BrownDogGadgets/CrazyCircuits/Projects/LEGO Avoidance Tank/README.md

# LEGO Avoidance Tank

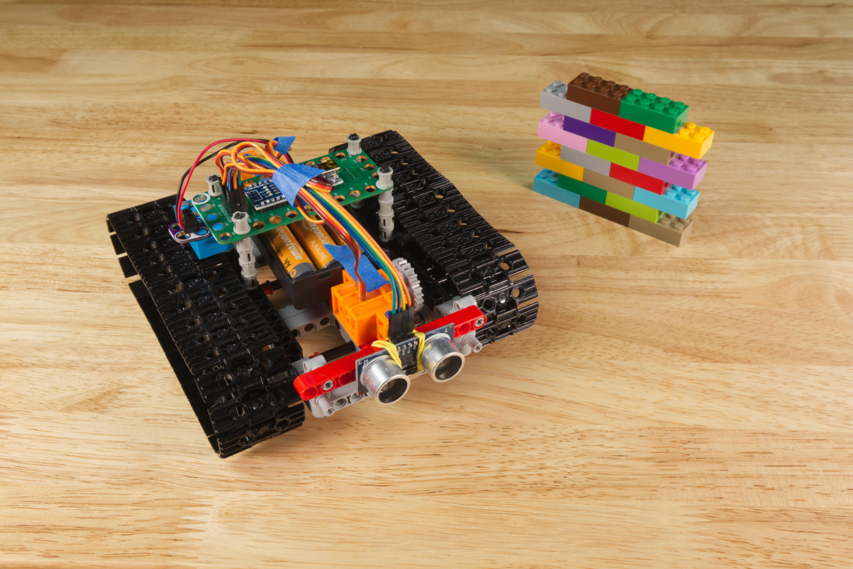
[picture p115: Projects/LEGO Avoidance Tank/Images/LEGO-Avoidance-Tank-2607.jpg]
LEGO Avoidance Tank


A LEGO Tank that uses an Ultrasonic Distance Sensor to prevent crashing into things.

Built with Crazy Circuits components and LEGO parts.

We have a full build guide listing all of the components and every LEGO part needed: https://browndoggadgets.dozuki.com/Guide/LEGO+Avoidance+Tank/383

The Arduino sketch `LEGO-Avoidance-Tank` is included.

You will also need the NewPing library, which can be found here: https://bitbucket.org/teckel12/arduino-new-ping/wiki/Home

---

Brown Dog Gadgets

https://www.browndoggadgets.com/
