BrownDogGadgets/CrazyCircuits/Projects/LEGO Hole Punch/README.md

# LEGO Hole Punch Stencils

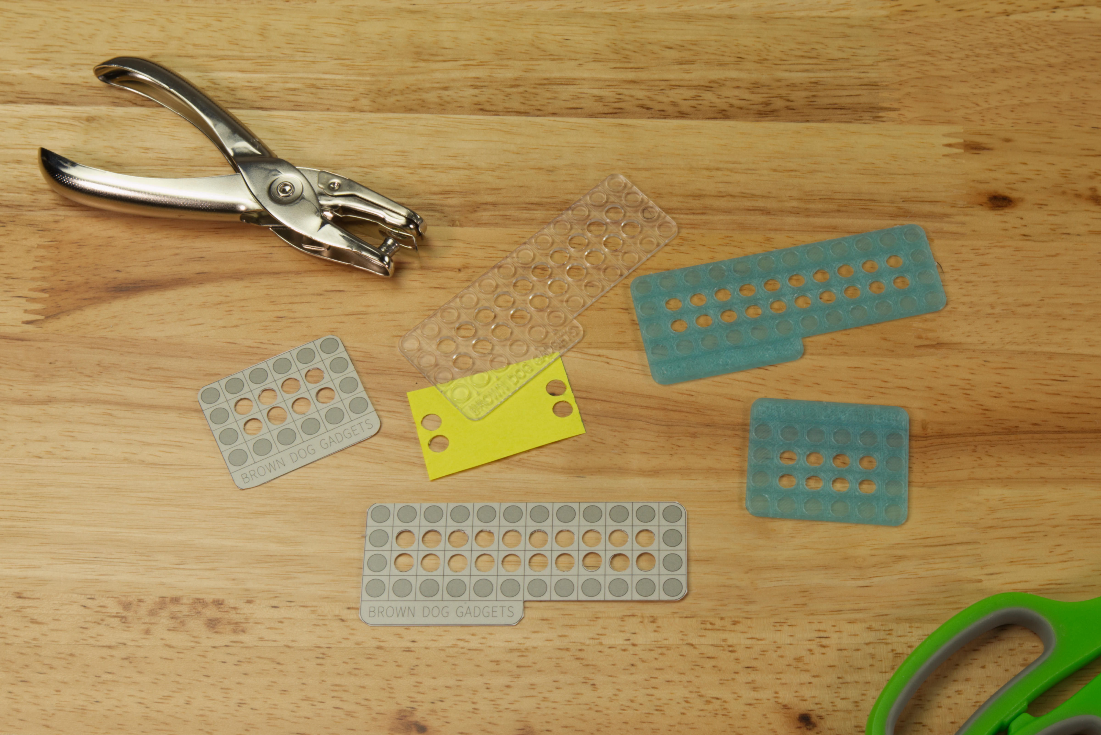
[picture p116: Projects/LEGO Hole Punch/Images/LEGO-Hole-Punch-Stencils.jpg]


A variety of LEGO Hole Punch Stencils suitable for laser cutting, 3D printing, or just printing on paper and cutting out.

Full Guide: https://browndoggadgets.dozuki.com/Guide/LEGO+Hole+Punch+Stencils/380

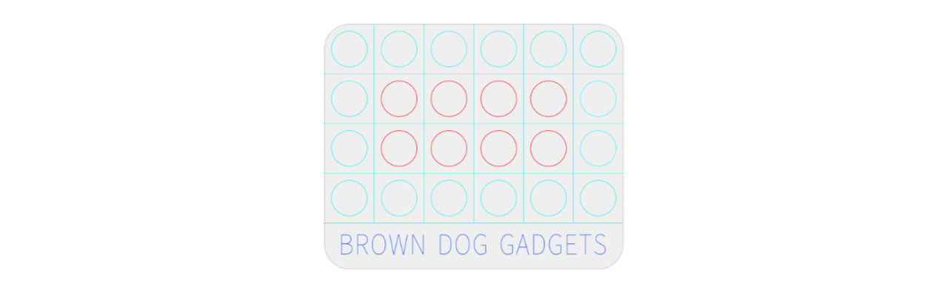
[picture p117: Projects/LEGO Hole Punch/Images/Laser.png]
Laser


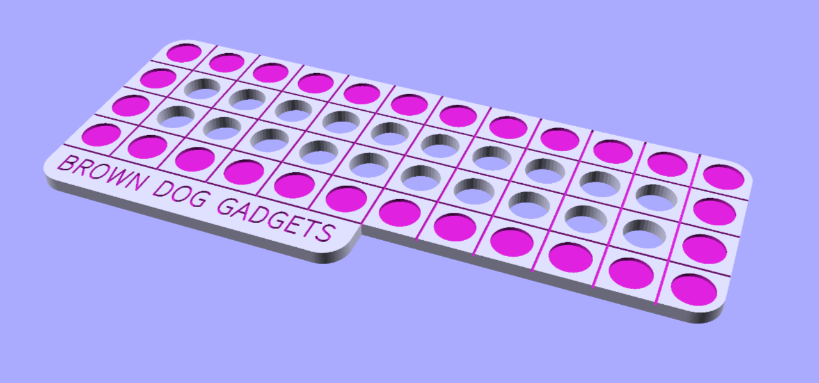
[picture p118: Projects/LEGO Hole Punch/Images/STL.png]
STL


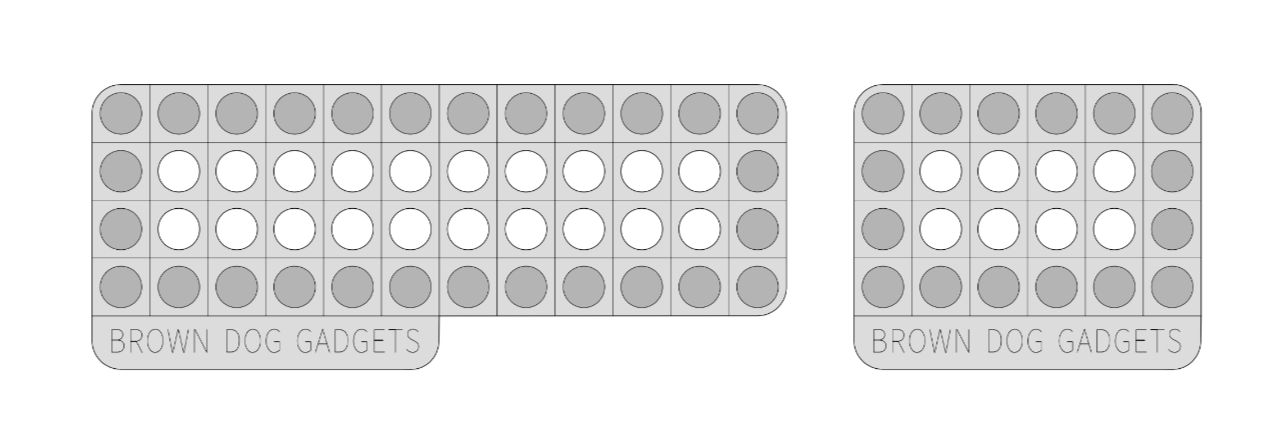
[picture p119: Projects/LEGO Hole Punch/Images/Paper.png]
Paper


---

Brown Dog Gadgets

https://www.browndoggadgets.com/
