BrownDogGadgets/CrazyCircuits/Projects/Arduino Maze/Readme.md

# Arduino LEGO Maze

This project uses the Crazy Circuits Robotics Board to activate a servo in a LEGO maze.

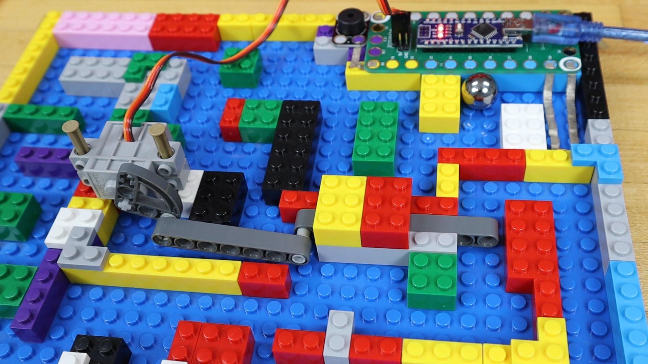
[picture p120: Projects/Arduino Maze/legomaze.jpg]
LEGO Maze


Overall this is a very simple project. We're using two pieces of Maker Tape conductive tape to act as our switch and then using a metal ball bearing to activitive the switch, which in turn activates the servo.

To add some extra fun to the activity we also added in a Piezo Speaker as a countdown timer.

In the example picture we're using a LEGO friendly Geek Servo, through there are many different DIY LEGO Adaptors that can be laser cut and 3D printed for a standard 9G servo.

See the full build guide: https://browndoggadgets.dozuki.com/Guide/LEGO+Maze/68

---

Brown Dog Gadgets

https://www.browndoggadgets.com/
