BrownDogGadgets/CrazyCircuits/Projects/CLUEbell/README.md

# CLUEbell

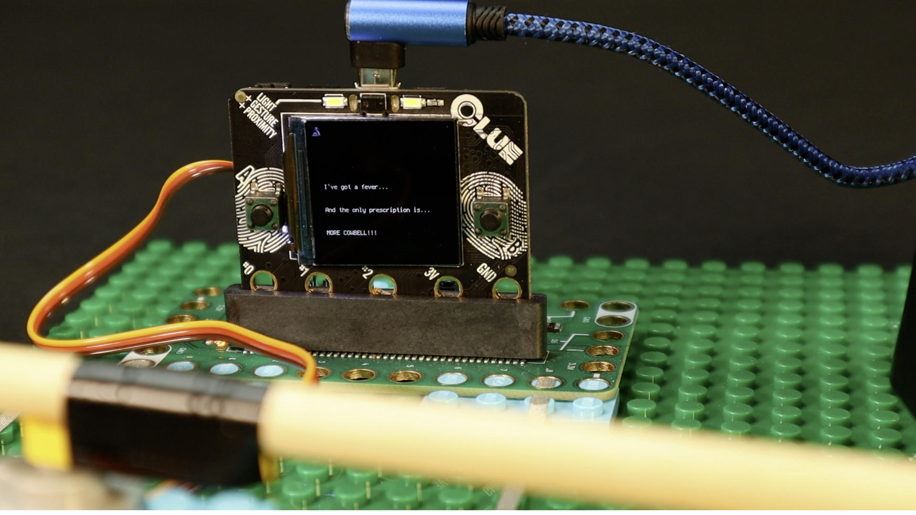
[picture p121: Projects/CLUEbell/Images/cluebell-01.jpg]


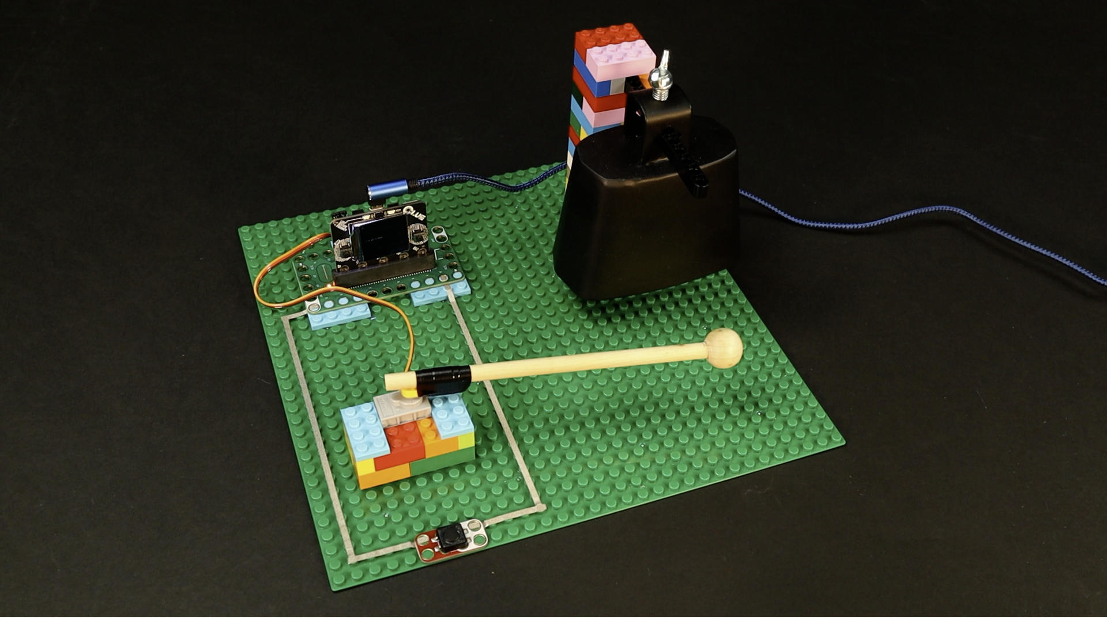
[picture p122: Projects/CLUEbell/Images/cluebell-02.jpg]


The **CLUEbell** is a Crazy Circuits LEGO-based project using a Bit Board and an Adafruit Clue.

## Adafruit Clue

The code is written in CircuitPython and to use it as-is just copy it to the Clue after you connect it to your computer with a USB cable.

This is based on our "Automatic Cowbell" project: https://browndoggadgets.dozuki.com/Guide/Automatic+Cowbell/361

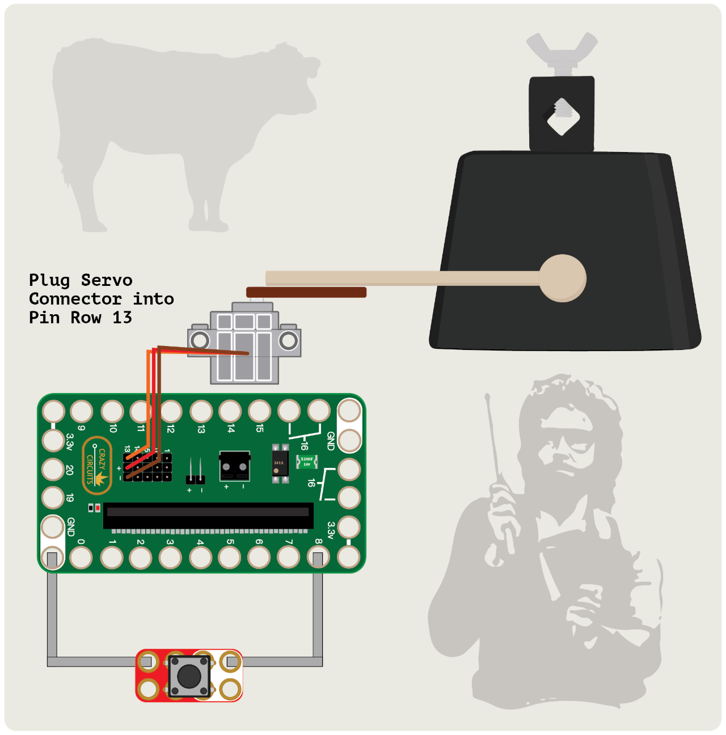
[picture p123: Projects/CLUEbell/Diagrams/cluebell-circuit.png]


---

Brown Dog Gadgets

https://www.browndoggadgets.com/
