BrownDogGadgets/CrazyCircuits/Projects/L-egg-o Egg Decorating Robot/README.md

# L-egg-o Egg Decorating Robot

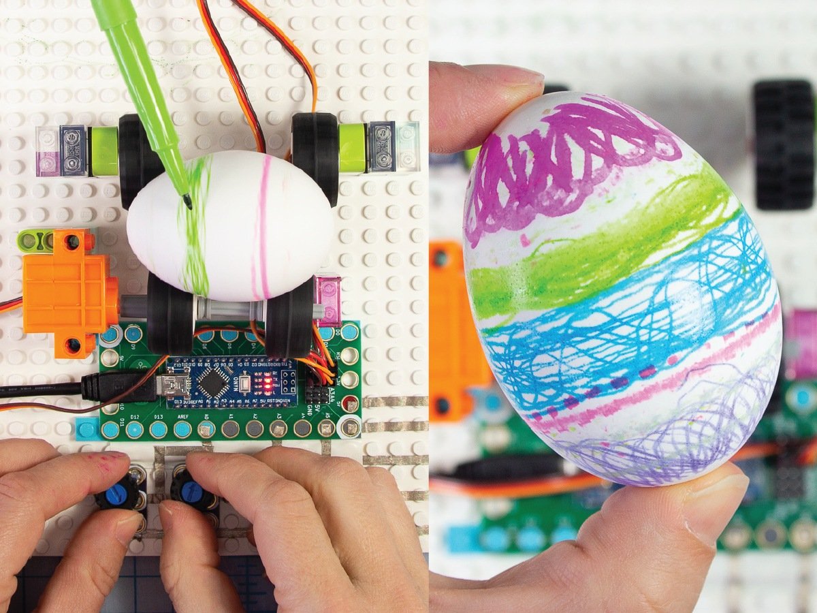
[picture p130: Projects/L-egg-o Egg Decorating Robot/Images/l-egg-o-decobot.jpg]


Full instructions here: https://browndoggadgets.dozuki.com/Guide/"L-egg-o"+Egg+Decorating+Robot/175

You'll need to use the Arduino sketch `Leggo_Mazing_Smooth.ino`

(https://www.youtube.com/watch?v=7hJQVjtKovQ)

---

Brown Dog Gadgets

https://www.browndoggadgets.com/
