BrownDogGadgets/CrazyCircuits/Projects/SquishySound/readme.md

Two sets of noise making code for a simple Squishy Circuits sound project.

Use a Touch or Robotics Board, a Piezo Speaker, and a Screw Terminal with a 460 ohm resistor. (Or a resistor close to it.)

Attach alligator clips and use dough to change the sounds.
