BrownDogGadgets/CrazyCircuits/Projects/Touch LED/readme.md

# Crazy Touch LED

This is a simple sketch that uses four Touch Points and 4 LED outputs.

Touch a Touch Point and one of the LEDs turns on.

We designed this to be used with conductive dough as a demo project, though any conductive material would work.  You could easily modify this code to do various effects.

The code run an auto calibration sequence when turned on.  This means you should wait three seconds after powering up before touching any of the touch points.

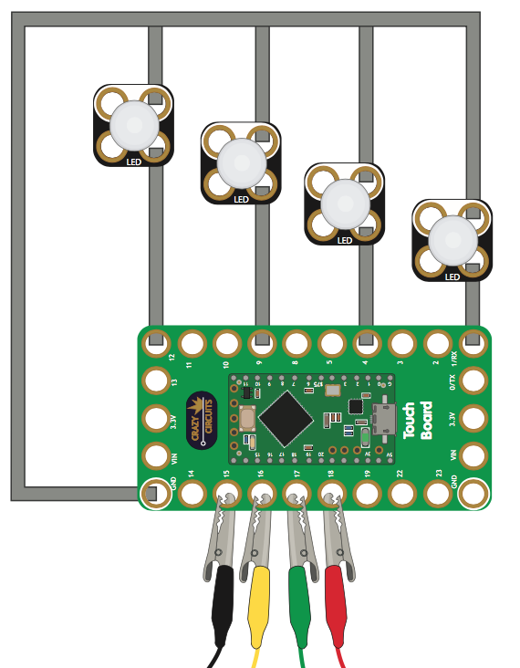
[picture p134: Projects/Touch LED/diagrampreview.png]
diagram preview
