BrownDogGadgets/CrazyCircuits/Projects/LEGO Fidget/readme.md

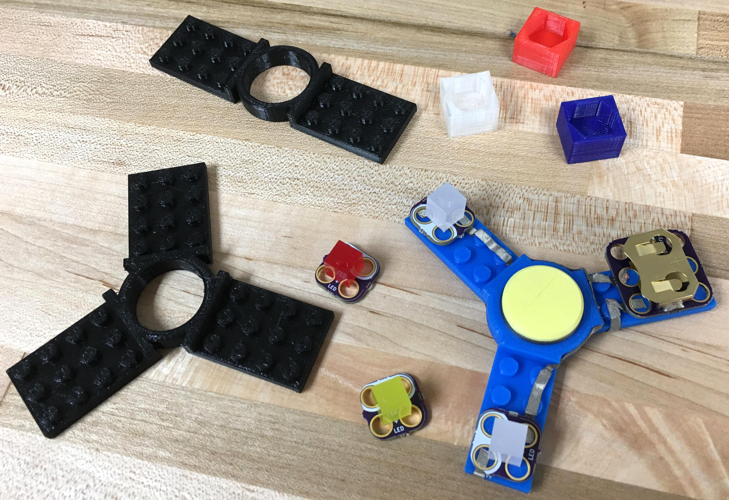
[picture p140: Projects/LEGO Fidget/spinners.jpg]


# 3D Printed LEGO Fidget Spinner

In this project we're going to use a 3D Printer to create our own custom fidget spinner, then attach Crazy Circuits parts to make it light up. We've provided several different variations to print with, changing the number of arms and the number of LEGO studs on them. There are also some additional files for adding in M8 sized Nuts as weights.

Obviously you're going to need access to a 3D printer, but if you don't one readily available you can always use online services such as Shapeways to make one for you. We used our office Makerbot Replicator 2 for printing, with a print time of around 45 minutes for a three armed spinner. If the studs are too big or too small you'll have to change the size and try again, same goes for the bearing.

We used two Cazy Circuits LEDs, a CR2032 Battery Holder, and some tape. Be sure to use two of the same color LED otherwise power will only flow through one color. (Voltage differences in different colors of LEDs can cause issues with CR2032 batteries.)

It IS possible to use a Blink/ Fade board with some of the larger 3D files, but would require some tricky tape work.

You will need to "patch" some of the tape lines in order to connect them.  This means folding over the end of a piece of tape to electricly connect everything, and then putting another piece of tape on top to hold it down. For more information on the basic of Crazy Circuits please visit

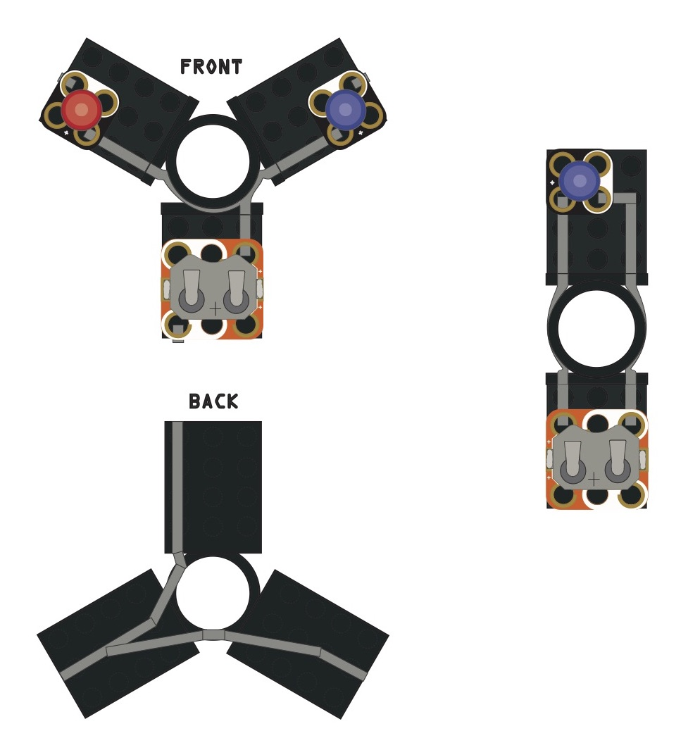
[picture p141: Projects/LEGO Fidget/WiringDiagram.jpg]


Like all good fidget spinners ours requires a 608 bearing, also known as a Skate Bearing. There are many varieties available on Amazon. For a bearing cover you can choose from a wide variety of available 3D models on Thingiverse. We used files from [this spinner](https://www.thingiverse.com/thing:1802260), but had to reduce the size a couple percentage points.
