BrownDogGadgets/CrazyCircuits/Laser Cut Files/NES Controller/readme.md

These are the laser cut files for the DIY NES Controller.

The code and building tips can be found in the Projects area of this repository.
