BrownDogGadgets/CrazyCircuits/Circuit-Kits/Modules/6x11-Raspi-Pico-Robot-Version/README.md

<!--- start title --->
# 5x11 Raspberry Pi Pico Robot Breakout v1.6
A Lego-compatible Crazy Circuits module

- Updated: 24 Sep 2018
- Website: http://browndoggadgets.com/
- Company: Brown Dog Gadgets
- License: CERN Open Hardware License v1.2.
<!--- end title --->

This robot controller module comes with an Arduino Nano, four servo headers, and two analog headers. 

We recommend buying two 20-pin Harwin connectors (P/N [M20-9992046](https://www.digikey.com/products/en?keywords=M20-9992046)) and breaking it into pieces to place the six male headers.

<!--- bom start --->
## Bill of Materials

|Ref|Qty|Description|Digikey PN|
|---|---|---|---|
|J1-6|6|HEADER MALE 3POS TH 1x03 0.1IN|952-2264-ND|
|U1|1|Raspberry Pi PICO Board|2648-SC0915CT-ND|

<!--- bom end --->

### Manufacturing Notes

This board must be v-scored. Do not panelize with support tabs or mousebites.

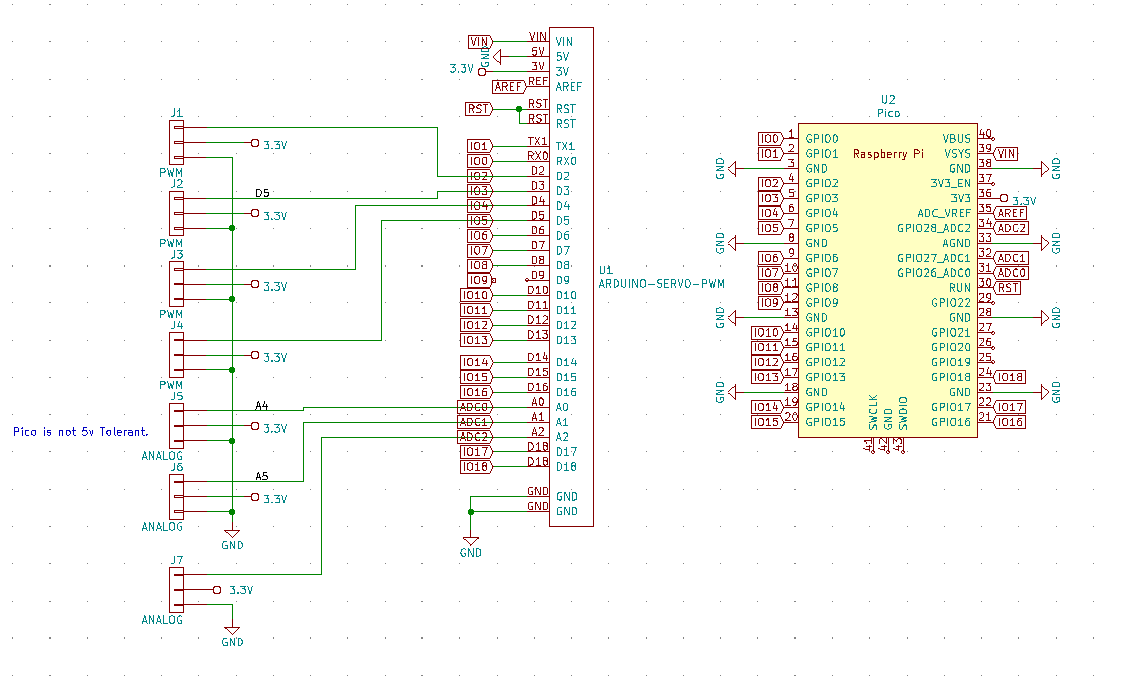
[picture p145: Circuit-Kits/Modules/6x11-Raspi-Pico-Robot-Version/schematic.png]
Assembly and Schematic


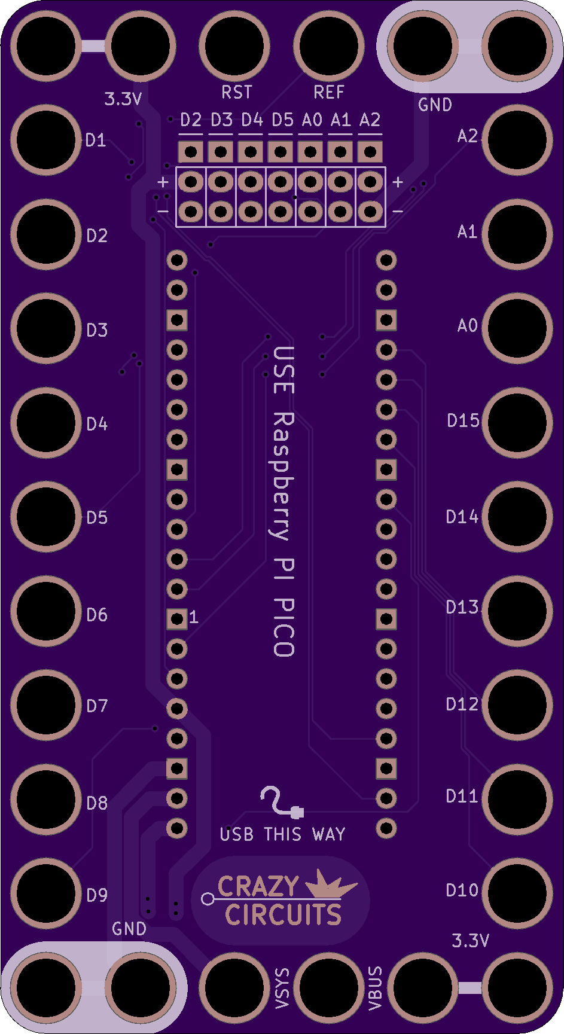
[picture p146: Circuit-Kits/Modules/6x11-Raspi-Pico-Robot-Version/top.png]
 
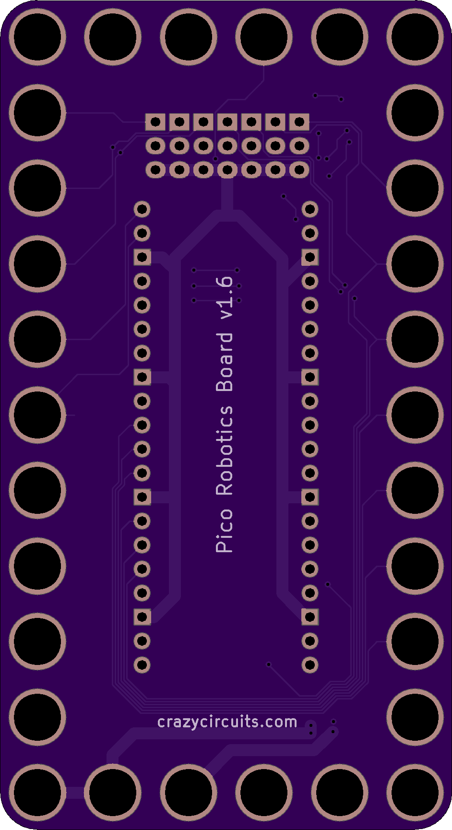
[picture p147: Circuit-Kits/Modules/6x11-Raspi-Pico-Robot-Version/bot.png]
