BrownDogGadgets/CrazyCircuits/Circuit-Kits/Modules/3x4-ATtiny85-8SOIC-Breakout/README.md

<!--- start title --->
# 3x4 ATtiny85 8SOIC Breakout Module v1.3
A Lego-compatible Crazy Circuits module

- Updated: 25 Sep 2018
- Website: http://browndoggadgets.com/
- Company: Brown Dog Gadgets
- License: CERN Open Hardware License v1.2.
<!--- end title --->

This is a breakout board for an ATiny85, a tiny microcontroller. 

<!--- bom start --->
## Bill of Materials

|Ref|Qty|Description|Digikey PN|
|---|---|---|---|
|U1|1|IC MCU 8BIT ATTINY85 8SOIC|ATTINY85-20SU-ND|

<!--- bom end --->

### Manufacturing Notes

This board must be v-scored. Do not panelize with support tabs or mousebites.

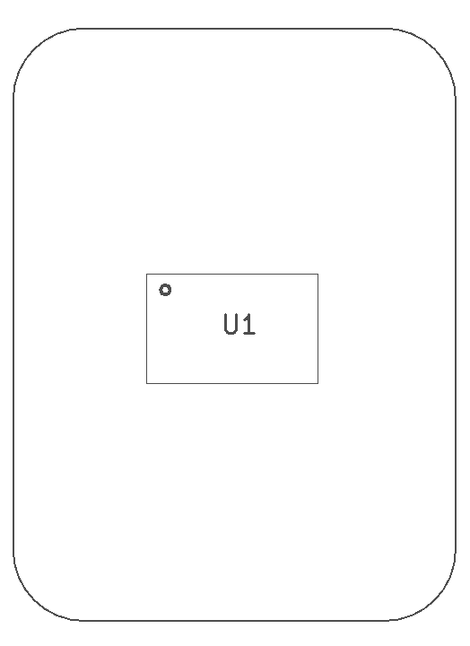
[picture p163: Circuit-Kits/Modules/3x4-ATtiny85-8SOIC-Breakout/assembly.png]
Assembly Diagram


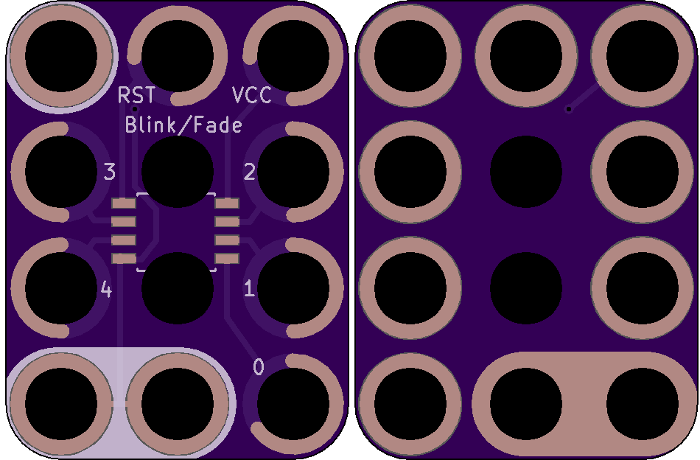
[picture p164: Circuit-Kits/Modules/3x4-ATtiny85-8SOIC-Breakout/preview.png]
Gerber Preview
