BrownDogGadgets/CrazyCircuits/Circuit-Kits/Modules/2x3-Dark-Detector/README.md

<!--- start title --->
# 2x3 Dark Detector Module v1.0
A Lego-compatible Crazy Circuits module

- Updated: 24 Sep 2018

- Website: http://browndoggadgets.com/
- Company: Brown Dog Gadgets
- License: CERN Open Hardware License v1.2
<!--- end title --->

This circuit applies 3V to turn a transistor on and off, based on whether the on-board photocell detects light. The output will go high if there is no light.

<!--- bom start --->
## Bill of Materials

|Ref|Qty|Description|Digikey PN|
|---|---|---|---|
|LDR1|1|PHOTOTRANSISTOR FLAT BK MINI SMD|1080-1383-1-ND|
|Q1|1|TRANS NPN 40V 0.2A SOT-23|MMBT3904TPMSCT-ND|
|R1|1|RES SMD 100K OHM 5% 1/10W 0603|311-100KGRCT-ND|

<!--- bom end --->

### Manufacturing Notes

This board must be v-scored. Do not panelize with support tabs or mousebites.

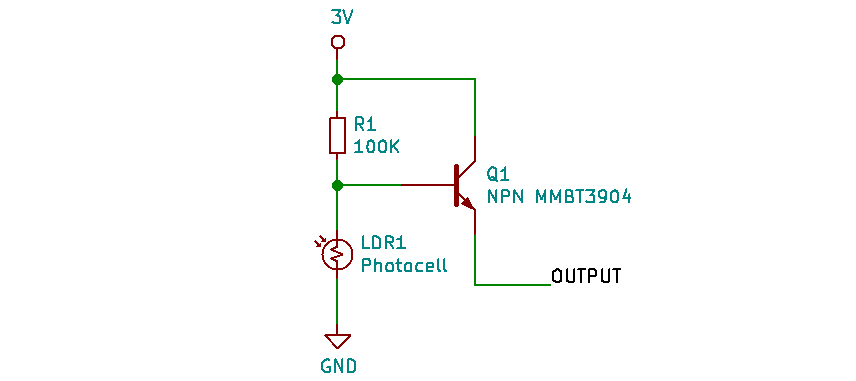
[picture p165: Circuit-Kits/Modules/2x3-Dark-Detector/schematic.png]
Schematic


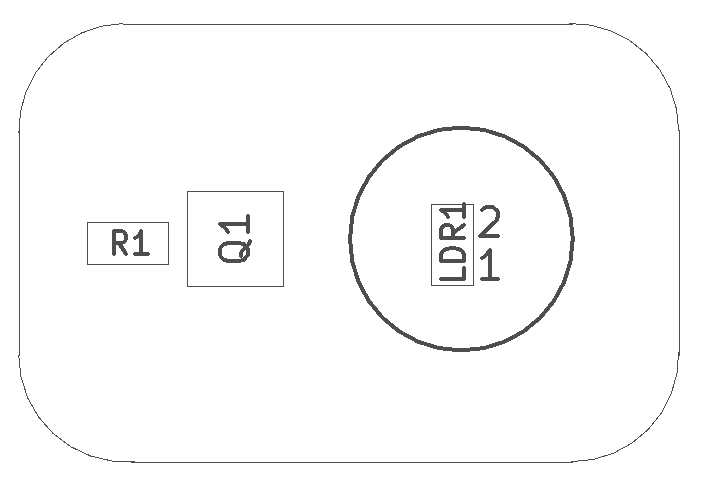
[picture p166: Circuit-Kits/Modules/2x3-Dark-Detector/assembly.png]
Assembly Diagram


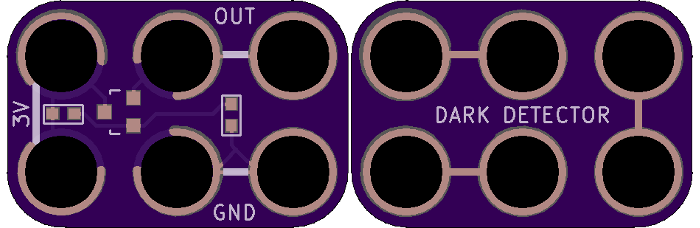
[picture p167: Circuit-Kits/Modules/2x3-Dark-Detector/preview.png]
Gerber Preview
