BrownDogGadgets/CrazyCircuits/Circuit-Kits/Modules/2x2-LED-RGB-NeoPixel-SMT/README.md

<!--- start title --->
# 2x2 LED RGB Neopixel (WS2812B) Module v1.1
A Lego-compatible Crazy Circuits module

- Updated: 24 Sep 2018

- Website: http://browndoggadgets.com/
- Company: Brown Dog Gadgets
- License: All rights reserved.
<!--- end title --->

The WS2812B is an RGB LED that's addressable using the Adafruit Neopixel library for Arduino. Neopixels can be chained together by connecting the DOUT pin of one Neopixel to the DIN pin of the next Neopixel.

An onboard 0.1uF capacitor protects the Neopixel from the controller and the 470-ohm resistor on DIN helps the microcontroller talk reliably to the Neopixel.

Find strings, strands, and rings of Neopixels at [Adafruit](http://adafruit.com).

<!--- bom start --->
## Bill of Materials

|Ref|Qty|Description|Digikey PN|
|---|---|---|---|
|C1|1|CAP CER 0.1UF 16V X7R 0603|490-4774-1-ND|
|LED1|1|LED RGB WS2812B W/DVR 4SMD|1528-1104-ND|
|R1|1|RES SMD 470 OHM 5% 1/4W 0603|RHM470DCT-ND|

<!--- bom end --->

### Manufacturing Notes

This board must be v-scored. Do not panelize with support tabs or mousebites.

Schematic

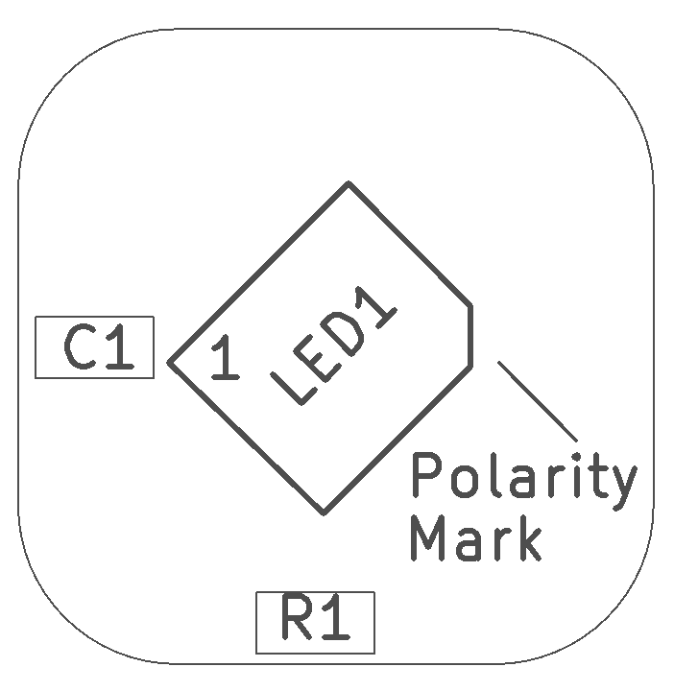
[picture p168: Circuit-Kits/Modules/2x2-LED-RGB-NeoPixel-SMT/assembly.png]
Assembly Diagram


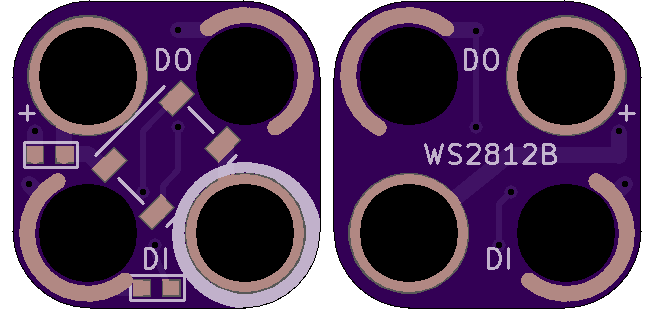
[picture p169: Circuit-Kits/Modules/2x2-LED-RGB-NeoPixel-SMT/preview.png]
Gerber Preview
