BrownDogGadgets/CrazyCircuits/Circuit-Kits/Modules/2x4-12mm-Square-SMT-Pushbutton/README.md

<!--- start title --->
# 2x4 12mm Square SMT Pushbutton Module v1.4
A Lego-compatible Crazy Circuits module

- Updated: 24 Sep 2018
- Website: http://browndoggadgets.com/
- Company: Brown Dog Gadgets
- License: CERN Open Hardware License v1.2.

<!--- end title --->

This is a large surface mount pushbutton that makes a very satisfying click.

<!--- bom start --->
## Bill of Materials

|Ref|Qty|Description|Digikey PN|
|---|---|---|---|
|SW1|1|SWITCH MOMENT SPST-NO 0.05A 24V SMT B3FS-4002P|SW1278CT-ND|

<!--- bom end --->

### Manufacturing Notes

This board must be v-scored. Do not panelize with support tabs or mousebites.

Gerber Preview
