BrownDogGadgets/CrazyCircuits/Circuit-Kits/Modules/1x3-Button-Momentary-SMT/README.md

<!--- start title --->
# 1x3 Momentary Pushbutton SMT Module v1.2
A Lego-compatible Crazy Circuits module

- Updated: 24 Sep 2018
- Website: http://browndoggadgets.com/
- Company: Brown Dog Gadgets
- License: CERN Open Hardware License v1.2.
<!--- end title --->

This is a small surface mount pushbutton.

<!--- bom start --->
## Bill of Materials

|Ref|Qty|Description|Digikey PN|
|---|---|---|---|
|SW1|1|SWITCH MOMENT SPST-NO 0.05A 12V SMT PTS645|CKN9112CT-ND|

<!--- bom end --->

### Manufacturing Notes

This board must be v-scored. Do not panelize with support tabs or mousebites.
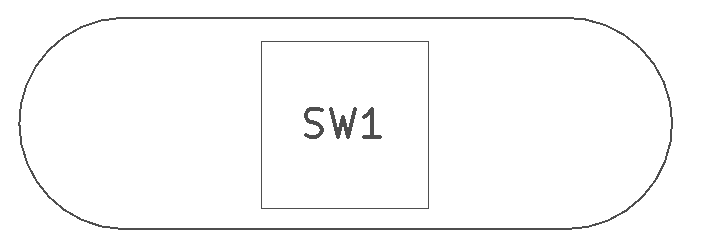
[picture p172: Circuit-Kits/Modules/1x3-Button-Momentary-SMT/assembly.png]
Assembly Diagram


Gerber Preview
