BrownDogGadgets/CrazyCircuits/Circuit-Kits/Modules/1x3-Button-Momentary/README.md

<!--- start title --->
# 1x3 Momentary Pushbutton Module v1.3
A Lego-compatible Crazy Circuits module.

- Updated: 24 Sep 2018
- Website: http://browndoggadgets.com/
- Company: Brown Dog Gadgets
- License: CERN Open Hardware License v1.2.

<!--- end title --->
This is a single momentary pushbutton module. It is normally open, so it only conducts between the two end pads when the button is pressed. 

<!--- bom start --->
## Bill of Materials

|Ref|Qty|Description|Digikey PN|
|---|---|---|---|
|SW1|1|SWITCH MOMENT SPST-NO 0.05A 24V SMT B3F-1000|SW400-ND|

<!--- bom end --->

## Manufacturing Notes

This board must be v-scored. Do not panelize with support tabs or mousebites.

Gerber Preview

Schematic
