BrownDogGadgets/CrazyCircuits/Circuit-Kits/Modules/2x3-Servo-Header/README.md

<!--- start title --->
# 2x3 Servo Header v1.4
A Lego-compatible Crazy Circuits

- Updated: 24 Sep 2018
- Website: http://browndoggadgets.com/
- Company: Brown Dog Gadgets
- License: CERN Open Hardware License v1.2.

<!--- end title --->
A simple three-pin male header breaks out a female servo connector. The servo wires are Black (GND), Red (VCC), and Orange (SIGNAL).

<!--- bom start --->
## Bill of Materials

|Ref|Qty|Description|Digikey PN|
|---|---|---|---|
|J1|1|MALE PIN HEADER 1x3 2.54MM PITCH|732-5316-ND|

<!--- bom end --->

### Manufacturing Notes

This board must be v-scored. Do not panelize with support tabs or mousebites.
Assembly Diagram

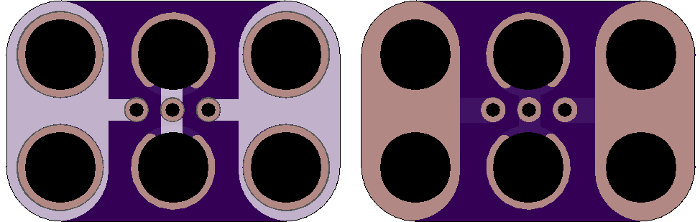
[picture p173: Circuit-Kits/Modules/2x3-Servo-Header/preview.png]
Gerber Preview
