BrownDogGadgets/CrazyCircuits/Circuit-Kits/Modules/2x3-Slide-Switch-EG1218-TH/README.md

<!--- start title --->
# 2x3 Slide Switch TH (EG1218) v1.4
A Lego-compatible Crazy Circuits module

- Updated: 24 Sep 2018
- Website: http://browndoggadgets.com/
- Company: Brown Dog Gadgets
- License: CERN Open Hardware License v1.2.
<!--- end title --->

This is a slide switch module with three positions. 

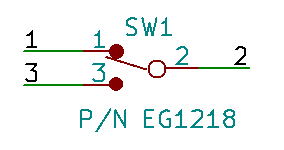
[picture p174: Circuit-Kits/Modules/2x3-Slide-Switch-EG1218-TH/schematic.png]
Schematic


<!--- bom start --->
## Bill of Materials

|Ref|Qty|Description|Digikey PN|
|---|---|---|---|
|SW1|1|SWITCH SLIDE SPDT 200MA 30V|EG1903-ND|

<!--- bom end --->

### Manufacturing Notes

This board must be v-scored. Do not panelize with support tabs or mousebites.
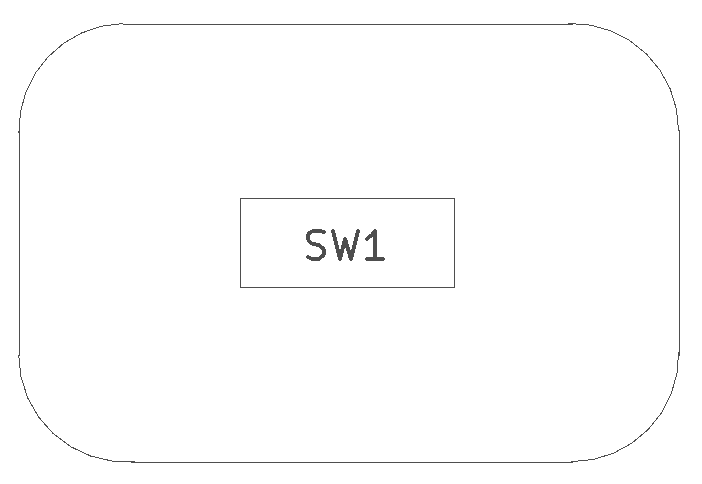
[picture p175: Circuit-Kits/Modules/2x3-Slide-Switch-EG1218-TH/assembly.png]
Assembly Diagram


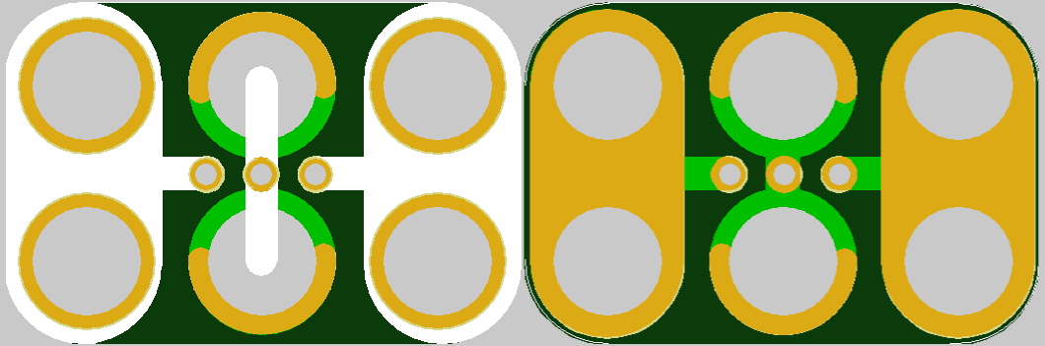
[picture p176: Circuit-Kits/Modules/2x3-Slide-Switch-EG1218-TH/preview.png]
Gerber Preview
