BrownDogGadgets/CrazyCircuits/Circuit-Kits/Modules/2x3-Slide-Switch-CL-SB-SMT/README.md

<!--- start title --->
# 2x3 Slide Switch (CL-SB) SMT v1.2
A Lego-compatible Crazy Circuits module

- Updated: 24 Sep 2018
- Website: http://browndoggadgets.com/
- Company: Brown Dog Gadgets
- License: CERN Open Hardware License v1.2.
<!--- end title --->

This is a slide switch module with three positions. 

Schematic

<!--- bom start --->
## Bill of Materials

|Ref|Qty|Description|Digikey PN|
|---|---|---|---|
|SW1|1|SWITCH SLIDE SPDT 200MA 12V CL-SB|563-1314-1-ND|

<!--- bom end --->

### Manufacturing Notes

This board must be v-scored. Do not panelize with support tabs or mousebites.
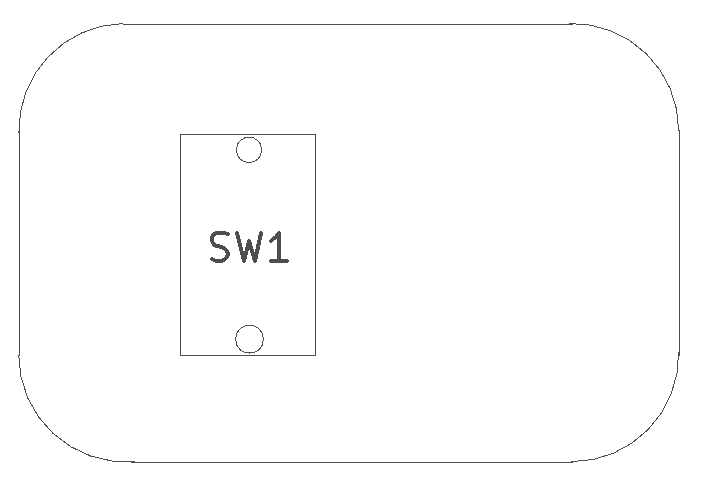
[picture p177: Circuit-Kits/Modules/2x3-Slide-Switch-CL-SB-SMT/assembly.png]
Assembly Diagram


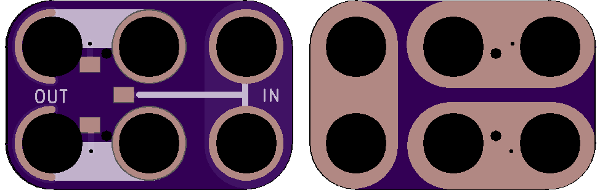
[picture p178: Circuit-Kits/Modules/2x3-Slide-Switch-CL-SB-SMT/preview.png]
Gerber Preview
