BrownDogGadgets/CrazyCircuits/Circuit-Kits/Modules/1x2-Logo-Crazy-Circuits/README.md

<!--- start title --->
# Crazy Circuits Logo Blank v1.0
Crazy Circuits logo

- Updated: 13 Feb 2017
- Website: http://browndoggadgets.com/
- Company: Brown Dog Gadgets
- License: CERN Open Hardware License v1.2.

<!--- end title --->
Just a plain logo.

### Manufacturing Notes

This board must be v-scored. Do not panelize with support tabs or mousebites.  

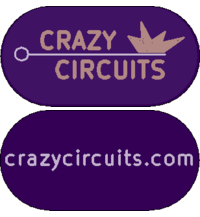
[picture p188: Circuit-Kits/Modules/1x2-Logo-Crazy-Circuits/preview.png]
Gerber Preview
