BrownDogGadgets/CrazyCircuits/Circuit-Kits/Modules/2x2-Generic-1206-SMT/README.md

<!--- start title --->
# 2x2 Generic 1206 SMT Module v1.1
A Lego-compatible Crazy Circuits module

- Updated: 27 May 2017
- Website: http://browndoggadgets.com/
- Company: Brown Dog Gadgets
- License: CERN Open Hardware License v1.2.

<!--- end title --->
This module is for any surface mount component in the 1206 package. 

### Manufacturing Notes

This board must be v-scored. Do not panelize with support tabs or mousebites.  

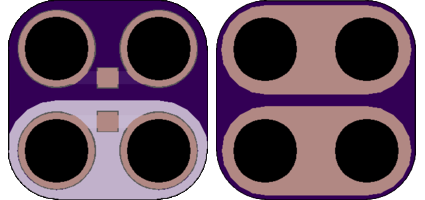
[picture p190: Circuit-Kits/Modules/2x2-Generic-1206-SMT/preview.png]
Gerber Preview
