BrownDogGadgets/CrazyCircuits/Circuit-Kits/Modules/2x2-Generic-5mm-Pitch/README.md

<!--- start title --->
# 2x2 All Purpose 5mm Pitch Module v1.1
A Lego-compatible Crazy Circuits module

- Updated: 18 Jan 2017
- Website: http://browndoggadgets.com/
- Company: Brown Dog Gadgets
- License: CERN Open Hardware License v1.2.

<!--- end title --->
This is a generic module with no markings that can be used for any two-pin, 5mm-pitch part.

### Manufacturing Notes

This board must be v-scored. Do not panelize with support tabs or mousebites.  

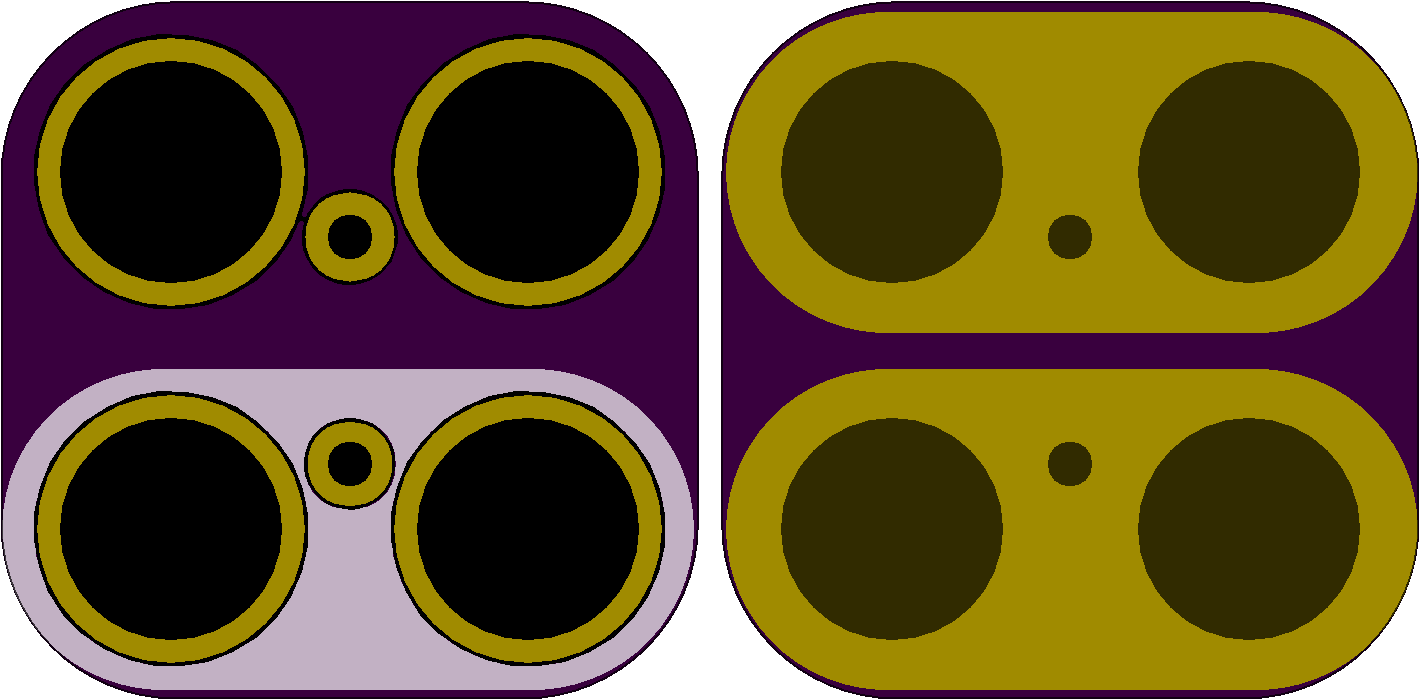
[picture p193: Circuit-Kits/Modules/2x2-Generic-5mm-Pitch/preview.png]
Gerber Preview
