BrownDogGadgets/CrazyCircuits/Circuit-Kits/Modules/2x2-LED-TH-5mm-Pitch/README.md

<!--- start title --->
# 2x2 Through-hole LED (5mm Pitch) Module v1.1
A Lego-compatible Crazy Circuits module.

- Updated: 19 Dec 2016
- Website: http://browndoggadgets.com/
- Company: Brown Dog Gadgets
- License: CERN Open Hardware License v1.2.

<!--- end title --->

There is no part currently specified for this module. Any LED with a 5mm pitch will do.

### Manufacturing Notes

This board must be v-scored. Do not panelize with support tabs or mousebites.  

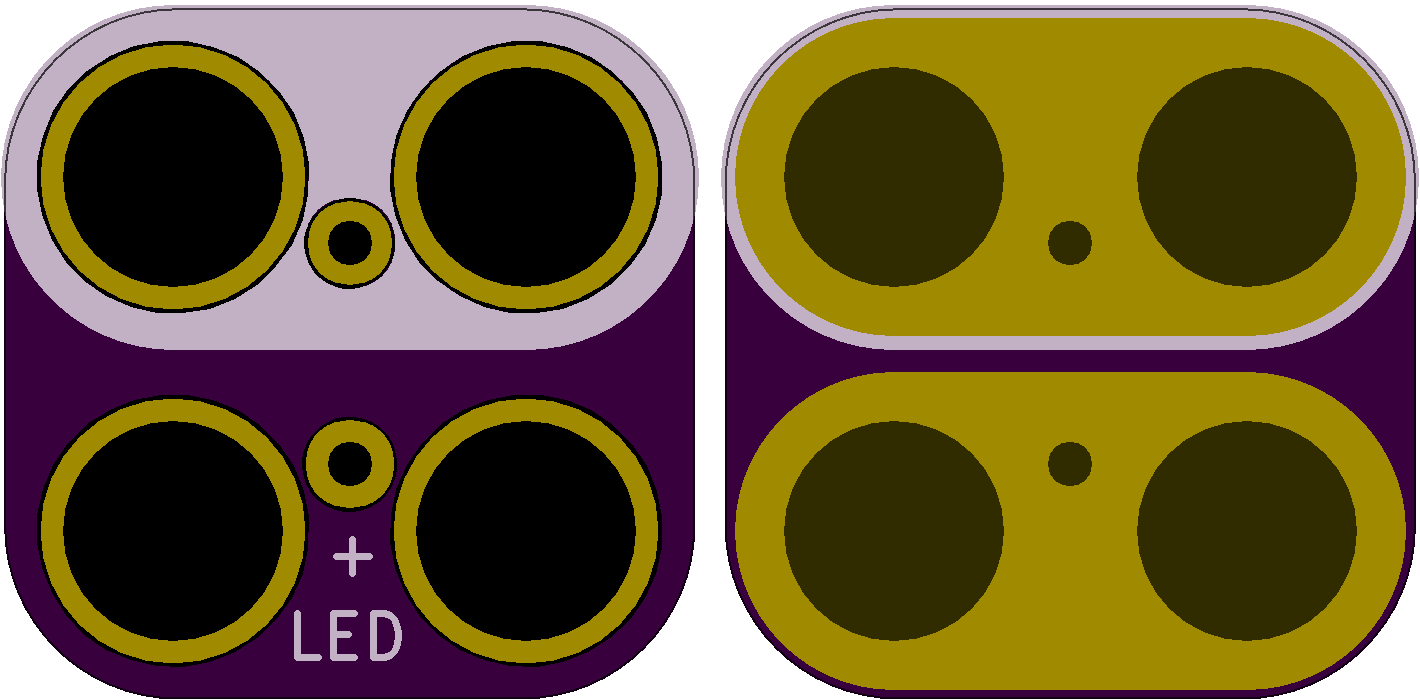
[picture p194: Circuit-Kits/Modules/2x2-LED-TH-5mm-Pitch/preview.png]
Gerber Preview
