BrownDogGadgets/CrazyCircuits/Circuit-Kits/Modules/2x3-Generic-2.54mm-Pitch-Magnet/README.md

<!--- start title --->
# 2x3 Magnet-compatible 2.54mm-pitch Module v1.1
A Lego-compatible Crazy Circuits module

- Updated: 17 Jan 2017
- Website: http://browndoggadgets.com/
- Company: Brown Dog Gadgets
- License: CERN Open Hardware License v1.2.

<!--- end title --->
This is a generic module with no markings that can be used for any two-pin, 2.54mm-pitch part. It is a 2x3 for easier connections to Crazy Circuit-compatible magnets.

### Manufacturing Notes

This board must be v-scored. Do not panelize with support tabs or mousebites.  

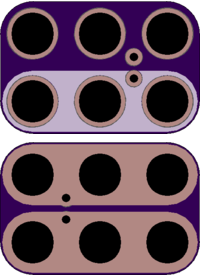
[picture p195: Circuit-Kits/Modules/2x3-Generic-2.54mm-Pitch-Magnet/preview.png]
Gerber Preview
