BrownDogGadgets/CrazyCircuits/Circuit-Kits/Modules/2x3-LED-TH-5mm-Pitch-Magnet/README.md

<!--- start title --->
# 2x3 Magnet-compatible LED (5mm Pitch) Module v1.1
A Lego-compatible Crazy Circuits module.

- Updated: 19 Dec 2016
- Website: http://browndoggadgets.com/
- Company: Brown Dog Gadgets
- License: CERN Open Hardware License v1.2.

<!--- end title --->

There is no part currently specified for this module. Any LED with 5mm pin pitch will work.

### Manufacturing Notes

This board must be v-scored. Do not panelize with support tabs or mousebites.  

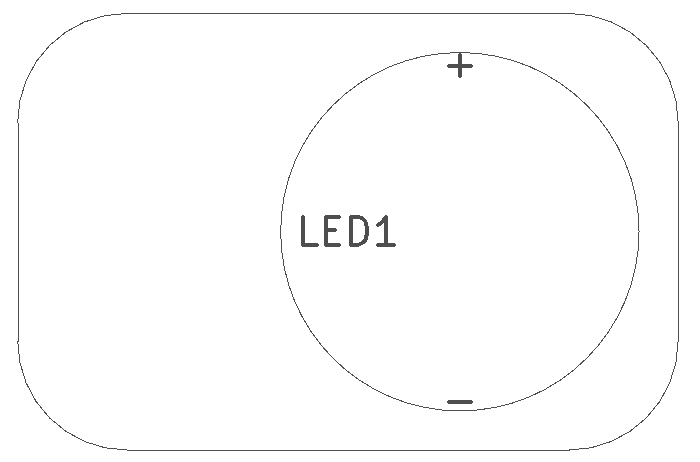
[picture p198: Circuit-Kits/Modules/2x3-LED-TH-5mm-Pitch-Magnet/assembly.png]
Assembly Diagram


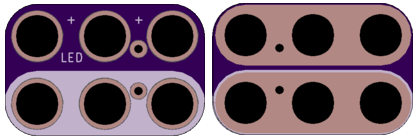
[picture p199: Circuit-Kits/Modules/2x3-LED-TH-5mm-Pitch-Magnet/preview.png]
Gerber Preview
