BrownDogGadgets/CrazyCircuits/Circuit-Kits/Modules/2x2-LED-RGB-TH-4PIN/README.md

<!--- start title --->
# 2x2 RGB LED TH Module v1.1
A Lego-compatible Crazy Circuits module

- Updated: 29 May 2017
- Website: http://browndoggadgets.com/
- Company: Brown Dog Gadgets
- License: CERN Open Hardware License v1.2.

<!--- end title --->
10mm Red-Green-Blue 4-pin LED. Align the straight edge of the LED with the Red pin. 

<!--- bom start --->
### Bill of Materials

|Ref|Qty|Description|Digikey PN|
|---|---|---|---|
|LED1|1|DIFFUSED LED - RGB 10MM|1568-1215-ND|

<!--- bom end --->

### Manufacturing Notes

This board must be v-scored. Do not panelize with support tabs or mousebites.
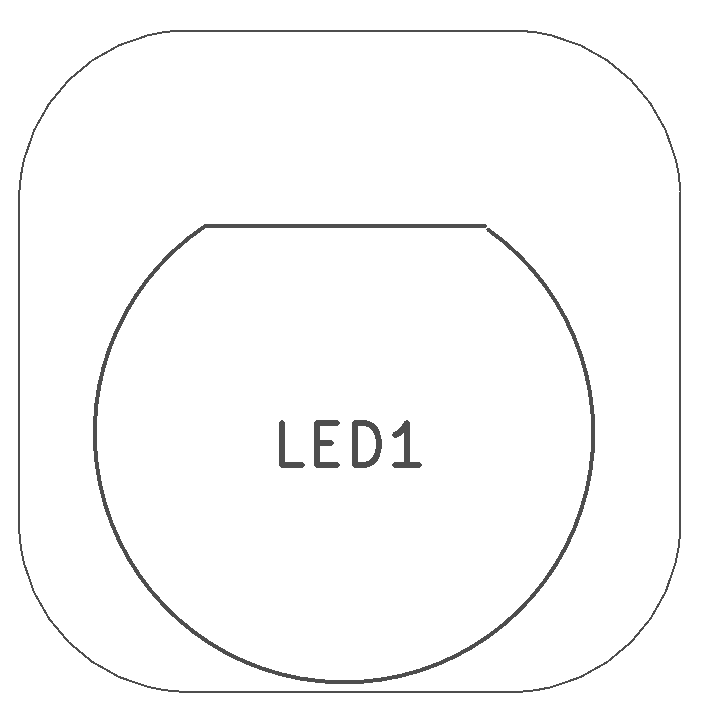
[picture p213: Circuit-Kits/Modules/2x2-LED-RGB-TH-4PIN/assembly.png]
Assembly Diagram


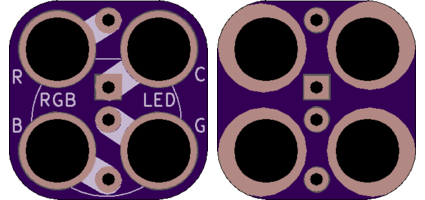
[picture p214: Circuit-Kits/Modules/2x2-LED-RGB-TH-4PIN/preview.png]
Gerber Preview
