BrownDogGadgets/CrazyCircuits/Circuit-Kits/Modules/2x2-LED-SMT/README.md

<!--- start title --->
# 2x2 SMT LED v1.2
A Lego-compatible Crazy Circuits module.

- Updated: 27 May 2017
- Website: http://browndoggadgets.com/
- Company: Brown Dog Gadgets
- License: CERN Open Hardware License v1.2.

<!--- end title --->
This is a red LED that can be wired in series with a coin cell battery.

<!--- bom start --->
### Bill of Materials

|Ref|Qty|Description|Digikey PN|
|---|---|---|---|
|LED1|1|LED RED 2V 625NM 1206 SMT|732-4991-1-ND|

<!--- bom end --->

### Manufacturing Notes

This board must be v-scored. Do not panelize with support tabs or mousebites.
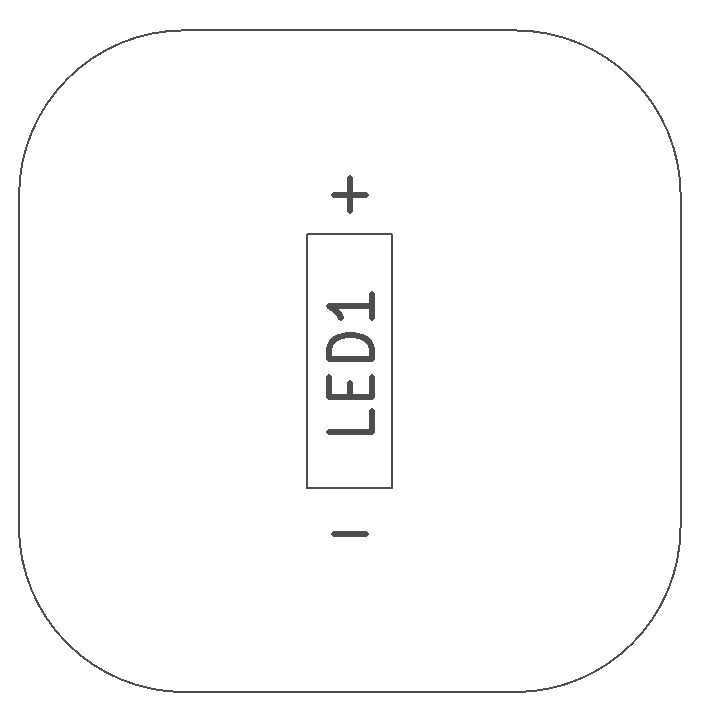
[picture p216: Circuit-Kits/Modules/2x2-LED-SMT/assembly.png]
Assembly Diagram


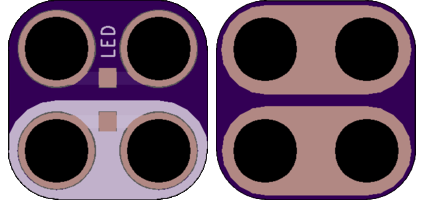
[picture p217: Circuit-Kits/Modules/2x2-LED-SMT/preview.png]
Gerber Preview
