BrownDogGadgets/CrazyCircuits/Circuit-Kits/Modules/2x2-Power-Connector-2.54mm-Pitch/README.md

<!--- start title --->
# 2x2 Through-hole LED (2.54mm Pitch) Module v1.3
A Lego-compatible Crazy Circuits module

- Updated: 27 May 2017
- Website: http://browndoggadgets.com/
- Company: Brown Dog Gadgets
- License: CERN Open Hardware License v1.2.

<!--- end title --->
This part fits any LED with 2.54mm-pitch pins. The LED can be wired in series with a coin cell battery without any other parts.

<!--- bom start --->
### Bill of Materials

|Ref|Qty|Description|Digikey PN|
|---|---|---|---|
|LED1|1|LED GREEN 10MM DIA 2.54MM PITCH|754-1898-ND|

<!--- bom end --->

### Manufacturing Notes

This board must be v-scored. Do not panelize with support tabs or mousebites.

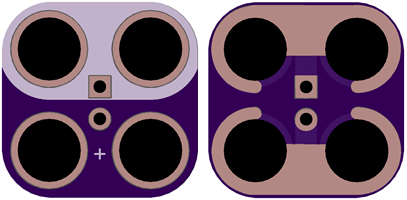
[picture p222: Circuit-Kits/Modules/2x2-Power-Connector-2.54mm-Pitch/preview.png]
Gerber Preview


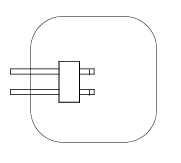
[picture p223: Circuit-Kits/Modules/2x2-Power-Connector-2.54mm-Pitch/assembly.png]
Assembly
