BrownDogGadgets/CrazyCircuits/Circuit-Kits/Modules/2x2-Servo-Header/README.md

<!--- start title --->
# 2x2 Servo Header Module v1.1
A Lego-compatible Crazy Circuits module

- Updated: 7 Oct 2017
- Website: http://browndoggadgets.com/
- Company: Brown Dog Gadgets
- License: CERN Open Hardware License v1.2.

<!--- end title --->
A simple three-pin male header breaks out a female servo connector. The servo wires are Black (GND), Red (VCC), and Orange (SIGNAL). 

<!--- bom start --->
### Bill of Materials

|Ref|Qty|Description|Digikey PN|
|---|---|---|---|
|J1|1|MALE PIN HEADER 1x3 2.54MM PITCH|732-5316-ND|

<!--- bom end --->

### Manufacturing Notes

This board must be v-scored. Do not panelize with support tabs or mousebites.

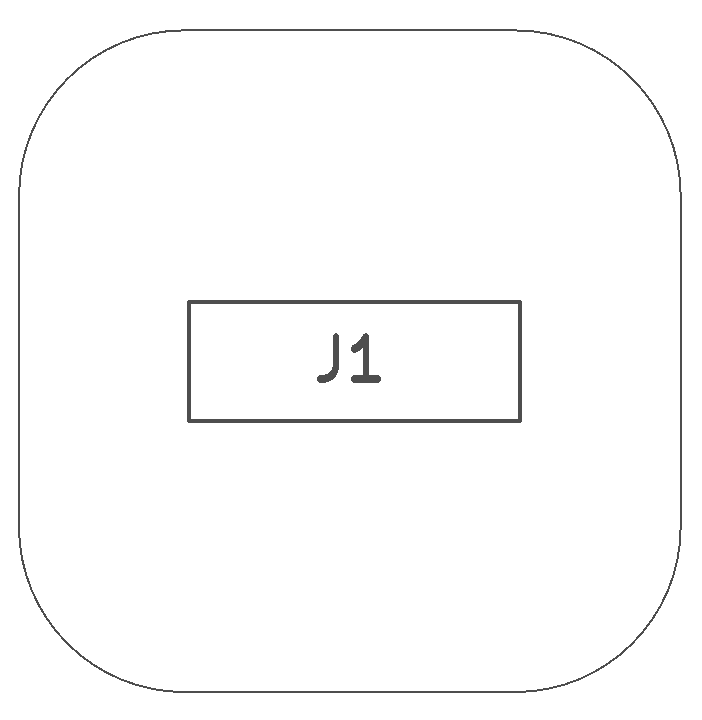
[picture p228: Circuit-Kits/Modules/2x2-Servo-Header/assembly.png]
Assembly Diagram


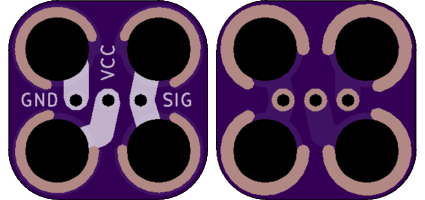
[picture p229: Circuit-Kits/Modules/2x2-Servo-Header/preview.png]
Gerber Preview
