BrownDogGadgets/CrazyCircuits/Circuit-Kits/Modules/2x2-Slide-Switch-EG1218-TH/README.md

<!--- start title --->
# 2x2 Slide Switch (EG1218) v1.2
A Lego-compatible Crazy Circuits module

- Updated: 7 Oct 2017
- Website: http://browndoggadgets.com/
- Company: Brown Dog Gadgets
- License: CERN Open Hardware License v1.2.

<!--- end title --->
This is a slide switch module with three positions. 

Schematic

<!--- bom start --->
### Bill of Materials

|Ref|Qty|Description|Digikey PN|
|---|---|---|---|
|SW1|1|SWITCH SLIDE SPDT 200MA 30V EG1218|EG1903-ND|

<!--- bom end --->

### Manufacturing Notes

This board must be v-scored. Do not panelize with support tabs or mousebites.
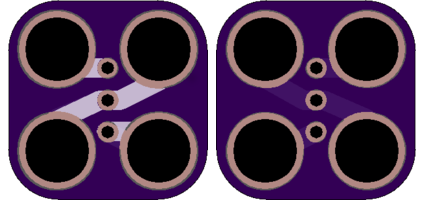
[picture p232: Circuit-Kits/Modules/2x2-Slide-Switch-EG1218-TH/preview.png]
Gerber Preview


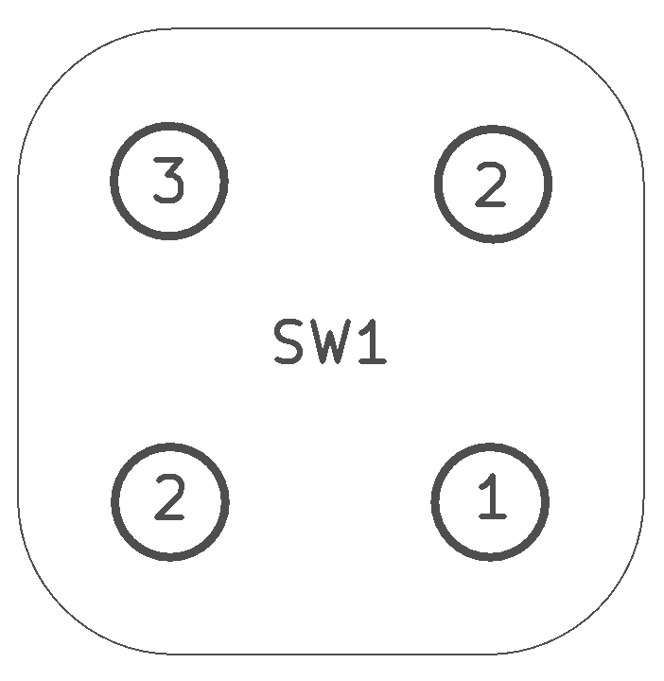
[picture p233: Circuit-Kits/Modules/2x2-Slide-Switch-EG1218-TH/assembly.png]
Assembly
