BrownDogGadgets/CrazyCircuits/Circuit-Kits/Modules/2x2-Tilt-Switch-1208-SMT/README.md

<!--- start title --->
# 2x2 Tilt Switch 1208 SMT Module v1.1
A Lego-compatible Crazy Circuits module

- Updated: 26 May 2017
- Website: http://browndoggadgets.com/
- Company: Brown Dog Gadgets
- License: CERN Open Hardware License v1.2.
<!--- end title --->

This simple tilt switch is either closed, where the two sections of copper are connected through the tilt sensor, or open, when the tilt sensor is not conducting.

<!--- bom start --->
### Bill of Materials

|Ref|Qty|Description|Digikey PN|
|---|---|---|---|
|SW1|1|TILT SENSOR 2 PIN PKGS-25SXAP1-R|490-12110-1-ND|

<!--- bom end --->

### Manufacturing Notes

This board must be v-scored. Do not panelize with support tabs or mousebites.
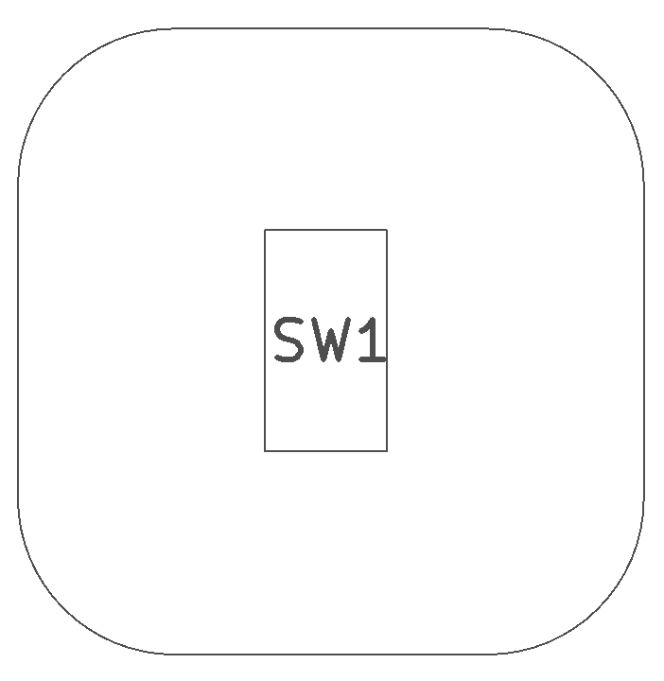
[picture p234: Circuit-Kits/Modules/2x2-Tilt-Switch-1208-SMT/assembly.png]
Assembly Diagram


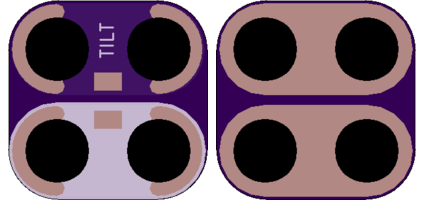
[picture p235: Circuit-Kits/Modules/2x2-Tilt-Switch-1208-SMT/preview.png]
Gerber Preview
