BrownDogGadgets/CrazyCircuits/Circuit-Kits/Modules/2x2-Tilt-Switch-TH/README.md

<!--- start title --->
# 2x2 Tilt Switch TH v1.2
A Lego-compatible Crazy Circuits module

- Updated: 7 Oct 2017
- Website: http://browndoggadgets.com/
- Company: Brown Dog Gadgets
- License: CERN Open Hardware License v1.2.
<!--- end title --->

This simple tilt switch is either closed or open, depending on which end of the tube the ball has rolled down.

<!--- bom start --->
### Bill of Materials

|Ref|Qty|Description|Mouser PN|
|---|---|---|---|
|SW1|1|TILT SENSOR ROLLING BALL 107-2006-EV|107-2006-EV|

<!--- bom end --->

### Manufacturing Notes

This board must be v-scored. Do not panelize with support tabs or mousebites.
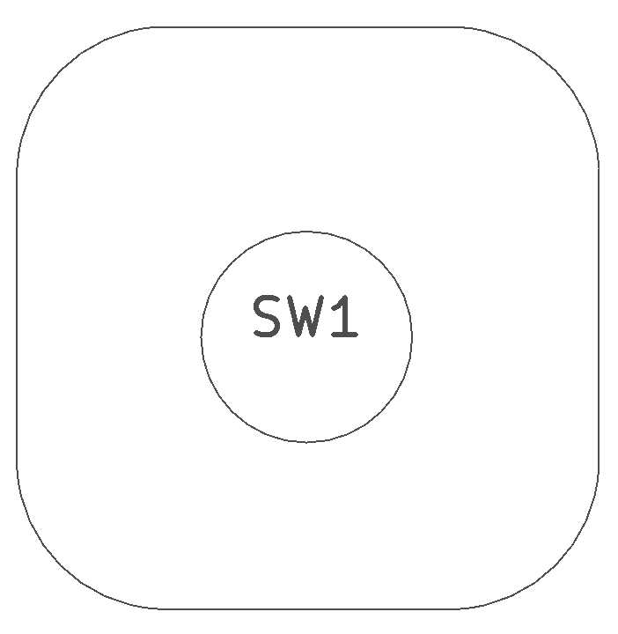
[picture p238: Circuit-Kits/Modules/2x2-Tilt-Switch-TH/assembly.png]
Assembly Diagram


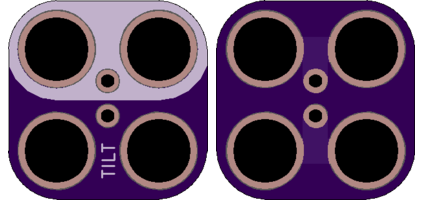
[picture p239: Circuit-Kits/Modules/2x2-Tilt-Switch-TH/preview.png]
Gerber Preview
