BrownDogGadgets/CrazyCircuits/Circuit-Kits/Modules/2x3-LED-RGB-A-SMT/README.md

<!--- start title --->
# 2x3 LED RGB (A) SMT v1.1
A Lego-compatible Crazy Circuits module

- Updated: 31 May 2018

- Website: http://browndoggadgets.com/
- Company: Brown Dog Gadgets
- License: CERN Open Hardware License v1.2.
<!--- end title --->

Surface mount RGB LED with a common anode. Connect the Common (C) to 3.3V.

<!--- bom start --->
### Bill of Materials

|Ref|Qty|Description|Digikey PN|
|---|---|---|---|
|LED1|1|LED CHIP RGB 19-237 A01/2T SMD |19-237/R6GHBHC-A01/2T-ND|
|R1 R2|2|RES SMD 100 OHM 1% 1/10W 0603|A106047CT-ND|
|R3|1|RES 47 OHM 5% 1/10W 0603|311-47GRCT-ND|

<!--- bom end --->

### Manufacturing Notes

This board must be v-scored. Do not panelize with support tabs or mousebites.
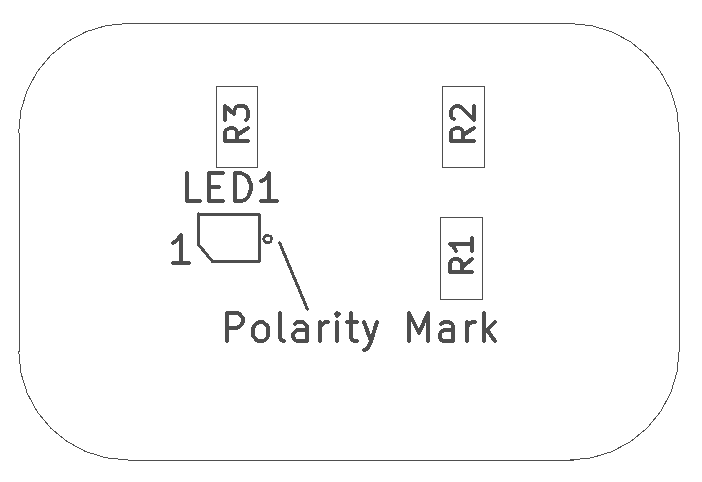
[picture p244: Circuit-Kits/Modules/2x3-LED-RGB-A-SMT/assembly.png]
Assembly Diagram


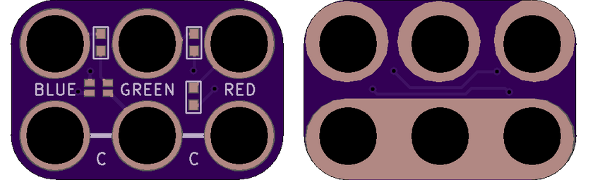
[picture p245: Circuit-Kits/Modules/2x3-LED-RGB-A-SMT/preview.png]
Gerber Preview
