BrownDogGadgets/CrazyCircuits/Circuit-Kits/Modules/2x3-LED-RGB-SMT/README.md

<!--- start title --->
# 2x3 LED RGB SMT v1.1
A Lego-compatible Crazy Circuits module

- Updated: 29 May 2017
- Website: http://browndoggadgets.com/
- Company: Brown Dog Gadgets
- License: CERN Open Hardware License v1.2.

<!--- end title --->
Surface mount RGB LED with a common anode. Connect the Common (C) to 3.3V.

<!--- bom start --->
### Bill of Materials

|Ref|Qty|Description|Digikey PN|
|---|---|---|---|
|LED1|1|LED CHIP RGB WTR CLR 0606 SMD|1516-1184-1-ND|

<!--- bom end --->

### Manufacturing Notes

This board must be v-scored. Do not panelize with support tabs or mousebites.
Schematic

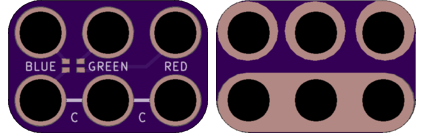
[picture p249: Circuit-Kits/Modules/2x3-LED-RGB-SMT/preview.png]
Gerber Preview


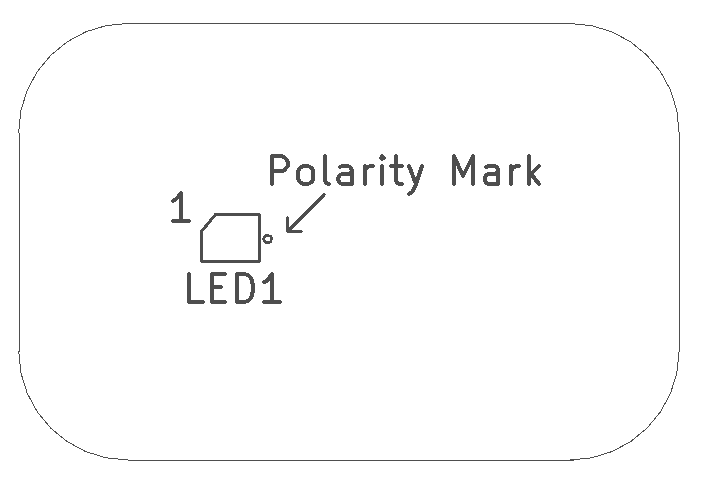
[picture p250: Circuit-Kits/Modules/2x3-LED-RGB-SMT/assembly.png]
Assembly
