BrownDogGadgets/CrazyCircuits/Circuit-Kits/Modules/2x3-LED-TH-2.54mm-Pitch-Magnet/README.md

<!--- start title --->
# 2x3 Magnet-compatible LED (2.54mm Pitch) v1.3
A Lego-compatible Crazy Circuits module

- Updated: 7 Oct 2017
- Website: http://browndoggadgets.com/
- Company: Brown Dog Gadgets
- License: CERN Open Hardware License v1.2.

<!--- end title --->

This part fits any LED with 2.54mm-pitch pins. The LED can be wired in series with a coin cell battery without any other parts.

<!--- bom start --->
### Bill of Materials

|Ref|Qty|Description|Digikey PN|
|---|---|---|---|
|LED1|1|LED GREEN 10MM DIA 2.54MM PITCH TH|754-1898-ND|

<!--- bom end --->

### Manufacturing Notes

This board must be v-scored. Do not panelize with support tabs or mousebites.
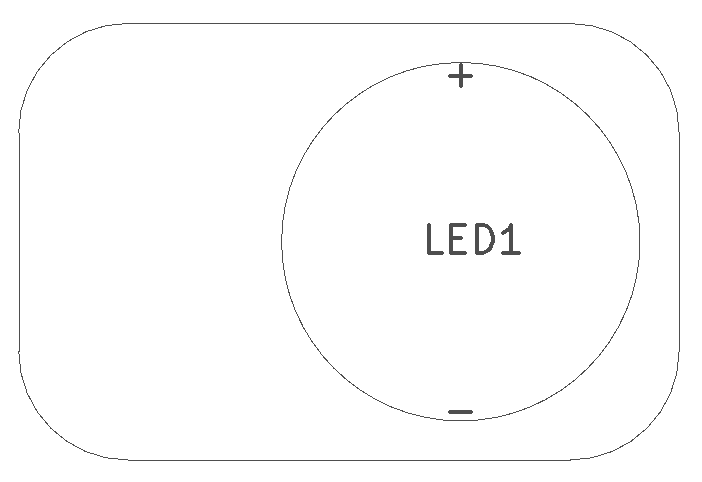
[picture p251: Circuit-Kits/Modules/2x3-LED-TH-2.54mm-Pitch-Magnet/assembly.png]
Assembly Diagram


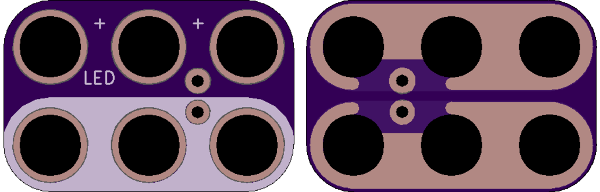
[picture p252: Circuit-Kits/Modules/2x3-LED-TH-2.54mm-Pitch-Magnet/preview.png]
Gerber Preview
