BrownDogGadgets/CrazyCircuits/Circuit-Kits/Modules/2x3-Mini-Potentiometer-3361P-SMT/README.md

<!--- start title --->
# 2x3 Mini Potentiometer 3361P SMT Module v1.1
A Lego-compatible Crazy Circuits module

- Updated: 28 May 2017
- Website: http://browndoggadgets.com/
- Company: Brown Dog Gadgets
- License: CERN Open Hardware License v1.2.
<!--- end title --->

This is a small 10K trim potentiometer that requires a little screwdriver to increase or decrease the resistance. 

<!--- bom start --->
### Bill of Materials

|Ref|Qty|Description|Digikey PN|
|---|---|---|---|
|R1|1|TRIMMER 10K OHM 0.5W SMD|3361P-103GLFCT-ND|

<!--- bom end --->

### Manufacturing Notes

This board must be v-scored. Do not panelize with support tabs or mousebites.
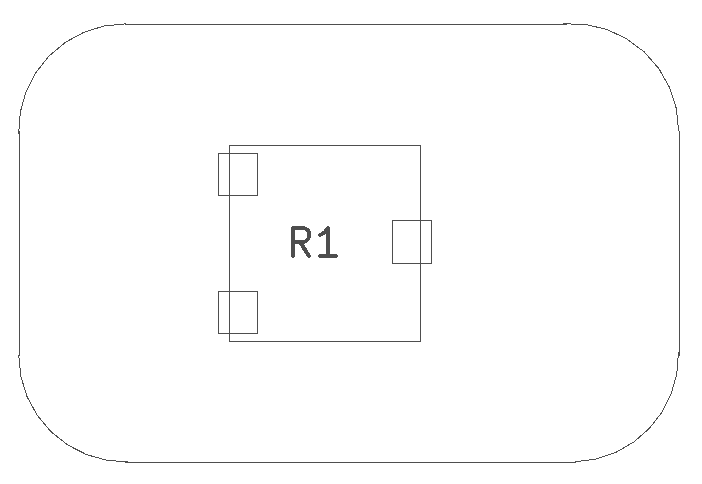
[picture p253: Circuit-Kits/Modules/2x3-Mini-Potentiometer-3361P-SMT/assembly.png]
Assembly Diagram


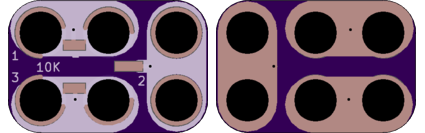
[picture p254: Circuit-Kits/Modules/2x3-Mini-Potentiometer-3361P-SMT/preview.png]
Gerber Preview
