BrownDogGadgets/CrazyCircuits/Circuit-Kits/Modules/2x3-Speaker-SMT-11mm-Pitch/README.md

<!--- start title --->
# 2x3 Speaker 11mm Pitch Module v1.1
A Lego-compatible Crazy Circuits module

- Updated: 27 May 2017
- Website: http://browndoggadgets.com/
- Company: Brown Dog Gadgets
- License: CERN Open Hardware License v1.2.
<!--- end title --->

This module is a simple bidirectional Piezo speaker that makes sound when voltage is applied. You can connect it in either direction.

<!--- bom start --->
### Bill of Materials

|Ref|Qty|Description|Digikey PN|
|---|---|---|---|
|SPK1|1|SPEAKER PIEZO 25V SMD PKLCS1212E4001-R1|490-4683-1-ND|

<!--- bom end --->

### Manufacturing Notes

This board must be v-scored. Do not panelize with support tabs or mousebites.
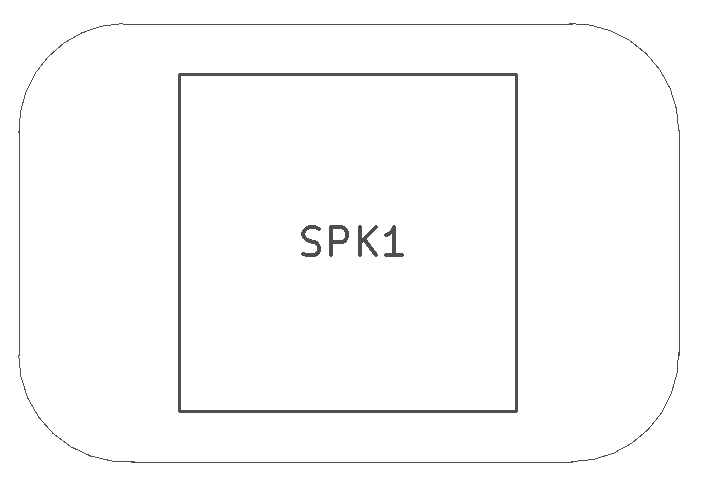
[picture p264: Circuit-Kits/Modules/2x3-Speaker-SMT-11mm-Pitch/assembly.png]
Assembly Diagram


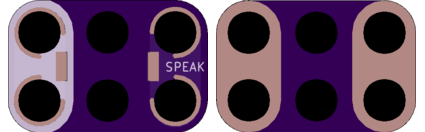
[picture p265: Circuit-Kits/Modules/2x3-Speaker-SMT-11mm-Pitch/preview.png]
Gerber Preview
