BrownDogGadgets/CrazyCircuits/Circuit-Kits/Modules/2x3-Speaker-TH-5mm-Pitch/README.md

<!--- start title --->
# 2x3 Piezo Speaker (5mm Pitch) Module v1.1
A Lego-compatible Crazy Circuits module

- Updated: 27 May 2017
- Website: http://browndoggadgets.com/
- Company: Brown Dog Gadgets
- License: CERN Open Hardware License v1.2.

<!--- end title --->
This module is a simple bidirectional Piezo speaker that makes sound when voltage is applied. You can hook it up in either direction.

<!--- bom start --->
### Bill of Materials

|Ref|Qty|Description|Digikey PN|
|---|---|---|---|
|SPK1|1|AUDIO SPEAKER PIEZO TH PS1240|445-2525-1-ND|

<!--- bom end --->

### Manufacturing Notes

This board must be v-scored. Do not panelize with support tabs or mousebites.

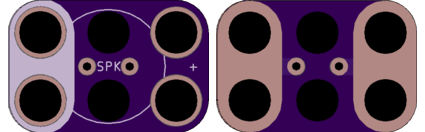
[picture p266: Circuit-Kits/Modules/2x3-Speaker-TH-5mm-Pitch/preview.png]
Gerber Preview
