BrownDogGadgets/CrazyCircuits/Circuit-Kits/Modules/2x3-Vibe-Motor-TH/README.md

<!--- start title --->
# 2x3 Vibe Motor Module v1.1
A Lego-compatible Crazy Circuits module

- Updated: 7 Oct 2017
- Website: http://browndoggadgets.com/
- Company: Brown Dog Gadgets
- License: CERN Open Hardware License v1.2.

<!--- end title --->
Small motor that vibrates. Bidirectional.

<!--- bom start --->
### Bill of Materials

|Ref|Qty|Description|Precision Microdrives PN|
|---|---|---|---|
|M1|1|MOTOR VIBE PCB 6MM - 10MM TYPE|306-114|

<!--- bom end --->

### Manufacturing Notes

This board must be v-scored. Do not panelize with support tabs or mousebites.
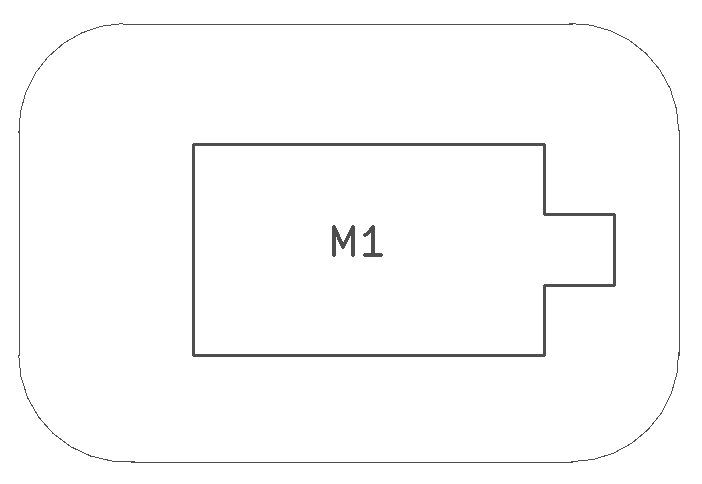
[picture p269: Circuit-Kits/Modules/2x3-Vibe-Motor-TH/assembly.png]
Assembly Diagram


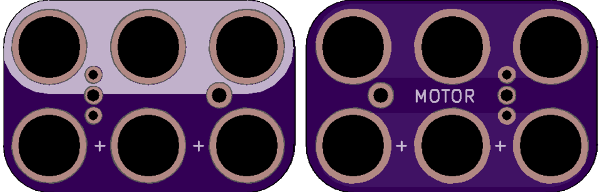
[picture p270: Circuit-Kits/Modules/2x3-Vibe-Motor-TH/preview.png]
Gerber Preview
