BrownDogGadgets/CrazyCircuits/Circuit-Kits/Modules/2x4-Grove-Sensor-Inline/README.md

<!--- start title --->
# 2x4 Grove Sensor (Inline) v1.0
A Lego-compatible Crazy Circuits module

- Updated: 9 Feb 2018

- Website: http://browndoggadgets.com/
- Company: Brown Dog Gadgets
- License: CERN Open Hardware License v1.2.
<!--- end title --->

Breaks out the Seeed Grove sensor connector so you can add Seeed Grove sensors to your project. This is a slightly different pinout than our [regular version](../2x4-Grove-Sensor/).

<!--- bom start --->
### Bill of Materials

|Ref|Qty|Description|Digikey PN|
|---|---|---|---|
|J1|1|HEADER MALE 4POS TH 1x04 SEEED GROVE|1597-1082-ND|

<!--- bom end --->

### Manufacturing Notes

This board must be v-scored. Do not panelize with support tabs or mousebites.
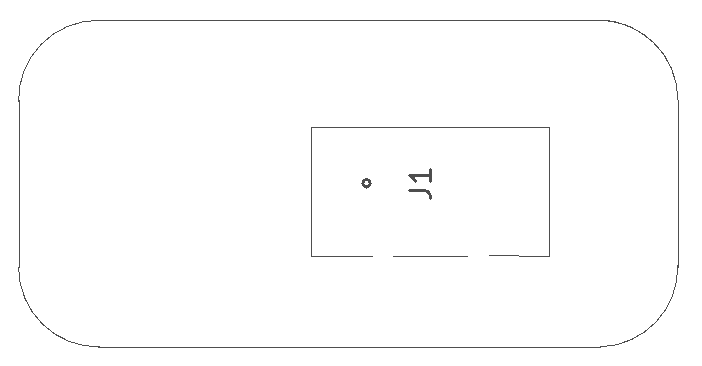
[picture p271: Circuit-Kits/Modules/2x4-Grove-Sensor-Inline/assembly.png]
Assembly Diagram


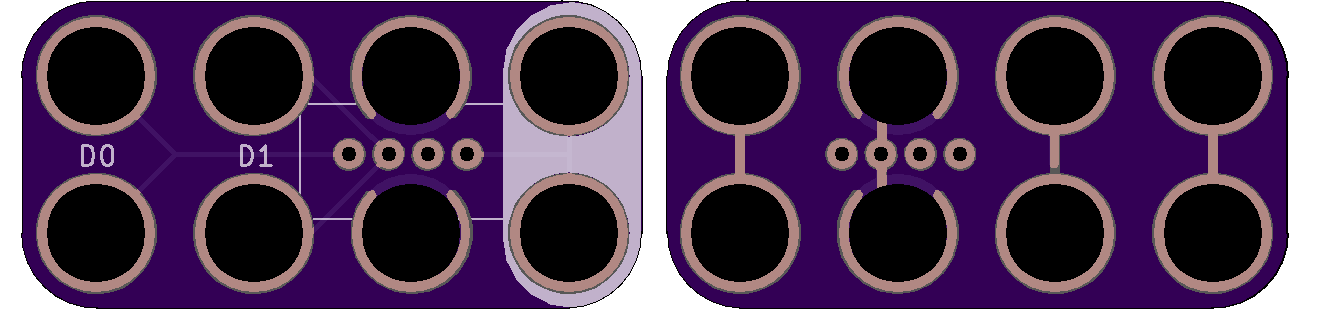
[picture p272: Circuit-Kits/Modules/2x4-Grove-Sensor-Inline/preview.png]
Gerber Preview
