BrownDogGadgets/CrazyCircuits/Circuit-Kits/Modules/3x4-555-Timer-8DIP-Breakout/README.md

<!--- start title --->
# 3x4 555 Timer 8DIP Breakout Module v1.1
A Lego-compatible Crazy Circuits module

- Updated: 7 Oct 2017
- Website: http://browndoggadgets.com/
- Company: Brown Dog Gadgets
- License: CERN Open Hardware License v1.2.

<!--- end title --->
The 555 Timer is an oscillator that's good for all kinds of timer circuits.

<!--- bom start --->
### Bill of Materials

|Ref|Qty|Description|Digikey PN|
|---|---|---|---|
|U1|1|IC OSC 555 TIMER 8-DIP|LM555CNFS-ND|

<!--- bom end --->

### Manufacturing Notes

This board must be v-scored. Do not panelize with support tabs or mousebites.
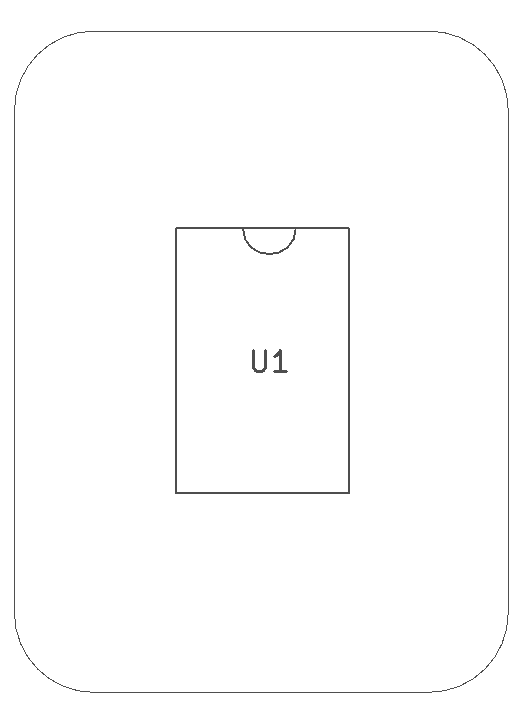
[picture p276: Circuit-Kits/Modules/3x4-555-Timer-8DIP-Breakout/assembly.png]
Assembly Diagram


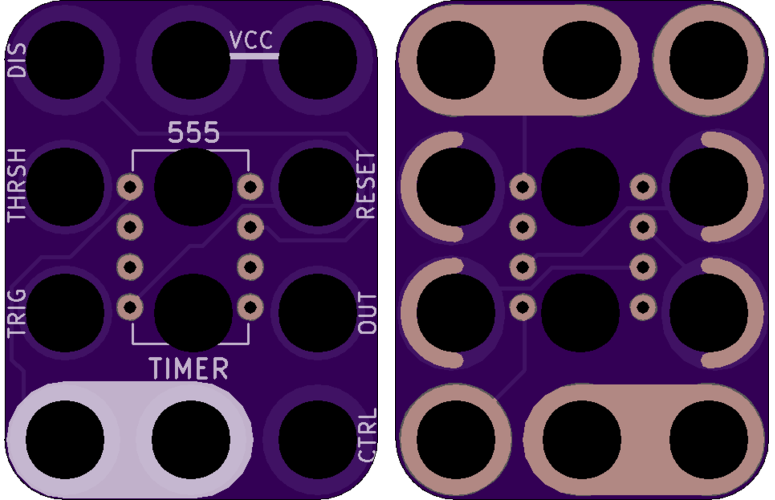
[picture p277: Circuit-Kits/Modules/3x4-555-Timer-8DIP-Breakout/preview.png]
Gerber Preview
