BrownDogGadgets/CrazyCircuits/Circuit-Kits/Modules/3x4-555-Timer-8SOIC-Breakout/README.md

<!--- start title --->
# 3x4 555 Timer 8SOIC Breakout Module v1.1
A Lego-compatible Crazy Circuits module

- Updated: 28 May 2017
- Website: http://browndoggadgets.com/
- Company: Brown Dog Gadgets
- License: CERN Open Hardware License v1.2.
<!--- end title --->

The 555 Timer is an oscillator that's good for all kinds of timer circuits.

<!--- bom start --->
### Bill of Materials

|Ref|Qty|Description|Digikey PN|
|---|---|---|---|
|U1|1|IC OSC 555 TIMER 8-SOIC|LM555CMXFSCT-ND|

<!--- bom end --->

### Manufacturing Notes

This board must be v-scored. Do not panelize with support tabs or mousebites.
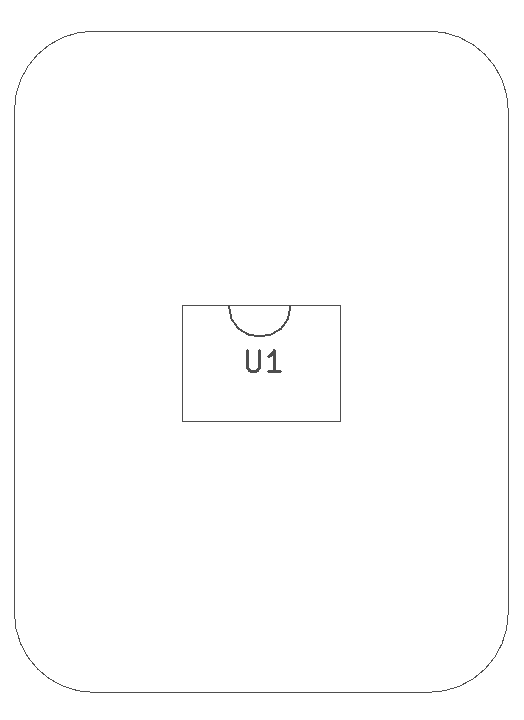
[picture p278: Circuit-Kits/Modules/3x4-555-Timer-8SOIC-Breakout/assembly.png]
Assembly Diagram


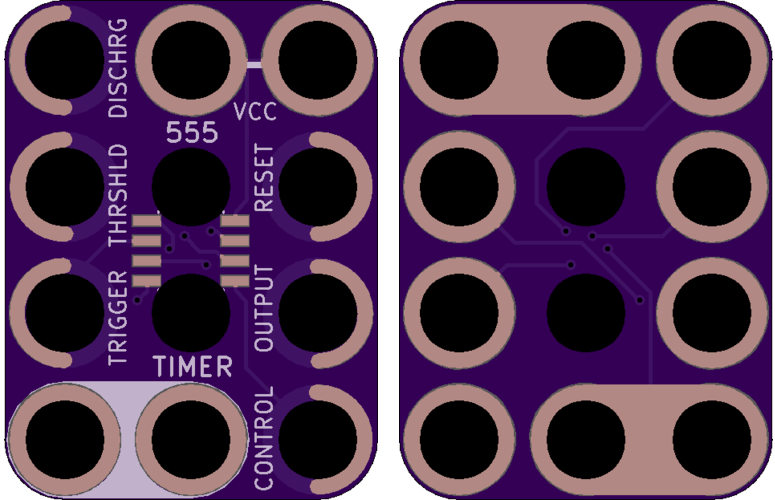
[picture p279: Circuit-Kits/Modules/3x4-555-Timer-8SOIC-Breakout/preview.png]
Gerber Preview
