BrownDogGadgets/CrazyCircuits/Circuit-Kits/Modules/3x4-ATtiny85-8DIP-Breakout/README.md

<!--- start title --->
# 3x4 ATtiny85 8DIP Breakout Module v1.3
A Lego-compatible Crazy Circuits module

- Updated: 7 Oct 2017
- Website: http://browndoggadgets.com/
- Company: Brown Dog Gadgets
- License: CERN Open Hardware License v1.2.

<!--- end title --->

This is a breakout board for an ATiny85. 

<!--- bom start --->
### Bill of Materials

|Ref|Qty|Description|Digikey PN|
|---|---|---|---|
|U1|1|IC MCU 8BIT ATTINY85 8DIP|ATTINY85-20PU-ND|

<!--- bom end --->

### Manufacturing Notes

This board must be v-scored. Do not panelize with support tabs or mousebites.

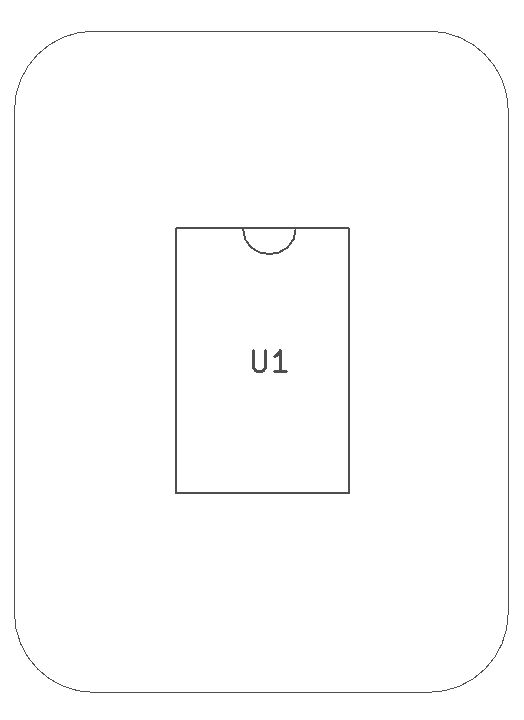
[picture p280: Circuit-Kits/Modules/3x4-ATtiny85-8DIP-Breakout/assembly.png]
Assembly Diagram


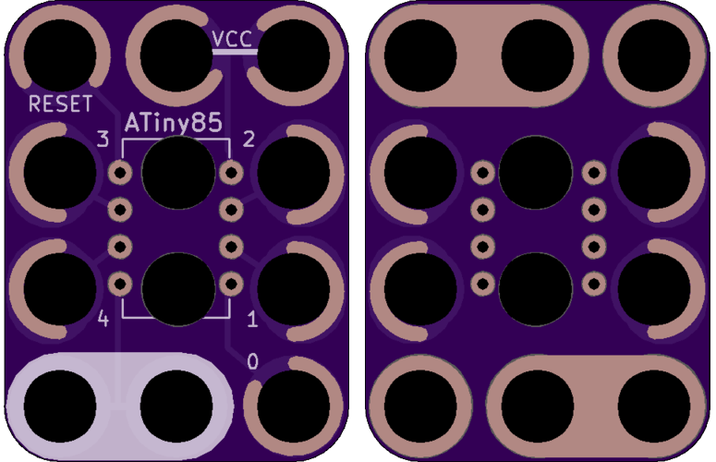
[picture p281: Circuit-Kits/Modules/3x4-ATtiny85-8DIP-Breakout/preview.png]
Gerber Preview
