BrownDogGadgets/CrazyCircuits/Circuit-Kits/Modules/4x7-Teensy-Breakout/README.md

<!--- start title --->
# 4x7 Teensy LC Breakout v1.1
A Lego-compatible Crazy Cicuits module

- Updated: 13 Feb 2017
- Website: http://browndoggadgets.com/
- Company: Brown Dog Gadgets
- License: CERN Open Hardware License v1.2.

<!--- end title --->

This is a breakout board for the Teensy LC development board. 

<!--- bom start --->
### Bill of Materials

|Ref|Qty|Description|Pjrc PN|
|---|---|---|---|
|U11|1|TEENSY LC DEVELOPMENT BOARD|TEENSY LC|

<!--- bom end --->

### Manufacturing Notes

This board must be v-scored. Do not panelize with support tabs or mousebites.
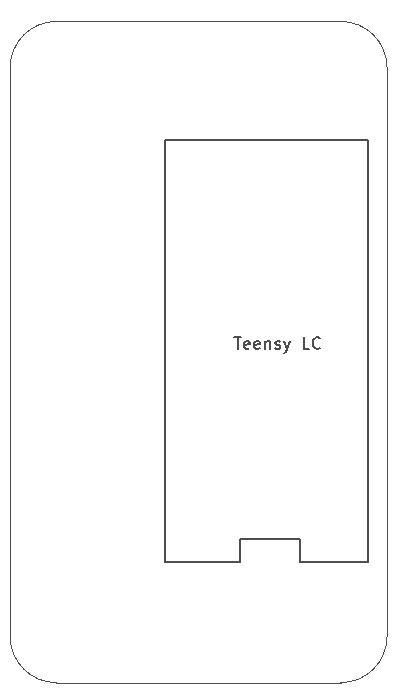
[picture p283: Circuit-Kits/Modules/4x7-Teensy-Breakout/assembly.png]
Assembly Diagram


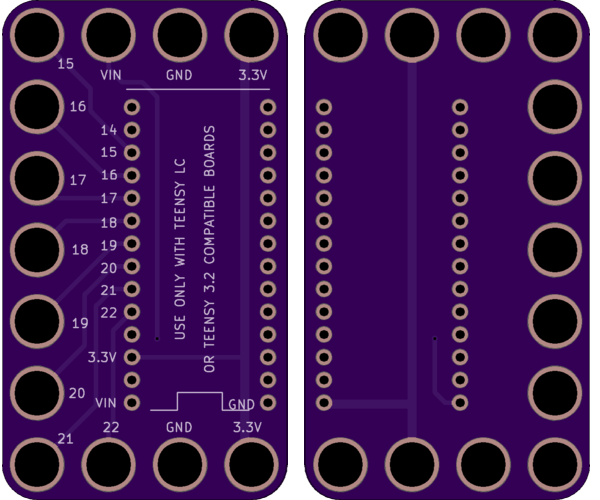
[picture p284: Circuit-Kits/Modules/4x7-Teensy-Breakout/preview.png]
Gerber Preview
