BrownDogGadgets/CrazyCircuits/Circuit-Kits/Modules/5x10-Teensy-LC-Breakout/README.md

<!--- start title --->
# 5x10 Teensy LC Breakout Module v1.4
A Lego-compatible Crazy Circuits module

- Updated: 11 May 2018
- Website: http://browndoggadgets.com/
- Company: Brown Dog Gadgets
- License: CERN Open Hardware License v1.2.

<!--- end title --->
Breakout board for the Teensy LC.

<!--- bom start --->
### Bill of Materials

|Ref|Qty|Description|PJRC PN|
|---|---|---|---|
|U1|1|TEENSY LC DEVELOPMENT BOARD|TEENSY LC|

<!--- bom end --->

### Manufacturing Notes

This board must be v-scored. Do not panelize with support tabs or mousebites.

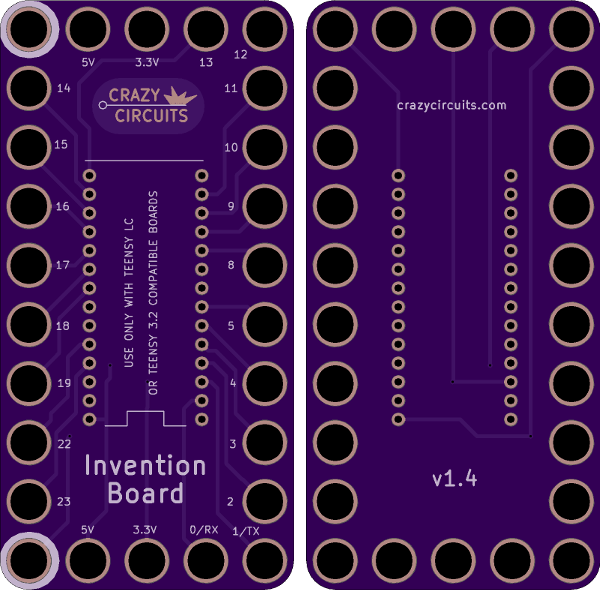
[picture p286: Circuit-Kits/Modules/5x10-Teensy-LC-Breakout/preview.png]
Gerber Preview
