BrownDogGadgets/CrazyCircuits/Circuit-Kits/Modules/6x10-Feather-Bluefruit-LE/README.md

<!--- start title --->
# 6x10 Feather Huzzah ESP8266 Module v1.0
A Lego-compatible Crazy Circuits module

- Updated: 8 Feb 2018

- Website: http://browndoggadgets.com/
- Company: Brown Dog Gadgets
- License: CERN Open Hardware License v1.2.
<!--- end title --->

Breakout board for the Adafruit Feather Bluefruit Low Energy (LE) module so you can add Bluetooth to your projects.

<!--- bom start --->
### Bill of Materials

|Ref|Qty|Description|Digikey PN|
|---|---|---|---|
|U1|1|ADAFRUIT FEATHER BLUEFRUIT LE|1528-2095-ND|

<!--- bom end --->

### Manufacturing Notes

This board must be v-scored. Do not panelize with support tabs or mousebites.

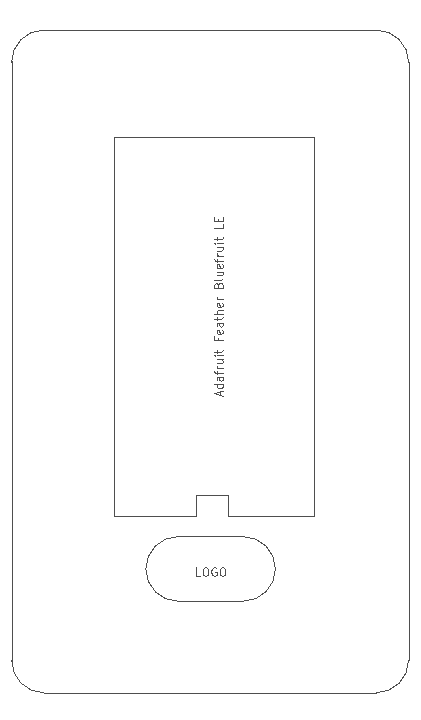
[picture p287: Circuit-Kits/Modules/6x10-Feather-Bluefruit-LE/assembly.png]
Assembly Diagram


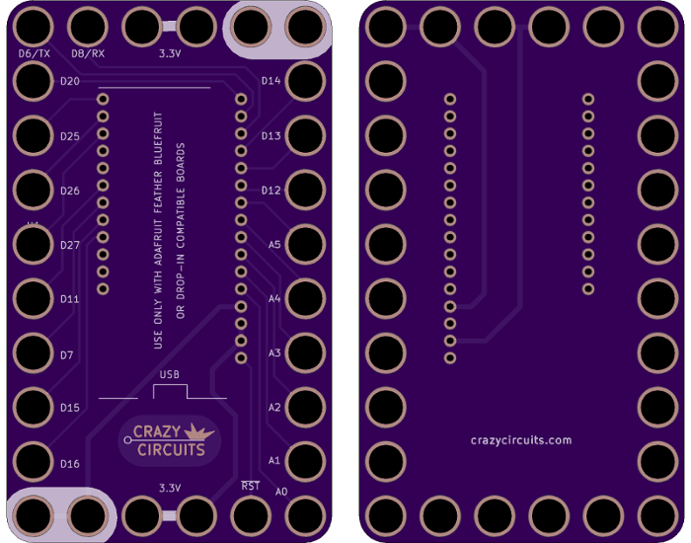
[picture p288: Circuit-Kits/Modules/6x10-Feather-Bluefruit-LE/preview.png]
Gerber Preview


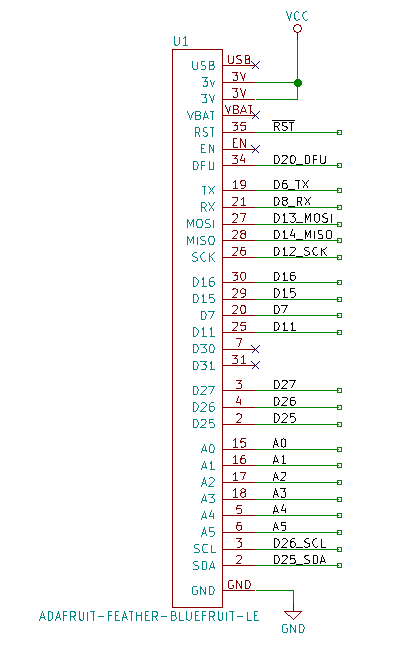
[picture p289: Circuit-Kits/Modules/6x10-Feather-Bluefruit-LE/schematic.png]
Schematic
