BrownDogGadgets/CrazyCircuits/Circuit-Kits/Modules/6x10-Feather-Huzzah-ESP8266/README.md

<!--- start title --->
# 6x10 Feather Huzzah ESP8266 Module v1.0
A Lego-compatible Crazy Circuits module

- Updated: 8 Feb 2018

- Website: http://browndoggadgets.com/
- Company: Brown Dog Gadgets
- License: CERN Open Hardware License v1.2.
<!--- end title --->

Breakout board for the Adafruit Feather Huzzah ESP8266 board, which lets you add Wifi your project.

<!--- bom start --->
### Bill of Materials

|Ref|Qty|Description|Digikey PN|
|---|---|---|---|
|U1|1|ADAFRUIT FEATHER ESP8266 HUZZAH|1528-1530-ND|

<!--- bom end --->

### Manufacturing Notes

This board must be v-scored. Do not panelize with support tabs or mousebites.

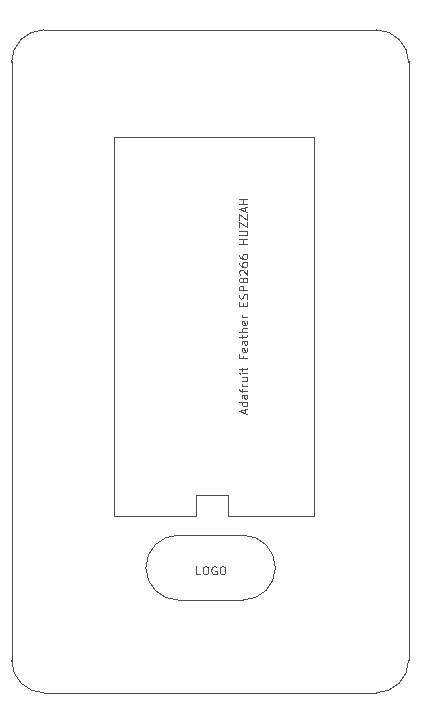
[picture p290: Circuit-Kits/Modules/6x10-Feather-Huzzah-ESP8266/assembly.png]
Assembly Diagram


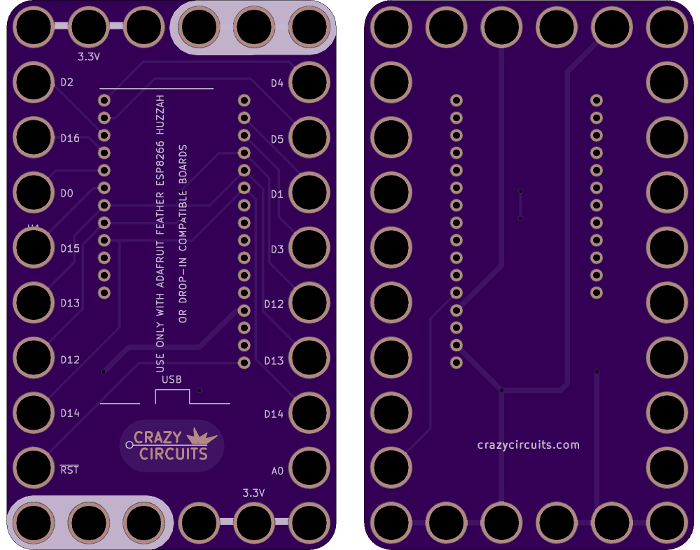
[picture p291: Circuit-Kits/Modules/6x10-Feather-Huzzah-ESP8266/preview.png]
Gerber Preview


Schematic
