BrownDogGadgets/CrazyCircuits/Circuit-Kits/Circuit-Kits/10mmLED-Button-Battery/README.md

<!--- start title --->
# 10mmLED-Button-Battery Circuit Kit v1.3

- Updated: 7 Oct 2017

- Website: http://browndoggadgets.com/
- Company: Brown Dog Gadgets
- License: All rights reserved.

<!--- end title --->

Circuit kit that can be snapped apart into three Lego-compatible modules. Just add a coin cell battery and light the LED by pressing the pushbutton.

<!--- start bom --->

|Ref|Qty|Description|Digikey PN|
|---|---|---|---|
|BT1|1|HOLDER BATT COIN CR2032/20MM|952-1735-1-ND|
|LED1|1|LED GREEN 10MM DIA 2.54MM PITCH TH|754-1898-ND|
|SW1|1|SWITCH TACTILE SPST-NO 0.05A 24V|SW400-ND|

<!--- end bom --->

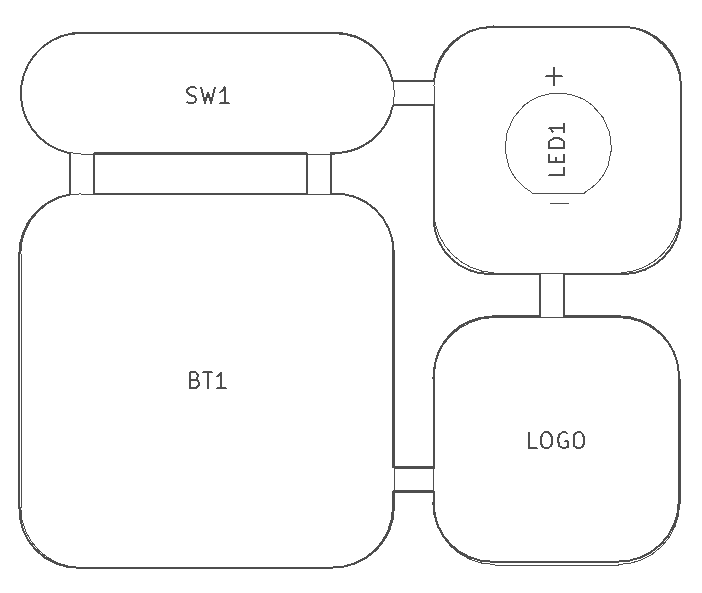
[picture p297: Circuit-Kits/Circuit-Kits/10mmLED-Button-Battery/assembly.png]
Assembly Diagram

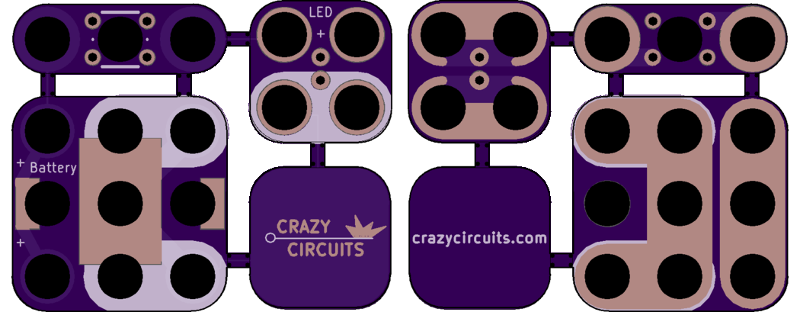
[picture p298: Circuit-Kits/Circuit-Kits/10mmLED-Button-Battery/preview.png]
Gerber Preview
