BrownDogGadgets/CrazyCircuits/Circuit-Kits/Circuit-Kits/LegoLED-Button-Battery/README.md

<!--- start title --->
# LegoLED-Button-Battery Circuit Kit v1.5

- Updated: 7 Oct 2017
- Website: http://browndoggadgets.com/
- Company: Brown Dog Gadgets
- License: All rights reserved.

<!--- end title --->

Circuit kit that can be snapped apart into three Lego-compatible modules. Just add a coin cell battery and light the LED by pressing the pushbutton.

<!--- start bom --->

|Ref|Qty|Description|Digikey PN|
|---|---|---|---|
|BT1|1|HOLDER BATT COIN CR2032/20MM|952-1735-1-ND|
|SW1|1|SWITCH TACTILE SPST-NO 0.05A 24V|SW400-ND|

|Ref|Qty|Description|Lunchbox Electronics PN|
|---|---|---|---|
|LED1|1|LED LEGO NOVELTY COLOR 5MM PITCH|COM-005|

<!--- end bom --->

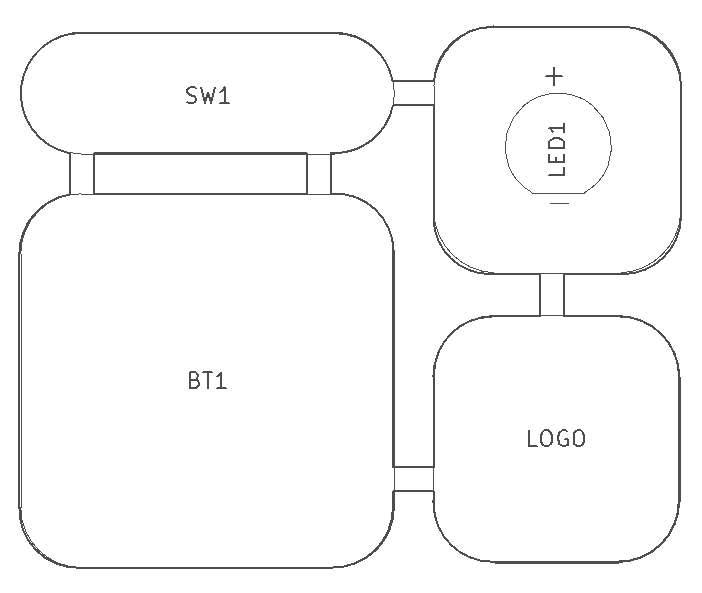
[picture p299: Circuit-Kits/Circuit-Kits/LegoLED-Button-Battery/assembly.png]
Assembly Diagram

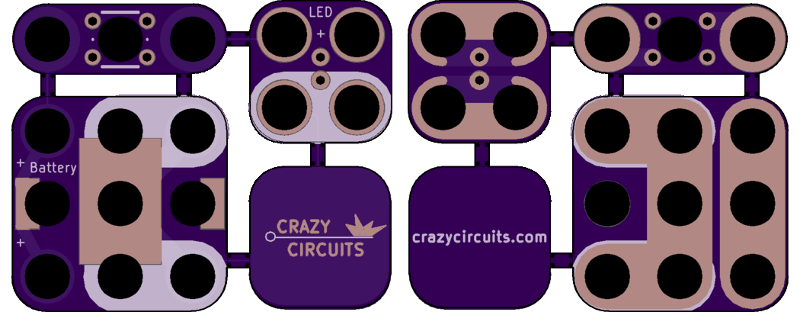
[picture p300: Circuit-Kits/Circuit-Kits/LegoLED-Button-Battery/preview.png]
Gerber Preview
