BrownDogGadgets/CrazyCircuits/Circuit-Kits/Modules/2x2-Power-Connector-2.54mm-Pitch/2x2-Power-Connector-2.54mm-Pitch-v1.0.pdf

Crazy Circuits | Brown Dog Gadgets

# 2x2-Power-Connector-2.54mm-Pitch

This part fits a RED right angle connector. This part is intended to be used with a battery pack and should supply power to other modules.

Bill of Materials

Ref | Qty | Description | MPN
J1 | 1 | Red right angle header 2.54mm pitch | M20-9960245

Manufacturing Notes
This board must be v-scored. Do not panelize with support tabs or mousebites.The PCB Soldermask should be blue and the Silkscreen white. Ensure the back is flat when soldered.
