BrownDogGadgets/CrazyCircuits/Projects/Bobby the Bass/README.md

# Bobby the Bass



The file `001xxx.mp3` can be loaded onto the MP3 Player for our "Bobby the Bass" project. 

Full Guide: https://browndoggadgets.dozuki.com/Guide/DIY+Singing+Fish+-+Bobby+the+Bass/372

---

Brown Dog Gadgets

https://www.browndoggadgets.com/
