BrownDogGadgets/CrazyCircuits/Circuit-Kits/Modules/1x3-Button-Momentary-SMT/schematic.png

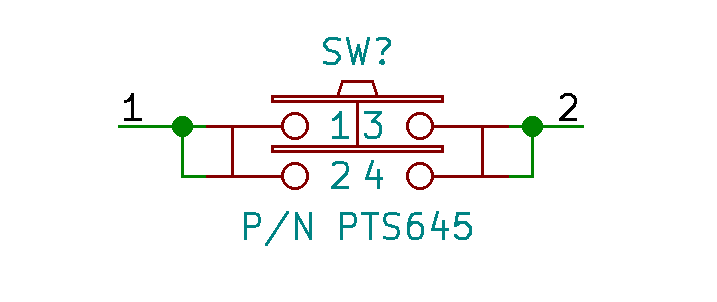
Circuit-Kits/Modules/1x3-Button-Momentary-SMT/schematic.png
