BrownDogGadgets/CrazyCircuits/Circuit-Kits/Modules/2x2-Power-Connector-2.54mm-Pitch/thumb.png

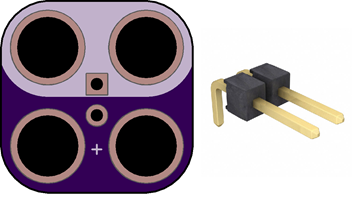
Circuit-Kits/Modules/2x2-Power-Connector-2.54mm-Pitch/thumb.png
