BrownDogGadgets/CrazyCircuits/Circuit-Kits/Modules/2x3-Power-Connector-2.54mm-Pitch/preview.png

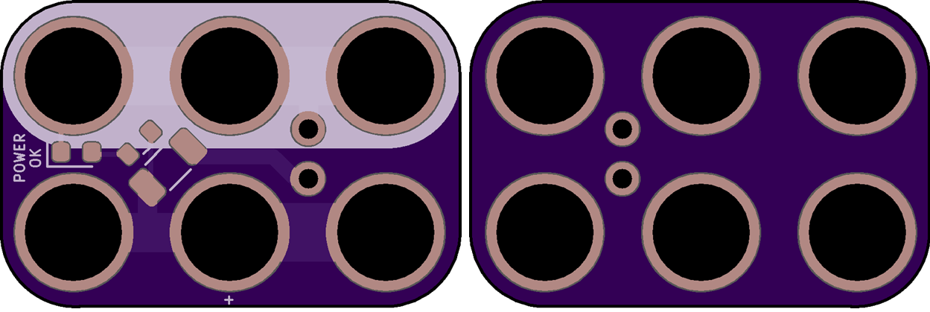
Circuit-Kits/Modules/2x3-Power-Connector-2.54mm-Pitch/preview.png
