BrownDogGadgets/CrazyCircuits/Circuit-Kits/Modules/6x11-Raspi-Pico-Robot-Version/preview.png

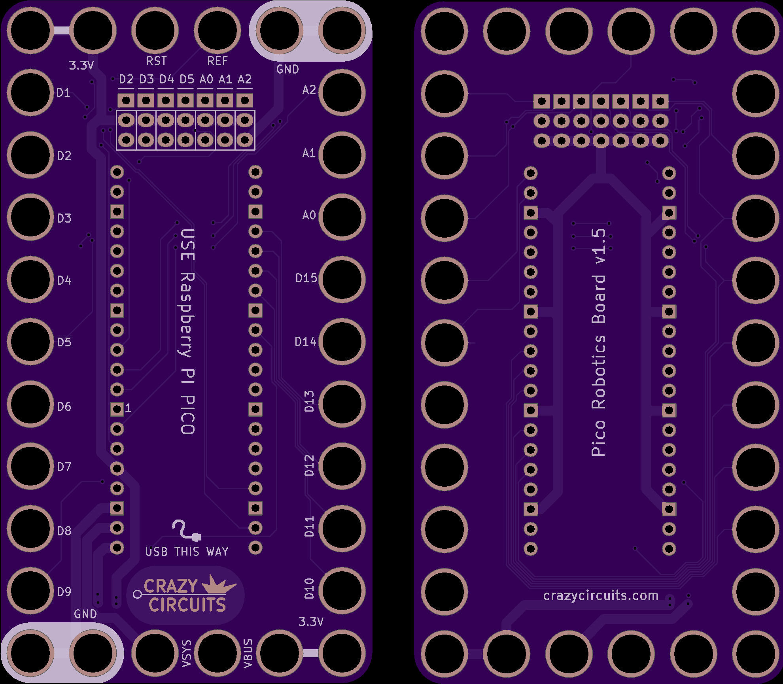
Circuit-Kits/Modules/6x11-Raspi-Pico-Robot-Version/preview.png
