BrownDogGadgets/CrazyCircuits/Development/images/8-blank-template.png

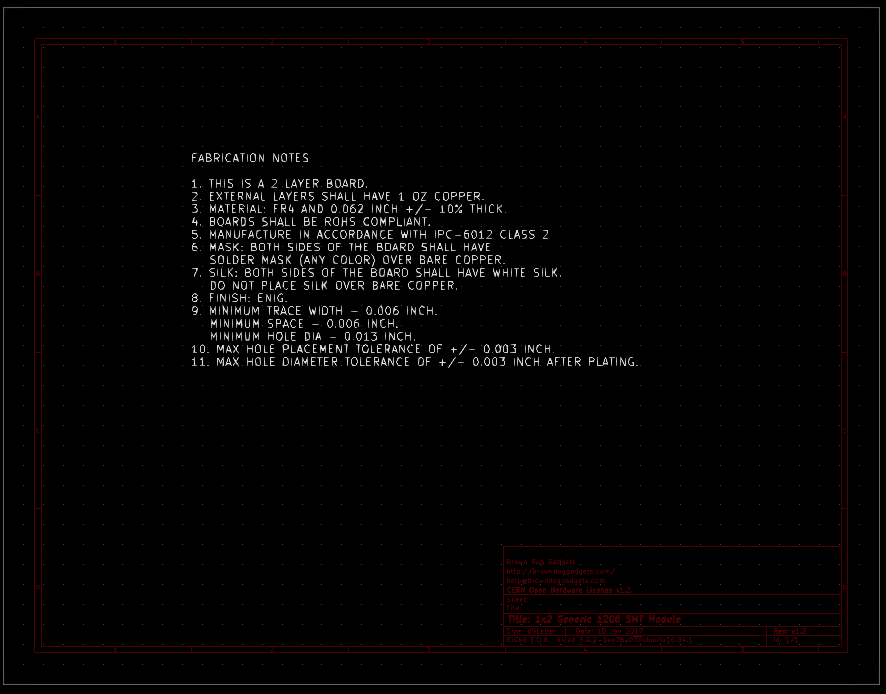
Development/images/8-blank-template.png
