BrownDogGadgets/CrazyCircuits/Projects/Bubble Machine/Images/Bubble-Machine-9378.jpg

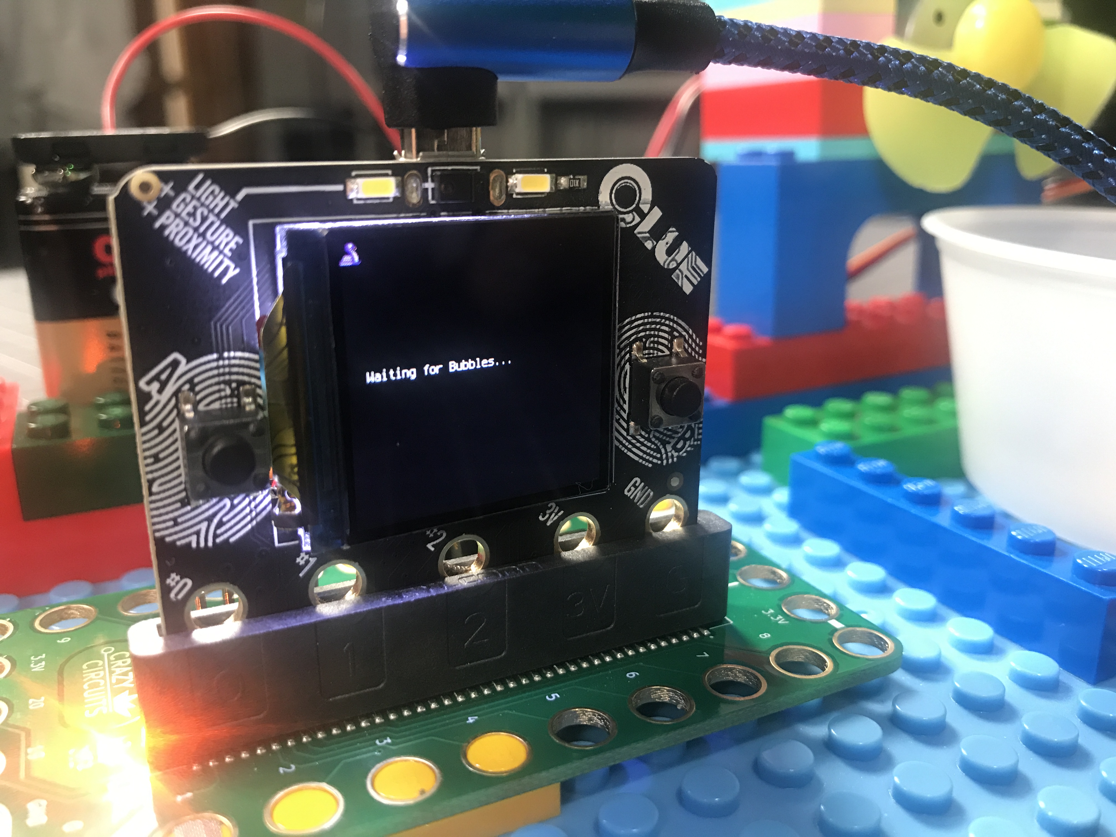
Projects/Bubble Machine/Images/Bubble-Machine-9378.jpg
