BrownDogGadgets/CrazyCircuits/Projects/Bubble Machine/Images/Bubble-Machine-9381.jpg

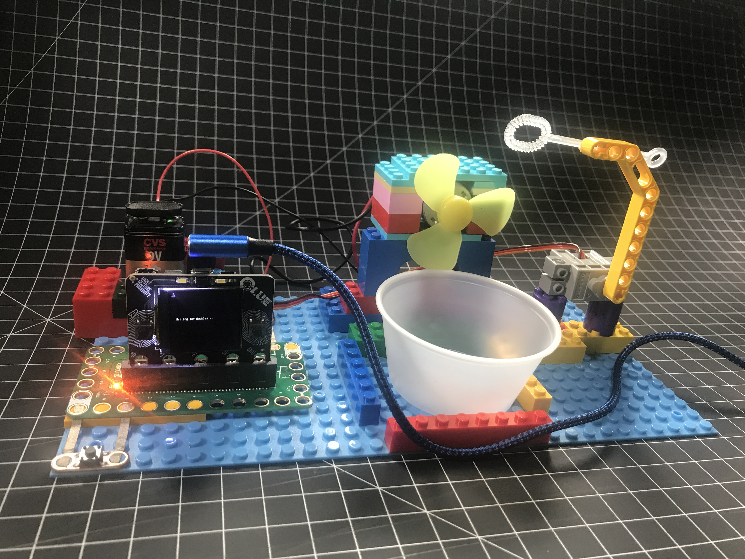
Projects/Bubble Machine/Images/Bubble-Machine-9381.jpg
