BrownDogGadgets/CrazyCircuits/Projects/Bubble Machine/Images/clue-circuitpython.png

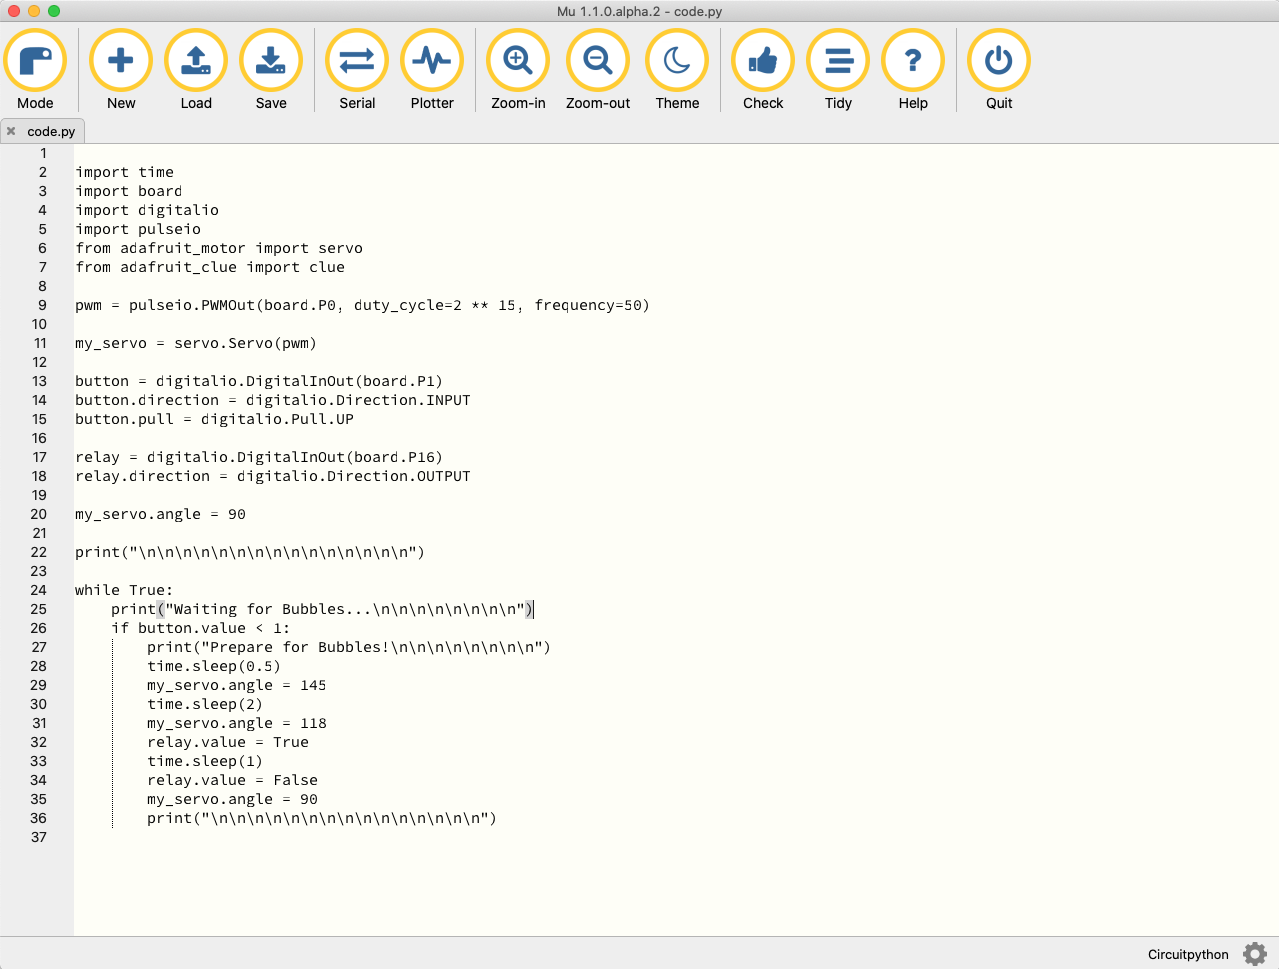
Projects/Bubble Machine/Images/clue-circuitpython.png
