BrownDogGadgets/CrazyCircuits/Projects/NES Controller/LEGO Controller Wood v13 RENDER.png

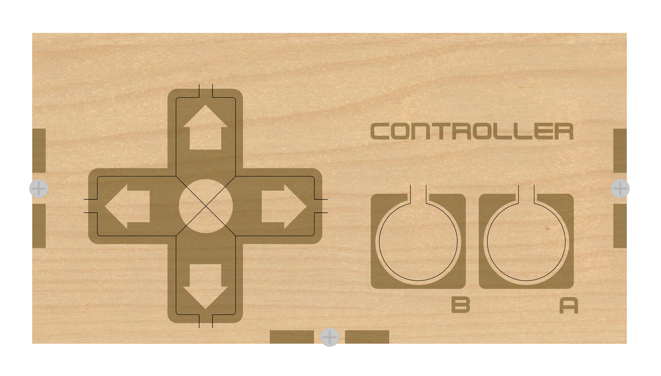
Projects/NES Controller/LEGO Controller Wood v13 RENDER.png
