BrownDogGadgets/CrazyCircuits/Circuit-Kits/Modules/5x10-Teensy-LC-Breakout/bom/5x10-Teensy-LC-Breakout-v1.4-assy-readme.md

Individual Placements per board: 1

Number of Parts: 1

Board size is 1.57 x 3.14 inches (39.80 x 79.80 mm)
