BrownDogGadgets/CrazyCircuits/Circuit-Kits/Modules/5x10-Teensy-LC-Breakout/bom/5x10-Teensy-LC-Breakout-v1.4-bom-readme.md

|Ref|Qty|Description|PJRC PN|
|---|---|---|---|
|U1|1|TEENSY LC DEVELOPMENT BOARD|TEENSY LC|
