BrownDogGadgets/CrazyCircuits/Circuit-Kits/Modules/2x2-Tilt-Switch-SW-520D-TH/bom/2x2-Tilt-Switch-SW-520D-TH-v1.1-bom-readme.md

|Ref|Qty|Description|Alibaba PN|
|---|---|---|---|
|SW1|1|TILT SENSOR ROLLING BALL SW-520D|SW-520D|
