BrownDogGadgets/CrazyCircuits/Circuit-Kits/Modules/2x2-LED-WHITE-SMT-LIMITED/bom/2x2-LED-WHITE-SMT-LIMITED-v1.0-assy-readme.md

Individual Placements per board: 2

Number of Parts: 2

Board size is 0.61 x 0.61 inches (15.60 x 15.60 mm)
