BrownDogGadgets/CrazyCircuits/Circuit-Kits/Circuit-Kits/SMTLimitLED-SMTButton-Battery/bom/SMTLimitLED-SMTButton-Battery-v1.0-assy-readme.md

Individual Placements per board: 4

Number of Parts: 4

Board size is 1.65 x 1.64 inches (41.79 x 41.70 mm)
