BrownDogGadgets/CrazyCircuits/Circuit-Kits/Modules/2x3-LED-RGB-SMT-Round-Flat-Top/bom/2x3-LED-RGB-SMT-Round-Flat-Top-v1.0-bom-readme.md

|Ref|Qty|Description|Digikey PN|
|---|---|---|---|
|LED1|1|LED RGB CLEAR 1411 SMD|732-4998-2-ND|
