BrownDogGadgets/CrazyCircuits/Circuit-Kits/Modules/2x3-LED-RGB-A-SMT/bom/2x3-LED-RGB-A-SMT-v1.1-assy-readme.md

Individual Placements per board: 3

Number of Parts: 4

Board size is 0.93 x 0.61 inches (23.60 x 15.60 mm)
