BrownDogGadgets/CrazyCircuits/Circuit-Kits/Modules/3x3-CR2032-Coin-Cell/bom/3x3-CR2032-Coin-Cell-v1.2-assy-readme.md

Individual Placements per board: 1

Number of Parts: 1

Board size is 0.93 x 0.93 inches (23.60 x 23.60 mm)
