BrownDogGadgets/CrazyCircuits/Circuit-Kits/Modules/1x2-LED-1206-SMT/bom/1x2-LED-1206-SMT-v1.2-assy-readme.md

Individual Placements per board: 1

Number of Parts: 1

Board size is 0.32 x 0.31 inches (8.20 x 7.80 mm)
