BrownDogGadgets/CrazyCircuits/Circuit-Kits/Modules/2x4-Grove-Sensor-Inline/bom/2x4-Grove-Sensor-Inline-v1.0-assy-readme.md

Individual Placements per board: 1

Number of Parts: 1

Board size is 1.24 x 0.61 inches (31.50 x 15.60 mm)
