BrownDogGadgets/CrazyCircuits/Circuit-Kits/Modules/2x2-12mm-Square-SMT-Pushbutton/bom/2x2-12mm-Square-SMT-Pushbutton-v1.1-assy-readme.md

Individual Placements per board: 1

Number of Parts: 1

Board size is 0.61 x 0.61 inches (15.50 x 15.60 mm)
