BrownDogGadgets/CrazyCircuits/Circuit-Kits/Modules/1x3-Button-Momentary-SMT/bom/1x3-Button-Momentary-SMT-v1.1-assy-readme.md

Individual Placements per board: 1

Number of Parts: 1

Board size is 0.92 x 0.30 inches (23.49 x 7.60 mm)
