BrownDogGadgets/CrazyCircuits/Circuit-Kits/Modules/1x3-Button-Momentary/bom/1x3-Button-Momentary-v1.2-assy-readme.md

Individual Placements per board: 1

Number of Parts: 1

Board size is 0.63 x 0.30 inches (16.00 x 7.60 mm)
