BrownDogGadgets/CrazyCircuits/Circuit-Kits/Modules/3x4-555-Timer-8SOIC-Breakout/bom/3x4-555-Timer-8SOIC-Breakout-v1.1-bom-readme.md

|Ref|Qty|Description|Digikey PN|
|---|---|---|---|
|U1|1|IC OSC 555 TIMER 8-SOIC|LM555CMXFSCT-ND|
