BrownDogGadgets/CrazyCircuits/Circuit-Kits/Modules/3x4-ATtiny85-8DIP-Breakout/bom/3x4-ATtiny85-8DIP-Breakout-v1.3-assy-readme.md

Individual Placements per board: 1

Number of Parts: 1

Board size is 0.93 x 1.24 inches (23.60 x 31.60 mm)
