BrownDogGadgets/CrazyCircuits/Circuit-Kits/Modules/4x10-Teensy-LC-Breakout/bom/4x10-Teensy-LC-Breakout-v1.1-bom-readme.md

|Ref|Qty|Description|Pjrc PN|
|---|---|---|---|
|U1|1|TEENSY LC DEVELOPMENT BOARD|TEENSY LC|
