BrownDogGadgets/CrazyCircuits/Circuit-Kits/Modules/4x7-Teensy-Breakout/bom/4x7-Teensy-Breakout-v1.1-bom-readme.md

|Ref|Qty|Description|Pjrc PN|
|---|---|---|---|
|U11|1|TEENSY LC DEVELOPMENT BOARD|TEENSY LC|
