BrownDogGadgets/CrazyCircuits/Circuit-Kits/Modules/5x10-Arduino-Nano-Breakout/bom/5x10-Arduino-Nano-Breakout-v1.0-bom-readme.md

|Ref|Qty|Description|Digikey PN|
|---|---|---|---|
|J1|1|ARDUINO NANO DEVELOPMENT BOARD|1050-1001-ND|
