BrownDogGadgets/CrazyCircuits/Circuit-Kits/Modules/1x2-LED-1206-SMT/bom/1x2-LED-1206-SMT-v1.2-bom-readme.md

|Ref|Qty|Description|Digikey PN|
|---|---|---|---|
|LED1|1|LED GREEN CLEAR 1206 SMD|160-1456-1-ND|
