BrownDogGadgets/CrazyCircuits/Circuit-Kits/Modules/3x3-CR2032-Coin-Cell/bom/3x3-CR2032-Coin-Cell-v1.4-bom-readme.md

|Ref|Qty|Description|Digikey PN|
|---|---|---|---|
|BT1|1|HOLDER BATT COIN CR2032/20MM|BK-912-ND|
