BrownDogGadgets/CrazyCircuits/Circuit-Kits/Modules/3x4-555-Timer-8DIP-Breakout/bom/3x4-555-Timer-8DIP-Breakout-v1.1-bom-readme.md

|Ref|Qty|Description|Digikey PN|
|---|---|---|---|
|U1|1|IC OSC 555 TIMER 8-DIP|LM555CNFS-ND|
