BrownDogGadgets/CrazyCircuits/Circuit-Kits/Modules/2x3-Power-Connector-2.54mm-Pitch/bom/2x3-LED-RGB-TH-4PIN-v1.0-bom-readme.md

|Ref|Qty|Description|Digikey PN|
|---|---|---|---|
|LED1|1|DIFFUSED LED - RGB 10MM|1568-1215-ND|
