BrownDogGadgets/CrazyCircuits/Circuit-Kits/Modules/2x3-Screw-Terminal-3.5mm-Pitch/bom/2x3-Screw-Terminal-3.5mm-Pitch-v1.2-bom-readme.md

|Ref|Qty|Description|Digikey PN|
|---|---|---|---|
|J1|1|SCREW TERMINAL 3.5MM PITCH 1x2|ED2740-ND|
