BrownDogGadgets/CrazyCircuits/Circuit-Kits/Modules/3x4-ATtiny85-8SOIC-Breakout/bom/3x4-ATtiny85-8SOIC-Breakout-v1.3-bom-readme.md

|Ref|Qty|Description|Digikey PN|
|---|---|---|---|
|U1|1|IC MCU 8BIT ATTINY85 8SOIC|ATTINY85-20SU-ND|
