BrownDogGadgets/CrazyCircuits/Circuit-Kits/Modules/2x3-Push-Terminal-3mm-Pitch-SMT/bom/2x3-Push-Terminal-3mm-Pitch-SMT-v1.1-bom-readme.md

|Ref|Qty|Description|Digikey PN|
|---|---|---|---|
|J1|1|CONN MINI LITE-TRAP RCPT 2POS|WM11924CT-ND|
