BrownDogGadgets/CrazyCircuits/Circuit-Kits/Modules/2x3-Mini-Potentiometer-3361P-SMT/bom/2x3-Mini-Potentiometer-3361P-SMT-v1.1-bom-readme.md

|Ref|Qty|Description|Digikey PN|
|---|---|---|---|
|R1|1|TRIMMER 10K OHM 0.5W SMD|3361P-103GLFCT-ND|
