BrownDogGadgets/CrazyCircuits/Circuit-Kits/Modules/2x2-CdS-Photocell-TH/bom/2x2-CdS-Photocell-TH-v1.2-bom-readme.md

|Ref|Qty|Description|Digikey PN|
|---|---|---|---|
|LDR1|1|PHOTOCELL 16-33KOHM|PDV-P8103-ND|
