BrownDogGadgets/CrazyCircuits/Circuit-Kits/Modules/2x2-USB-Power-Connector/bom/2x2-USB-Power-Connector-v1.0-bom-readme.md

|Ref|Qty|Description|Digikey PN|
|---|---|---|---|
|J1|1|USB MICRO-B RECEPTACLE 5PIN SMT R/A STUDS|609-4616-1-ND|
