BrownDogGadgets/CrazyCircuits/Circuit-Kits/Modules/2x3-Mini-Potentiometer-3386P-TH/bom/2x3-Mini-Potentiometer-3386P-TH-v1.2-bom-readme.md

|Ref|Qty|Description|Digikey PN|
|---|---|---|---|
|R1|1|TRIMMER 10K OHM 0.5W|3386P-103TLF-ND|
