BrownDogGadgets/CrazyCircuits/Circuit-Kits/Modules/2x3-Speaker-TH-5mm-Pitch/bom/2x3-Speaker-TH-5mm-Pitch-v1.1-bom-readme.md

|Ref|Qty|Description|Digikey PN|
|---|---|---|---|
|SPK1|1|AUDIO SPEAKER PIEZO TH PS1240|445-2525-1-ND|
