BrownDogGadgets/CrazyCircuits/Circuit-Kits/Modules/3x4-ATtiny85-8DIP-Breakout/bom/3x4-ATtiny85-8DIP-Breakout-v1.3-bom-readme.md

|Ref|Qty|Description|Digikey PN|
|---|---|---|---|
|U1|1|IC MCU 8BIT ATTINY85 8DIP|ATTINY85-20PU-ND|
