BrownDogGadgets/CrazyCircuits/Circuit-Kits/Modules/5x11-Arduino-Nano-Robot-Version/bom/5x11-Arduino-Nano-Robot-Version-v1.5-assy-readme.md

Individual Placements per board: 3

Number of Parts: 7

Board size is 1.57 x 3.46 inches (39.80 x 87.80 mm)
