BrownDogGadgets/CrazyCircuits/Circuit-Kits/Modules/2x3-Vibe-Motor-TH/bom/2x3-Vibe-Motor-TH-v1.0-bom-readme.md

|Ref|Qty|Description|Precision microdrives PN|
|---|---|---|---|
|M1|1|MOTOR VIBE PCB 6MM - 10MM TYPE|306-114|
