BrownDogGadgets/CrazyCircuits/User Guides/Printable Test Paper/readme.md

# Printable Paper Templates

Print these off so you can draw out your circuits on paper.

Designed to work with 8.5 x 11 sheets printed in B&W.
