BrownDogGadgets/CrazyCircuits/User Guides/Part Graphics/Red Jumbo LED.pdf

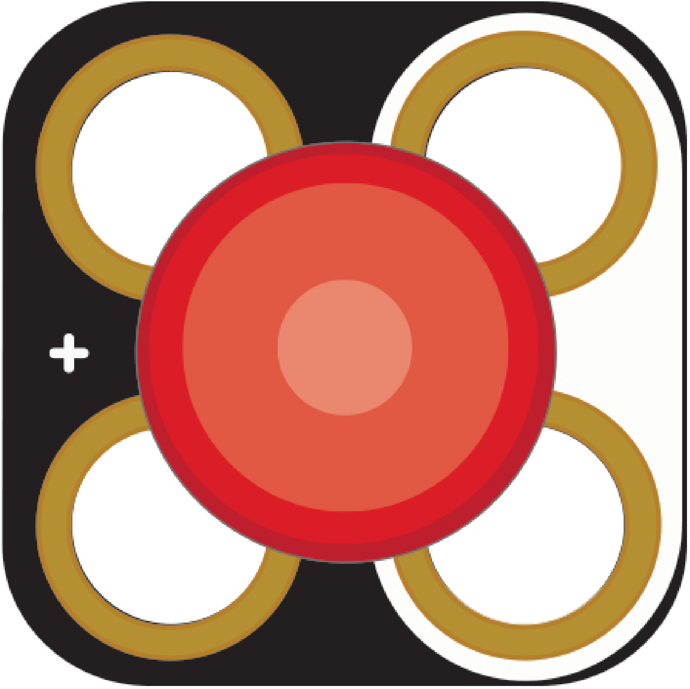
[picture p362: page 1]
