BrownDogGadgets/CrazyCircuits/User Guides/Part Graphics/White Brick LED.pdf

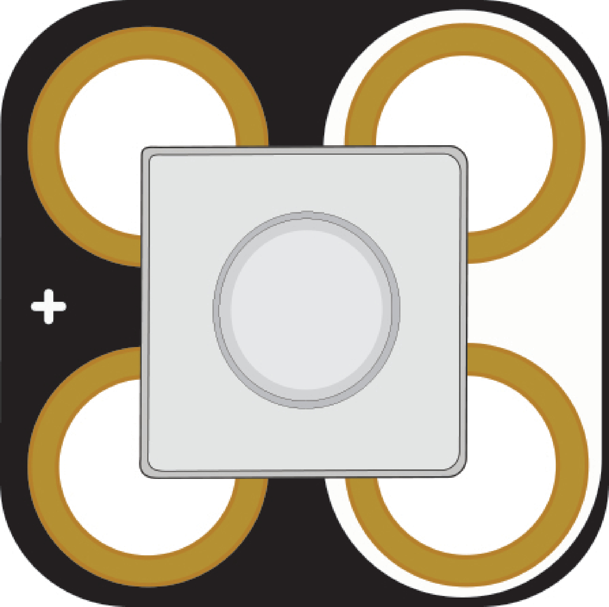
[picture p363: page 1]
