BrownDogGadgets/CrazyCircuits/User Guides/Part Graphics/White Jumbo LED.pdf

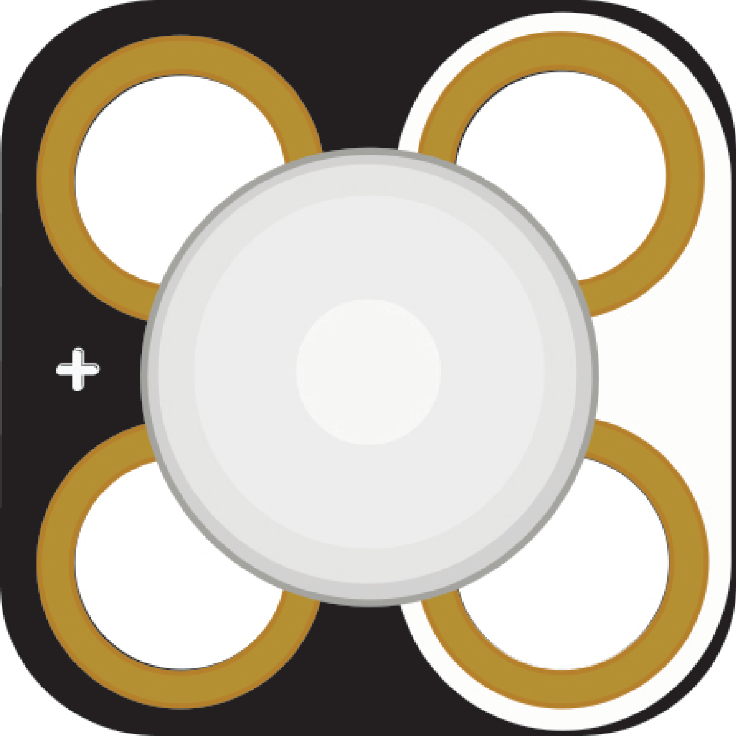
[picture p364: page 1]
