BrownDogGadgets/CrazyCircuits/User Guides/Part Graphics/Yellow Brick LED.pdf

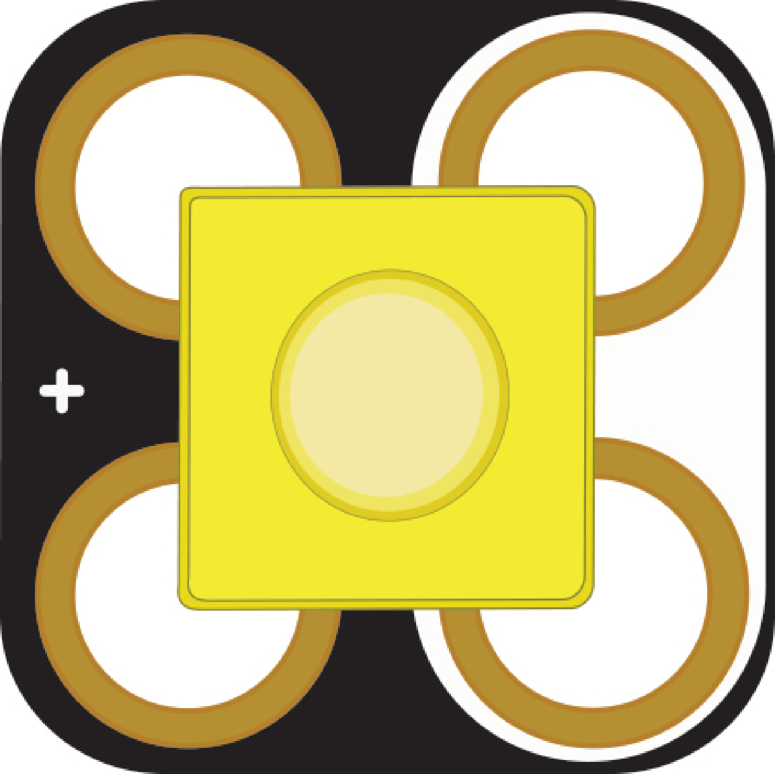
[picture p365: page 1]
