BrownDogGadgets/CrazyCircuits/User Guides/Part Graphics/Yellow Jumbo LED.pdf

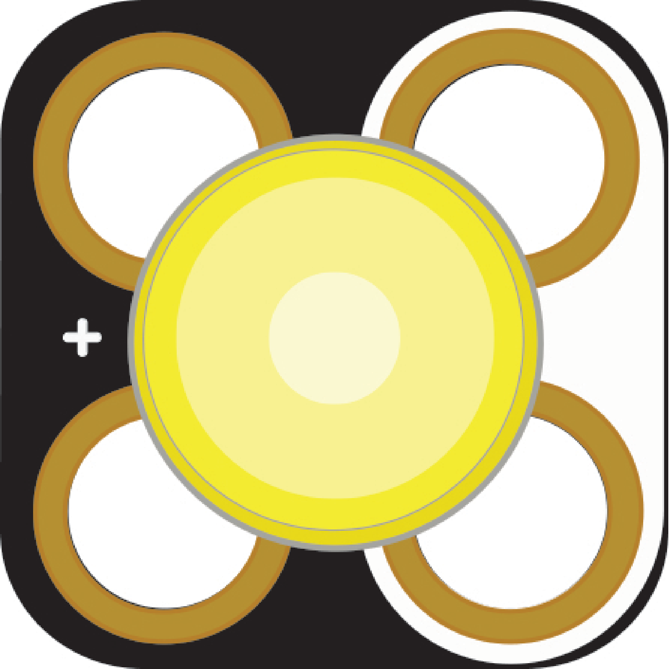
[picture p366: page 1]
