BrownDogGadgets/CrazyCircuits/User Guides/Part Graphics/2AAA Battery Holder.pdf

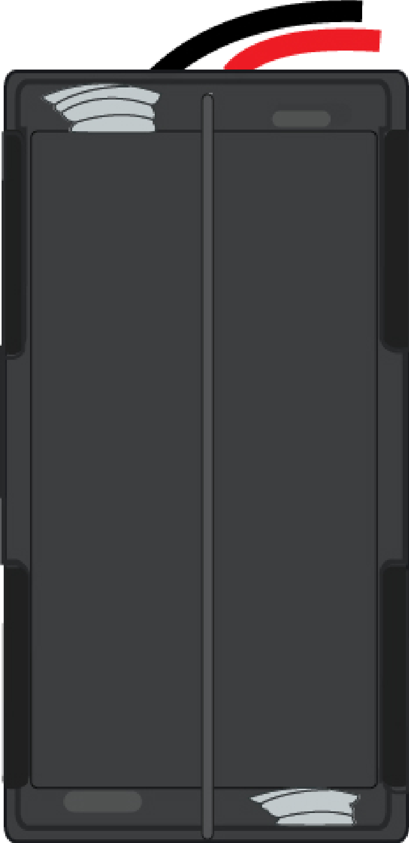
[picture p367: page 1]
