BrownDogGadgets/CrazyCircuits/User Guides/Part Graphics/Blink Fade.pdf

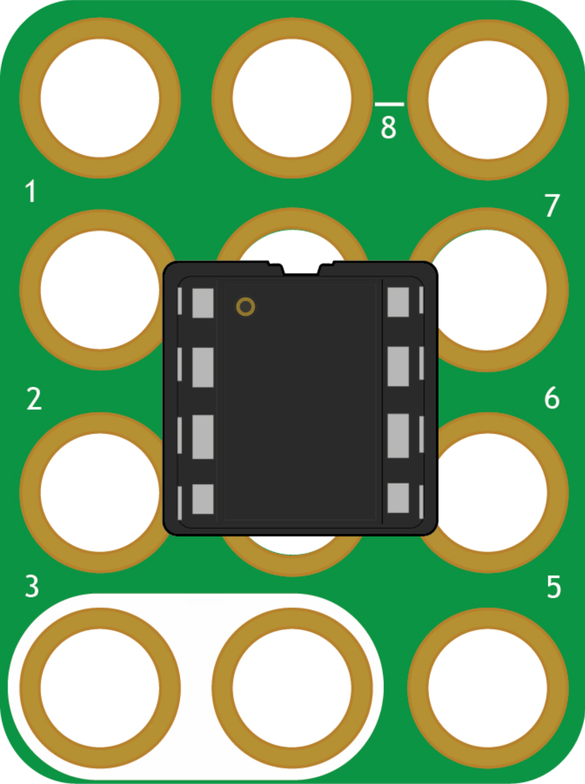
[picture p368: page 1]
