BrownDogGadgets/CrazyCircuits/User Guides/Part Graphics/Coin Cell Battery Holder.pdf

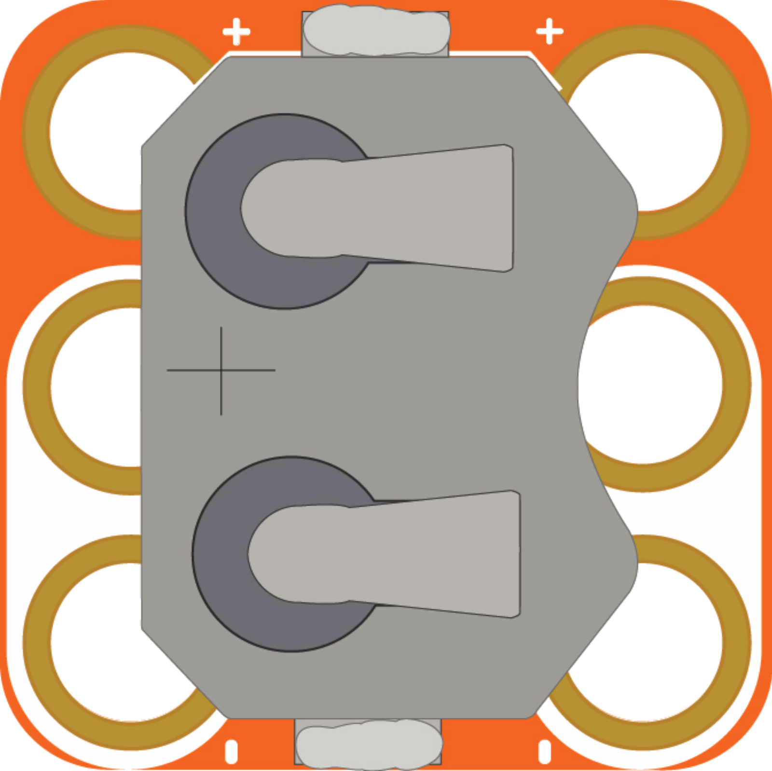
[picture p369: page 1]
