BrownDogGadgets/CrazyCircuits/User Guides/Part Graphics/Continuous Rotation Servo.pdf

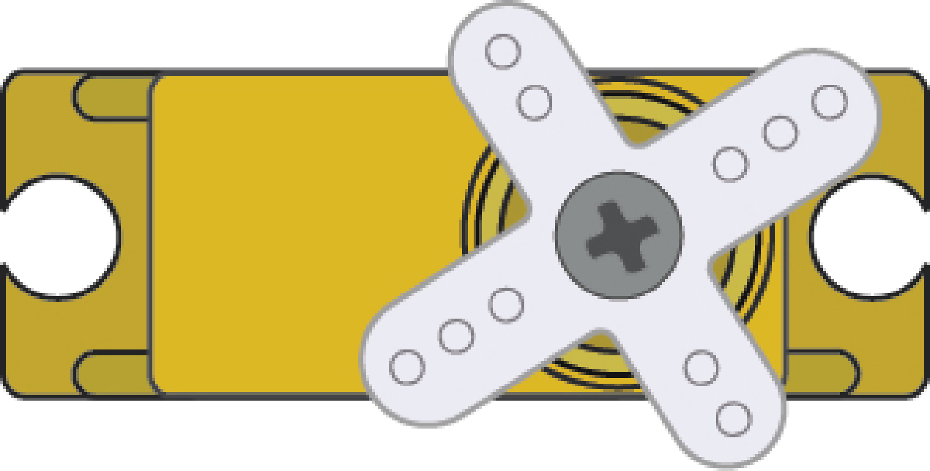
[picture p370: page 1]
