BrownDogGadgets/CrazyCircuits/User Guides/Part Graphics/Jumbo Pushbutton.pdf

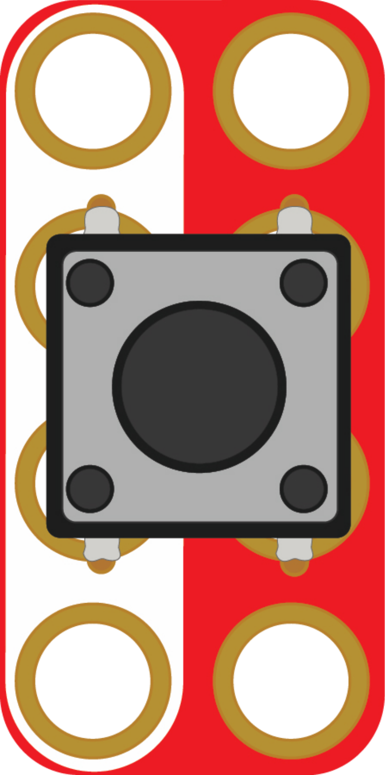
[picture p371: page 1]
