BrownDogGadgets/CrazyCircuits/User Guides/Part Graphics/LED RGB.pdf

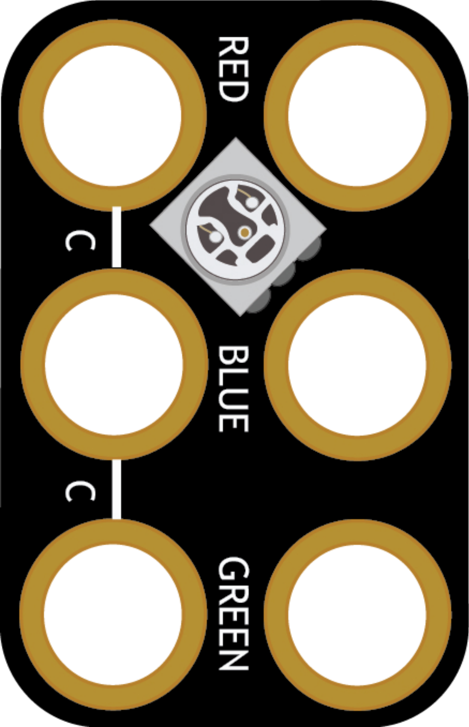
[picture p372: page 1]
