BrownDogGadgets/CrazyCircuits/User Guides/Part Graphics/Male Header.pdf

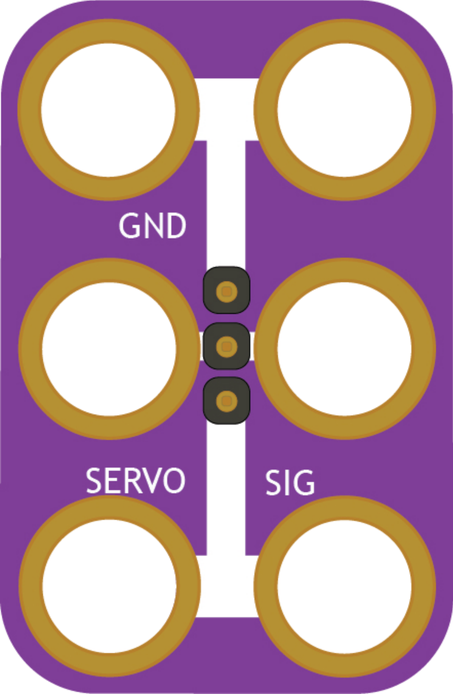
[picture p373: page 1]
