BrownDogGadgets/CrazyCircuits/User Guides/Part Graphics/MINI LED.pdf

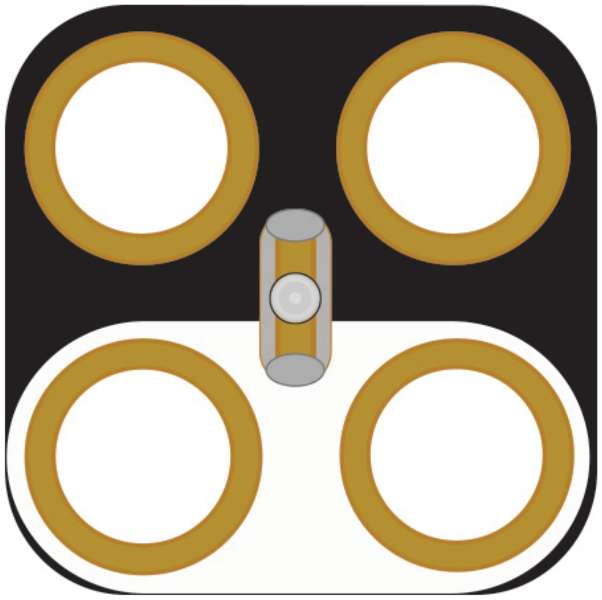
[picture p374: page 1]
