BrownDogGadgets/CrazyCircuits/User Guides/Part Graphics/Mini Potentiometer.pdf

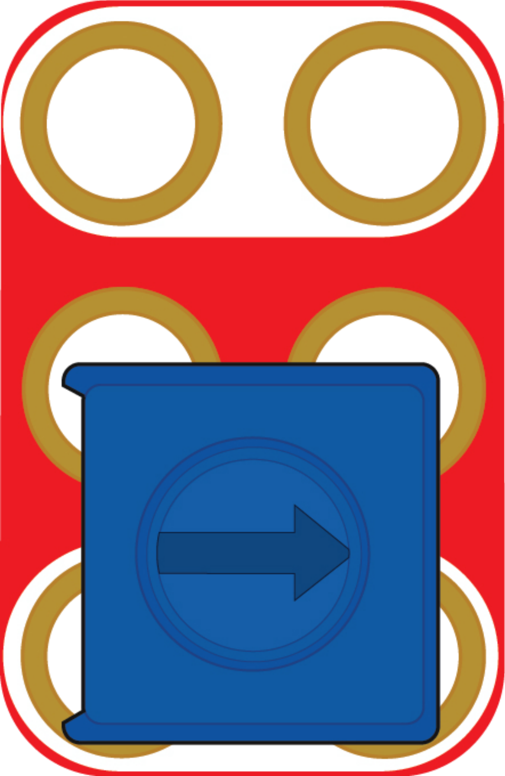
[picture p375: page 1]
