BrownDogGadgets/CrazyCircuits/User Guides/Part Graphics/Momentary  Pushbutton.pdf

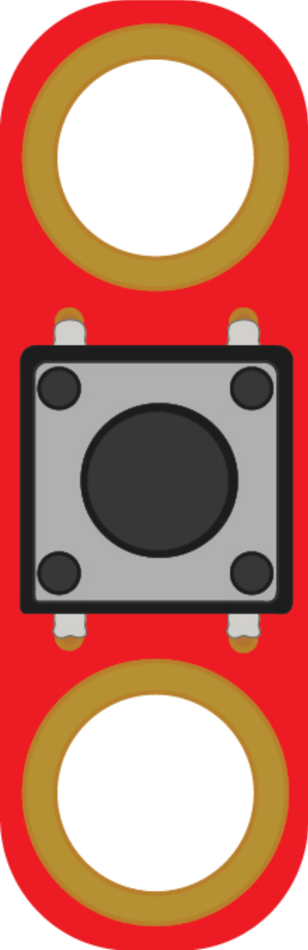
[picture p376: page 1]
