BrownDogGadgets/CrazyCircuits/User Guides/Part Graphics/Robotics Board.pdf

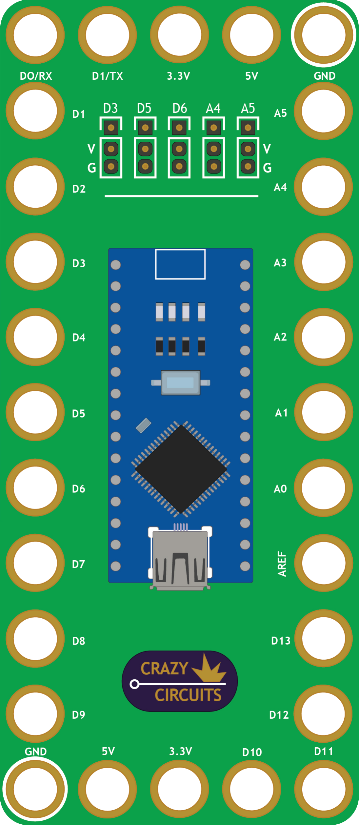
[picture p377: page 1]
