BrownDogGadgets/CrazyCircuits/User Guides/Part Graphics/screw terminal.pdf

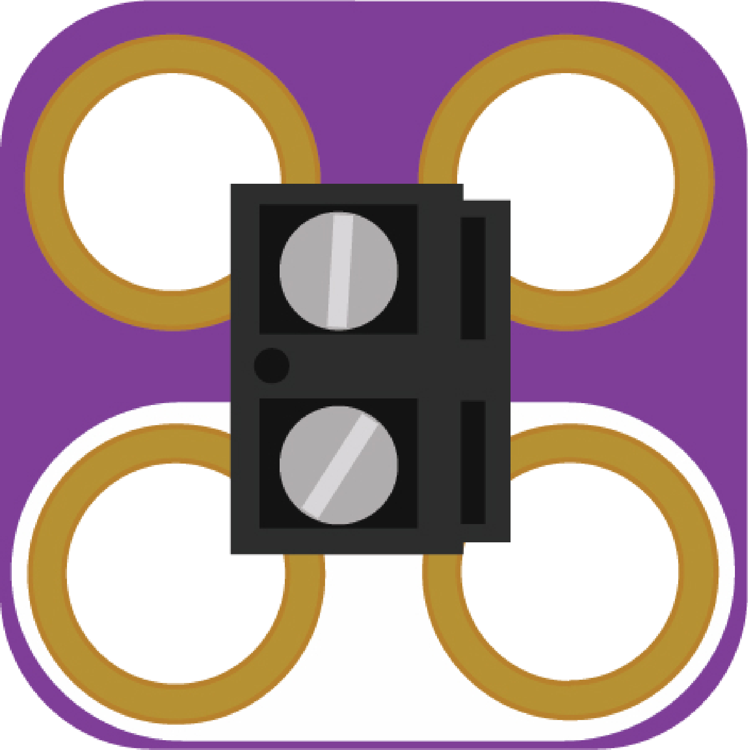
[picture p378: page 1]
