BrownDogGadgets/CrazyCircuits/User Guides/Part Graphics/Servo.pdf

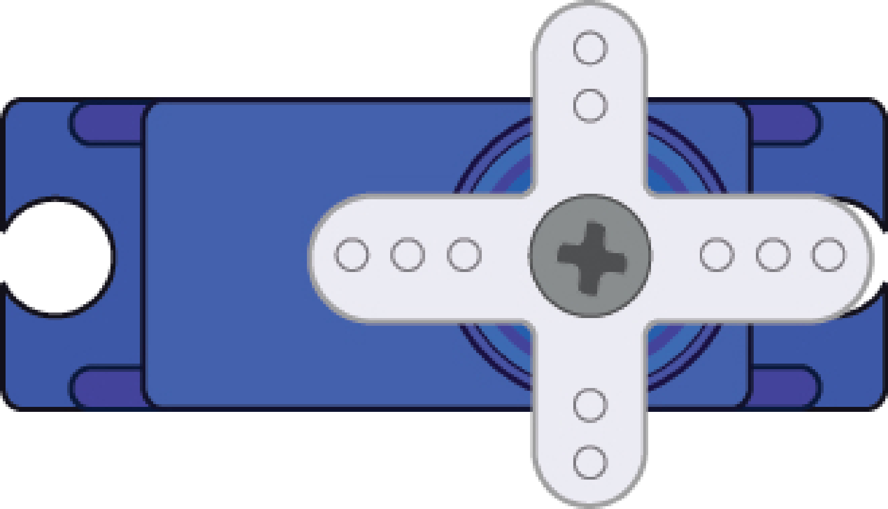
[picture p379: page 1]
