BrownDogGadgets/CrazyCircuits/User Guides/Part Graphics/Slide Switch.pdf

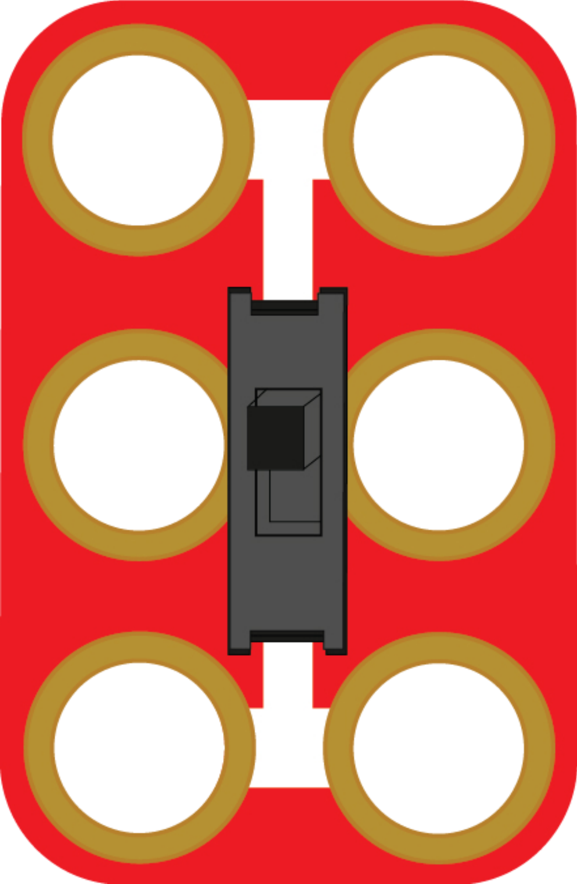
[picture p380: page 1]
