BrownDogGadgets/CrazyCircuits/User Guides/Part Graphics/Speaker Piezo.pdf

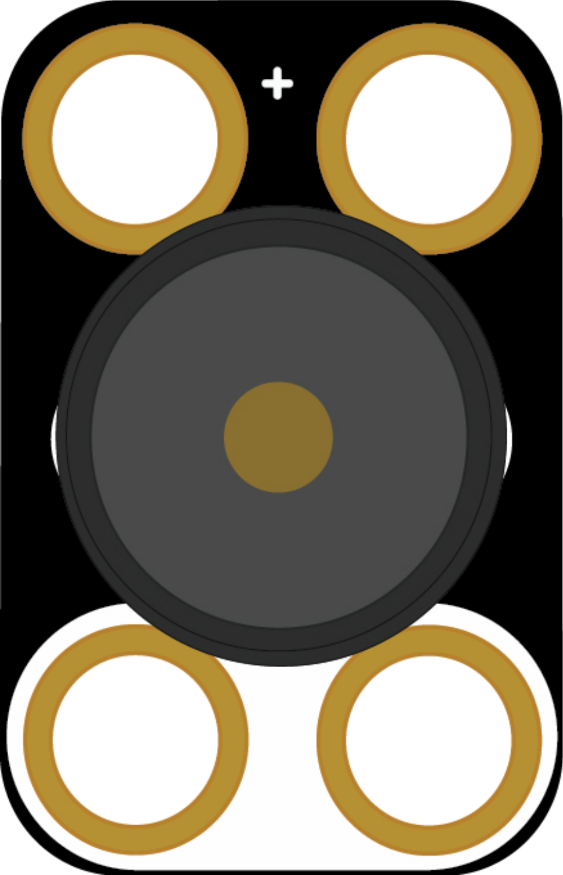
[picture p381: page 1]
