BrownDogGadgets/CrazyCircuits/User Guides/Part Graphics/tilt switch.pdf

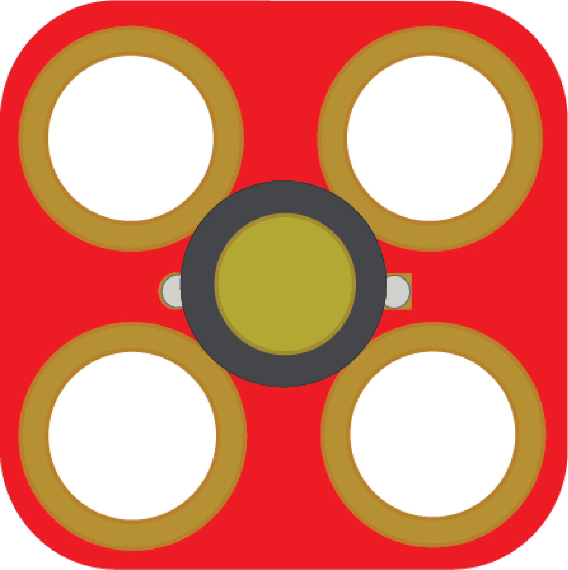
[picture p382: page 1]
