BrownDogGadgets/CrazyCircuits/Circuit-Kits/Modules/1x3-Button-Momentary/assembly.png

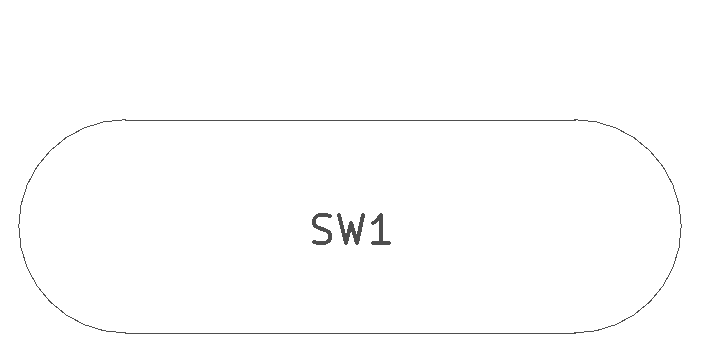
Circuit-Kits/Modules/1x3-Button-Momentary/assembly.png
