BrownDogGadgets/CrazyCircuits/Circuit-Kits/Modules/2x2-Generic-2.54mm-Pitch/assembly.png

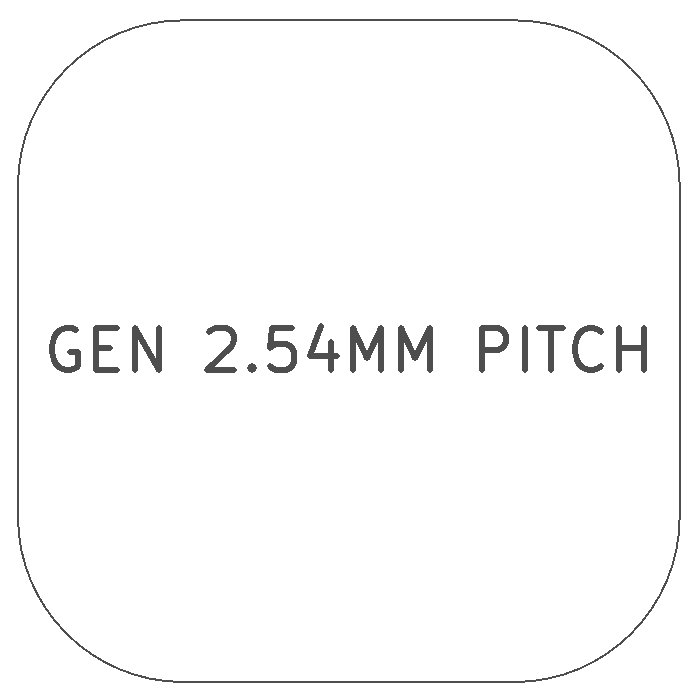
Circuit-Kits/Modules/2x2-Generic-2.54mm-Pitch/assembly.png
