BrownDogGadgets/CrazyCircuits/Circuit-Kits/Modules/2x2-Generic-5mm-Pitch/assembly.png

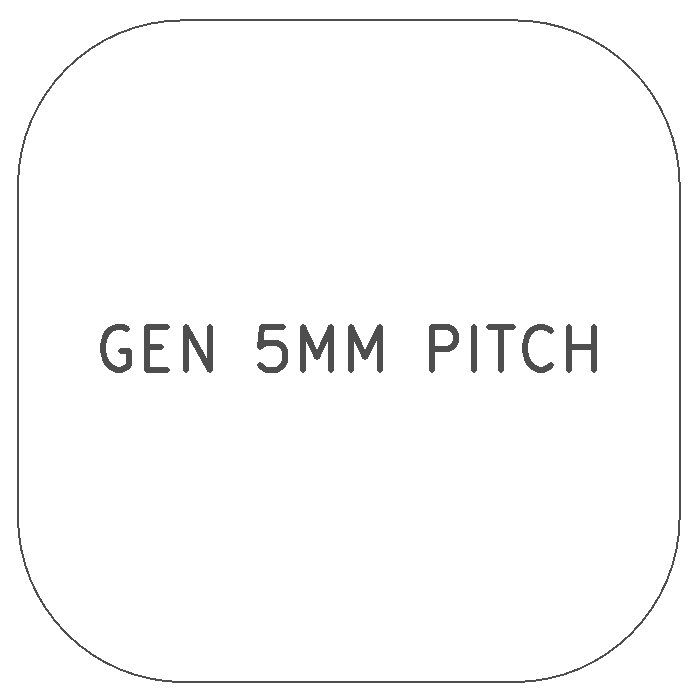
Circuit-Kits/Modules/2x2-Generic-5mm-Pitch/assembly.png
