BrownDogGadgets/CrazyCircuits/Circuit-Kits/Modules/2x2-Generic-1206-SMT/assembly.png

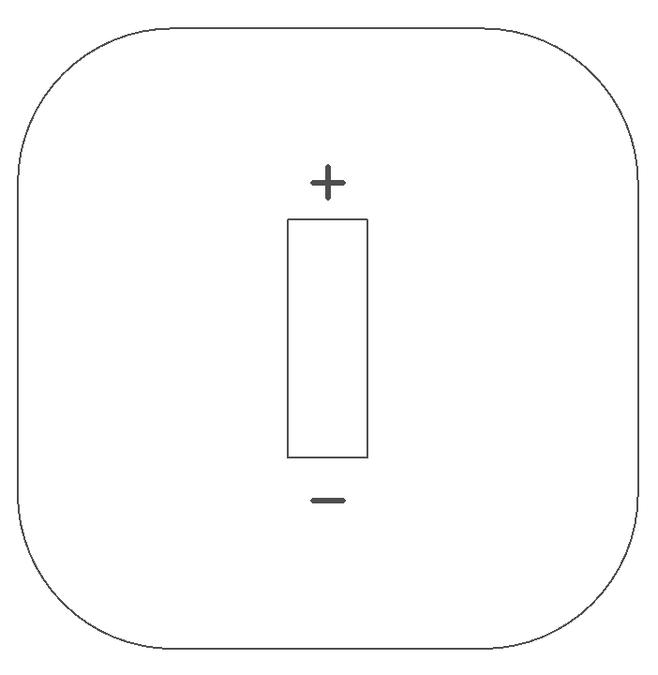
Circuit-Kits/Modules/2x2-Generic-1206-SMT/assembly.png
