BrownDogGadgets/CrazyCircuits/Circuit-Kits/Modules/2x3-Speaker-TH-5mm-Pitch/assembly.png

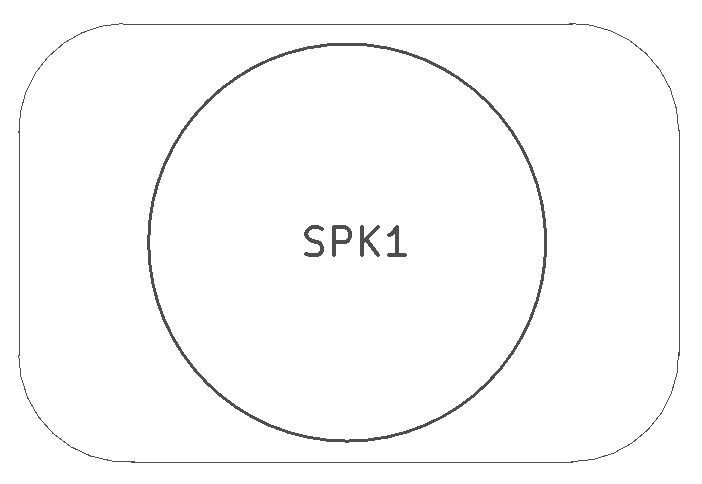
Circuit-Kits/Modules/2x3-Speaker-TH-5mm-Pitch/assembly.png
