BrownDogGadgets/CrazyCircuits/Circuit-Kits/Modules/2x4-12mm-Square-SMT-Pushbutton/assembly.png

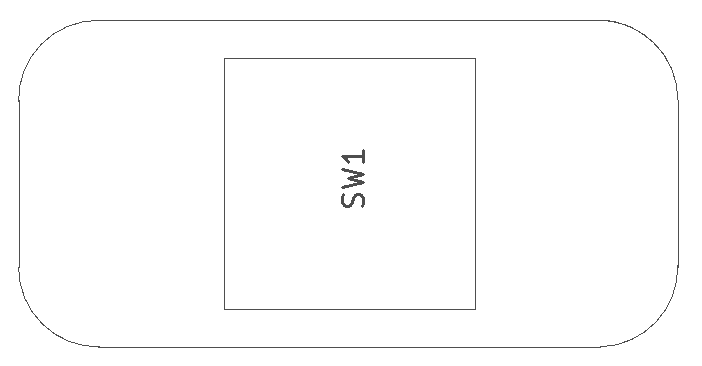
Circuit-Kits/Modules/2x4-12mm-Square-SMT-Pushbutton/assembly.png
