BrownDogGadgets/CrazyCircuits/Circuit-Kits/Modules/2x4-Cap-Touch-Slider/assembly.png

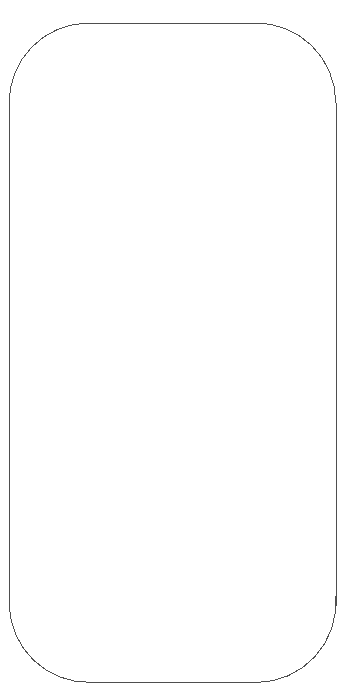
Circuit-Kits/Modules/2x4-Cap-Touch-Slider/assembly.png
