BrownDogGadgets/CrazyCircuits/Circuit-Kits/Modules/5x10-Arduino-Nano-Breakout/assembly.png

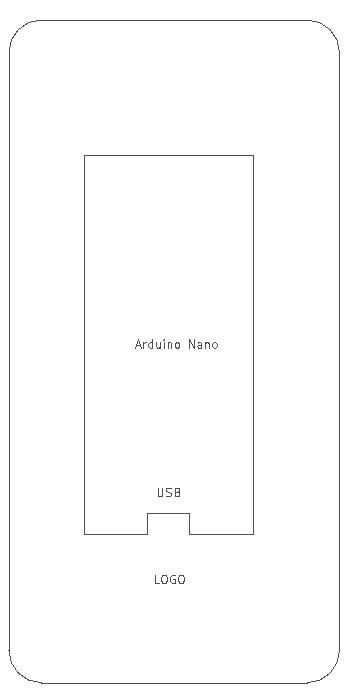
Circuit-Kits/Modules/5x10-Arduino-Nano-Breakout/assembly.png
