BrownDogGadgets/CrazyCircuits/Circuit-Kits/Modules/7x11-RasPi-Zero-Breakout/assembly.png

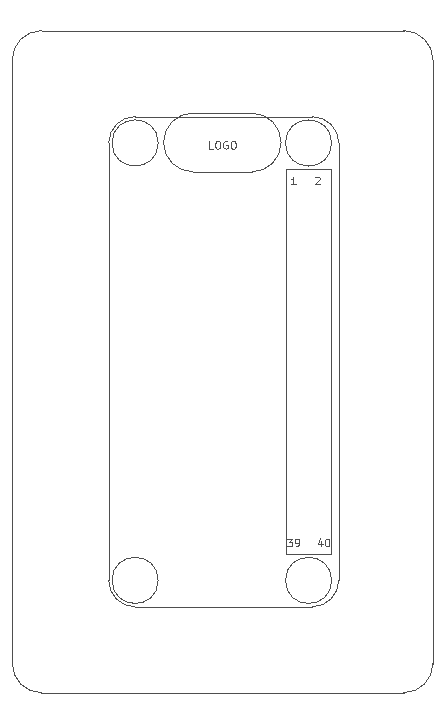
Circuit-Kits/Modules/7x11-RasPi-Zero-Breakout/assembly.png
