BrownDogGadgets/CrazyCircuits/Laser Cut Files/NES Controller/Wooden Controller Wiring.png

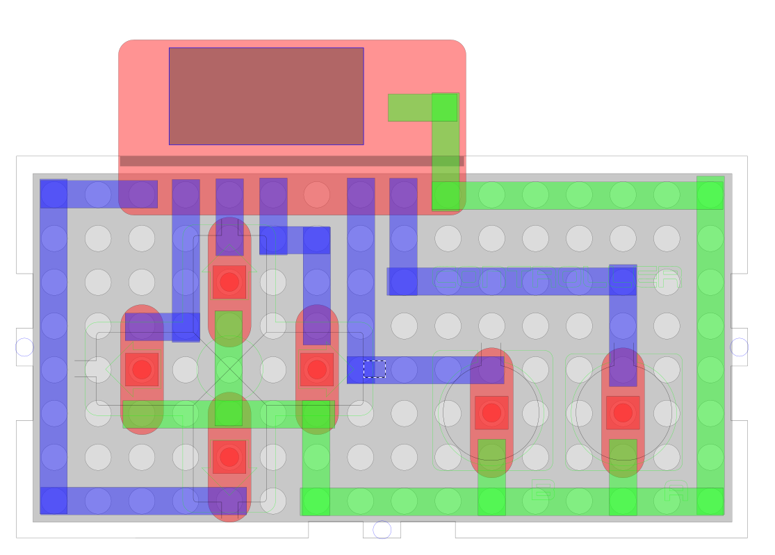
Laser Cut Files/NES Controller/Wooden Controller Wiring.png
