BrownDogGadgets/CrazyCircuits/Development/test-boards/Logo_Test/README.md

<!--- start title --->
# Crazy Circuits Logo Test v1.0
Temporary project to create logo before making a module.

Updated: 27 Dec 2016

Website: http://browndoggadgets.com/
Company: Brown Dog Gadgets
License: All rights reserved.

<!--- end title --->
Intro text.

### Bill of Materials

<!--- bom start --->
<!--- bom end --->
Assembly Diagram

Gerber Preview
