BrownDogGadgets/CrazyCircuits/Development/test-boards/Sample-Set/README.md

# Sample Set

Contains:
  
- DIP8 breakout 
- Teensy 3.2/LC Breakout 
- CR2032 battery 3x3 
- Generic 2.54mm pitch 2x2 
- Generic 5mm pitch 2x2 
- LED 2.54mm pitch 2x2 (for 5mm LEDs) 
- LED 5mm pitch 2x2 (for 10mm LEDs) 
- 4-pin RGB LED 2x2 
- 3-position Switch 2x2 
- Touch 2x2 
- Pushbutton 1x3
