BrownDogGadgets/CrazyCircuits/Development/test-boards/Drill-Hole-Size-Test/IMAG0544.jpg

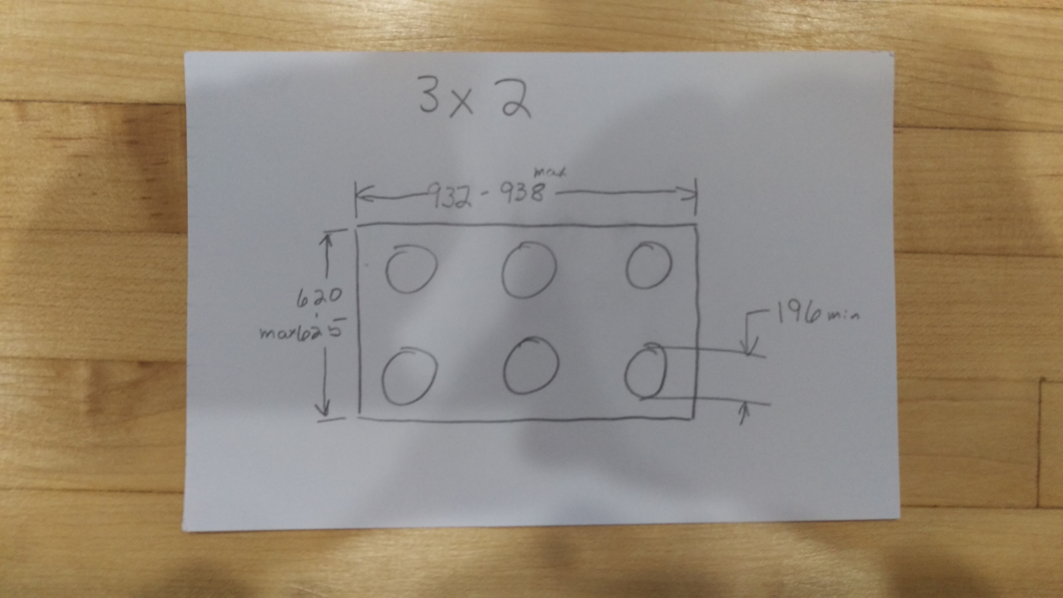
Development/test-boards/Drill-Hole-Size-Test/IMAG0544.jpg
