BrownDogGadgets/CrazyCircuits/Development/test-boards/Drill-Hole-Size-Test/IMAG0546.jpg

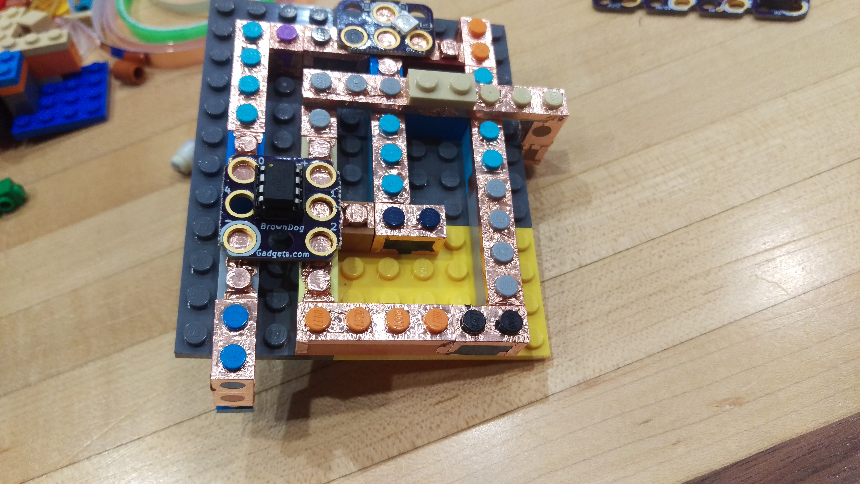
Development/test-boards/Drill-Hole-Size-Test/IMAG0546.jpg
