BrownDogGadgets/CrazyCircuits/Development/test-boards/HISTORICAL-Initial-Lego-Sizing-Test/boards-subpanel.png

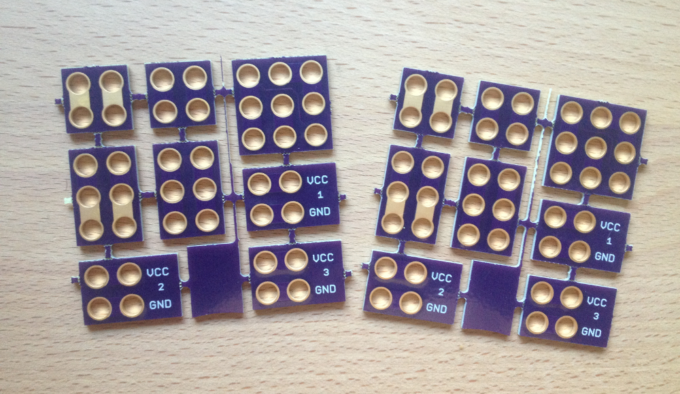
Development/test-boards/HISTORICAL-Initial-Lego-Sizing-Test/boards-subpanel.png
