BrownDogGadgets/CrazyCircuits/Development/test-boards/HISTORICAL-Initial-Lego-Sizing-Test/lego-fit.png

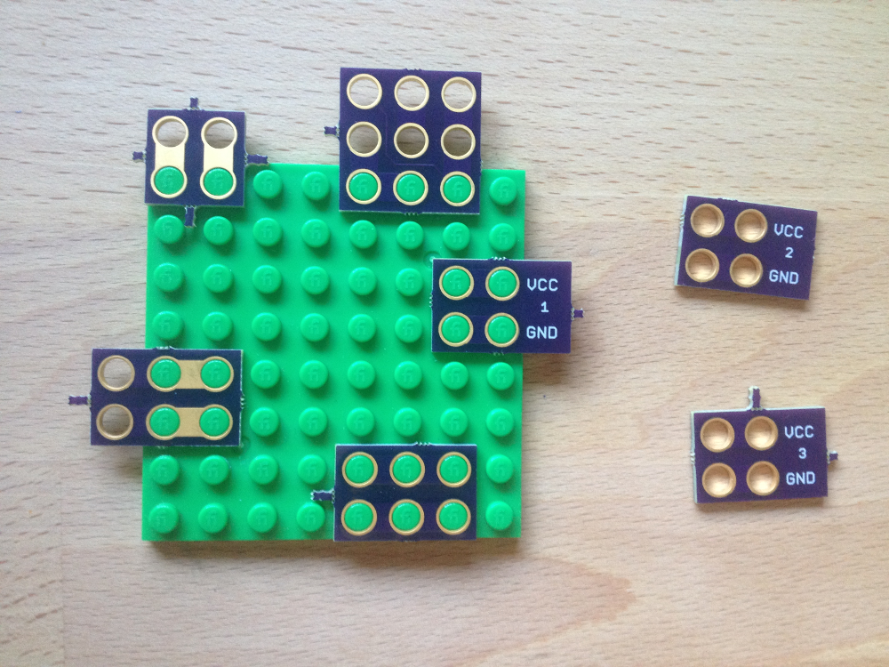
Development/test-boards/HISTORICAL-Initial-Lego-Sizing-Test/lego-fit.png
