BrownDogGadgets/CrazyCircuits/Development/test-boards/HISTORICAL-Initial-Lego-Sizing-Test/lego-milling-tests.png

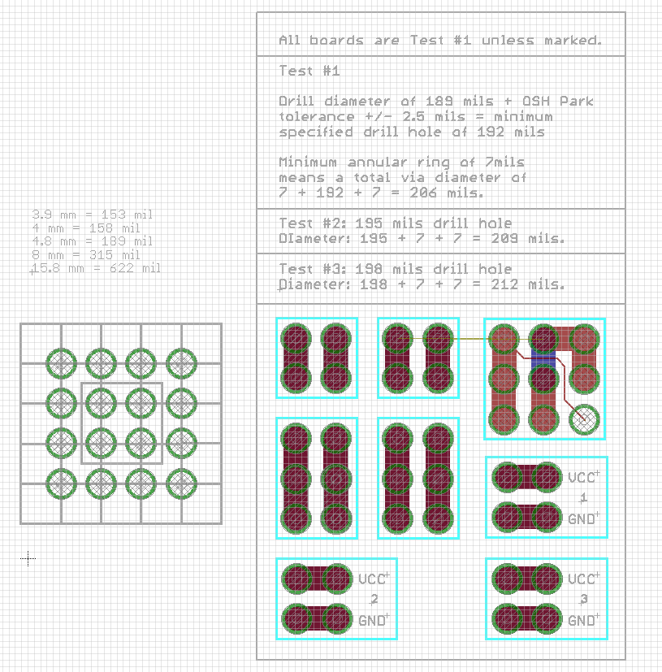
Development/test-boards/HISTORICAL-Initial-Lego-Sizing-Test/lego-milling-tests.png
