BrownDogGadgets/CrazyCircuits/Development/test-boards/HISTORICAL-Initial-Lego-Sizing-Test/side-view.png

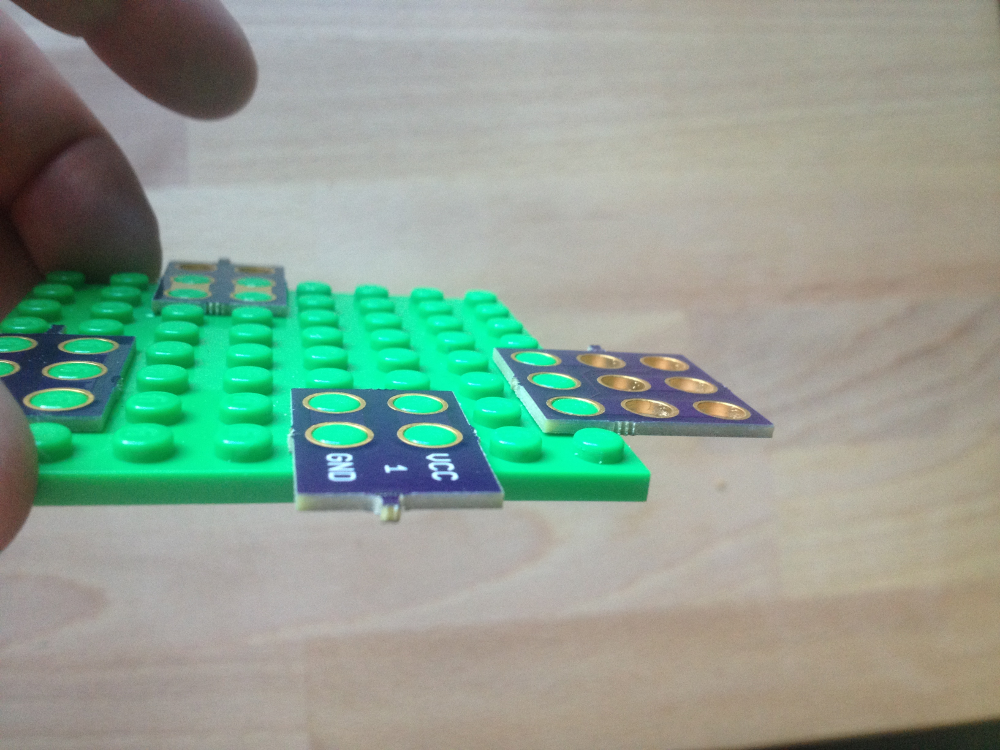
Development/test-boards/HISTORICAL-Initial-Lego-Sizing-Test/side-view.png
