BrownDogGadgets/CrazyCircuits/User Guides/Part Mini Guides/Battery Holder.pdf

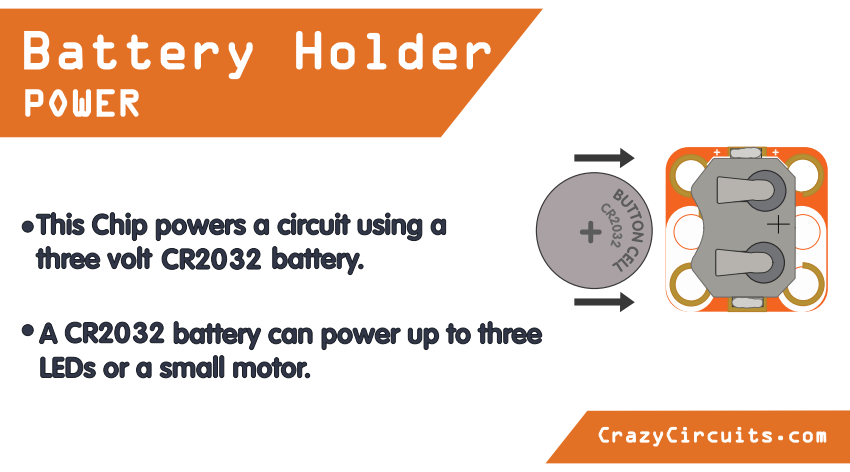
[picture p405: page 1]
+ Battery

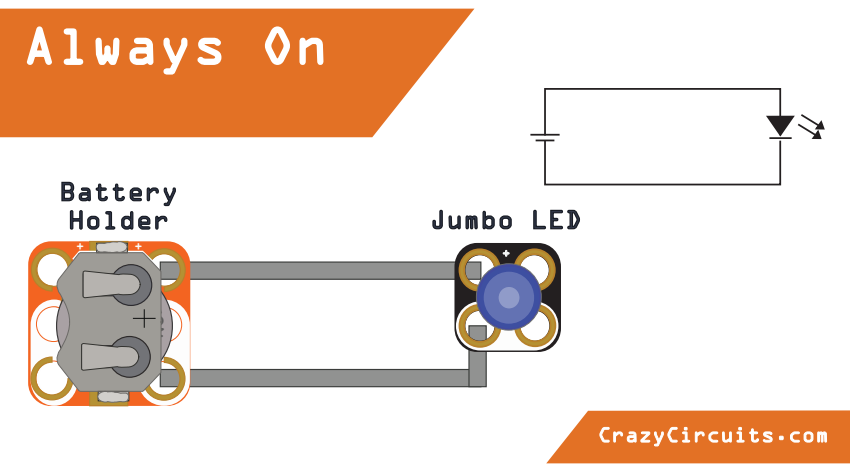
[picture p406: page 2]
+ Battery; BUTTO; N CELL
