BrownDogGadgets/CrazyCircuits/User Guides/Part Mini Guides/Blink Fade Board.pdf

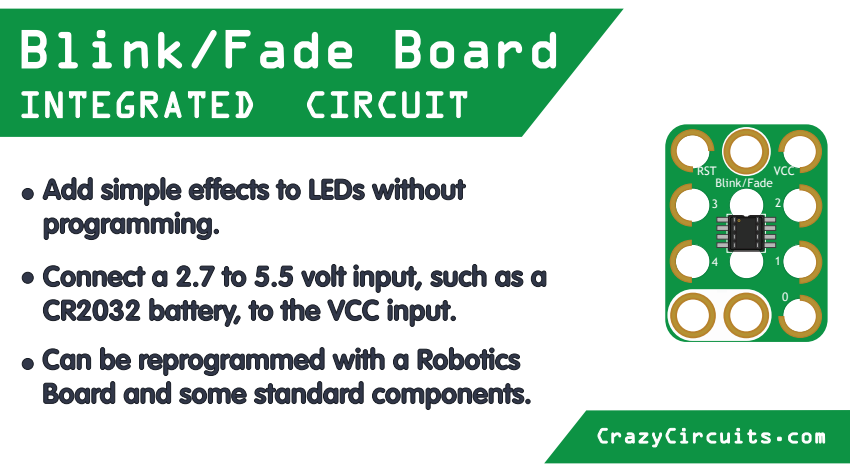
[picture p407: page 1]
RST; VCC; Blink/Fade

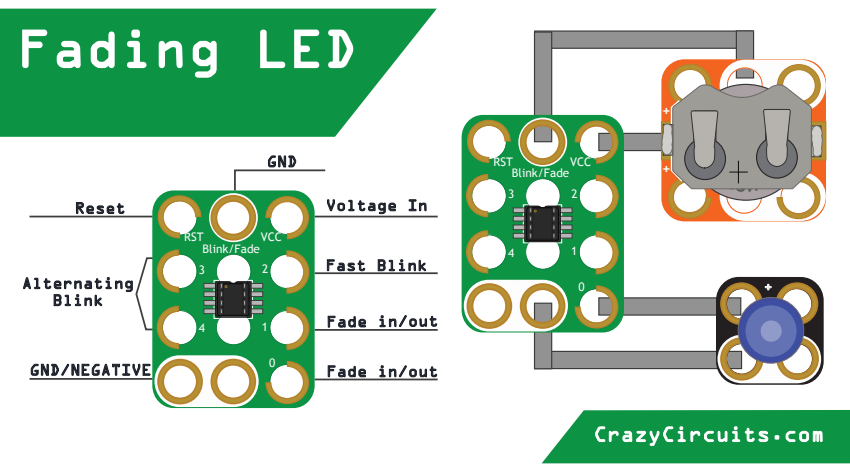
[picture p408: page 2]
RST; VCC; Blink/Fade; BUTTON CELL
