BrownDogGadgets/CrazyCircuits/User Guides/Part Mini Guides/LEDs.pdf

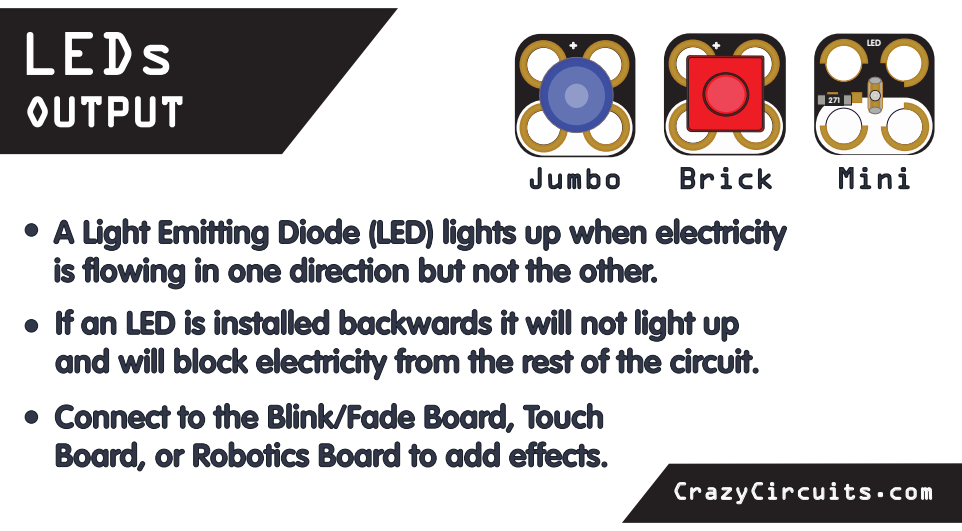
[picture p409: page 1]
CrazyCircuits.com; LED

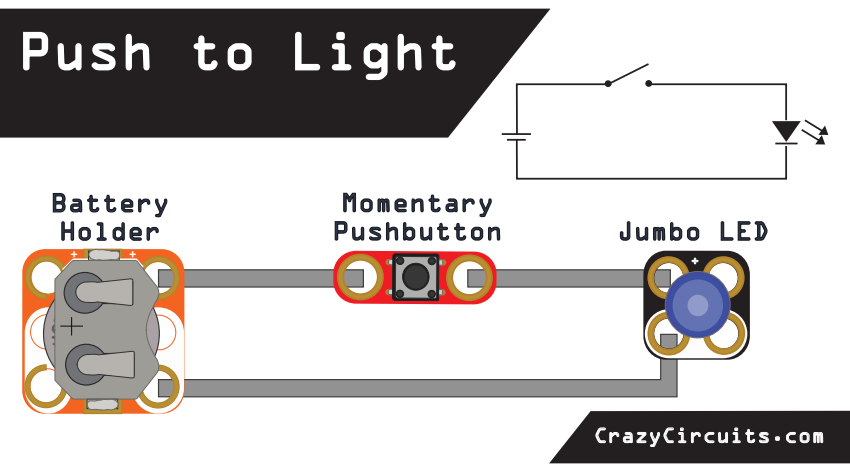
[picture p410: page 2]
CrazyCircuits.com; + Battery; UB TTO; N CELL
