BrownDogGadgets/CrazyCircuits/User Guides/Part Mini Guides/Male Headers.pdf

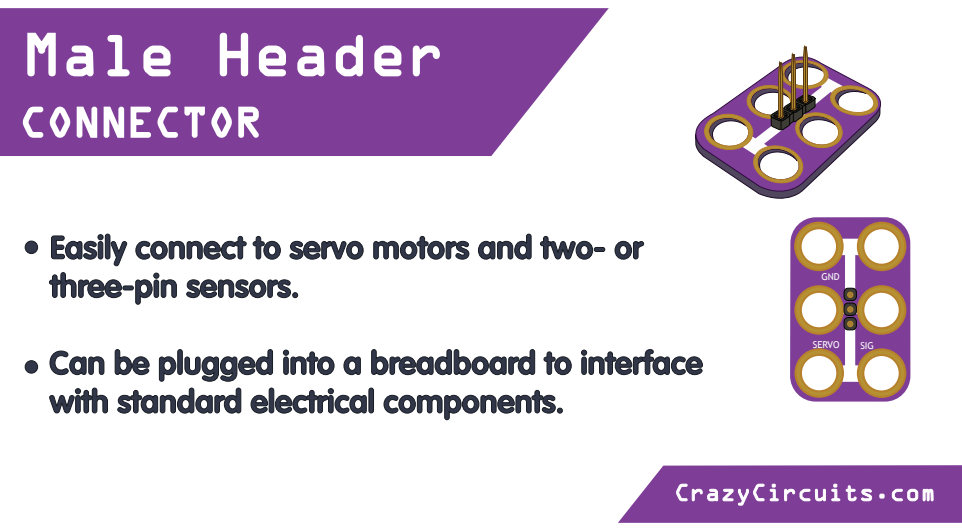
[picture p411: page 1]
GND; SERVO; SIG

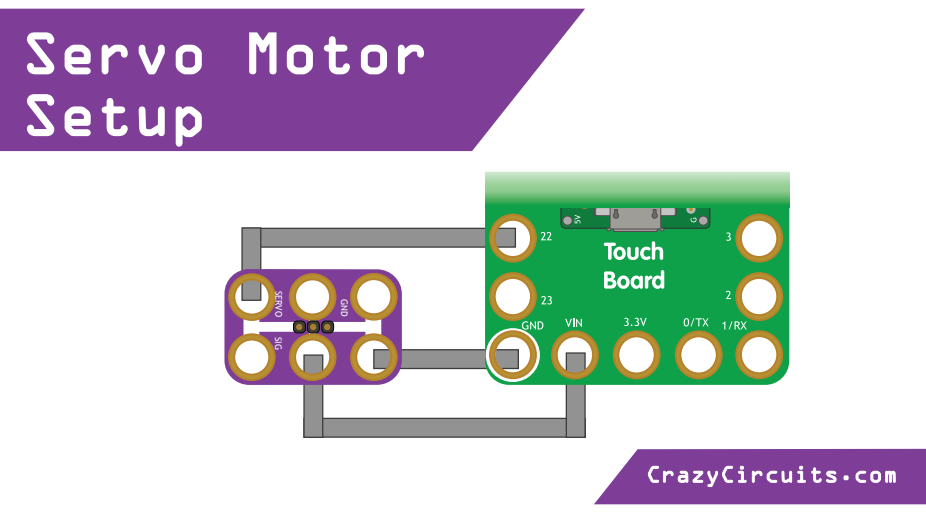
[picture p412: page 2]
GND; SIG SERVO
