BrownDogGadgets/CrazyCircuits/User Guides/Part Mini Guides/Piezo Speaker.pdf

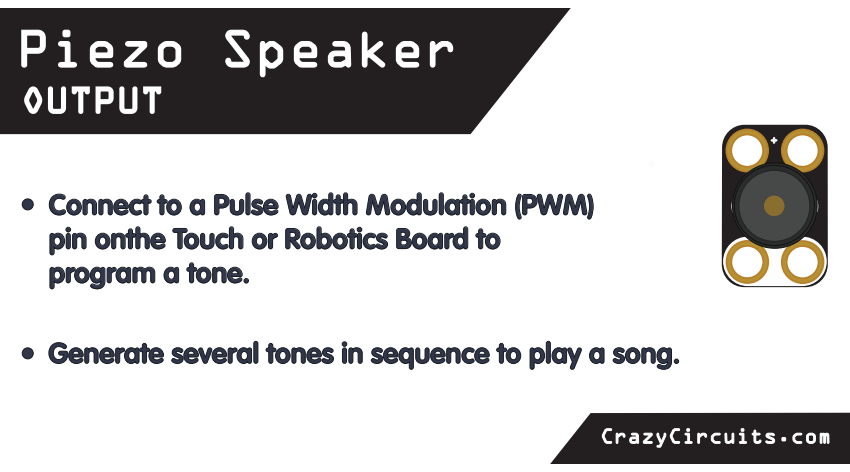
[picture p413: page 1]

Connect to a Pulse Width Modulation (PWM)
pin onthe Touch or Robotics Board to
program a tone.

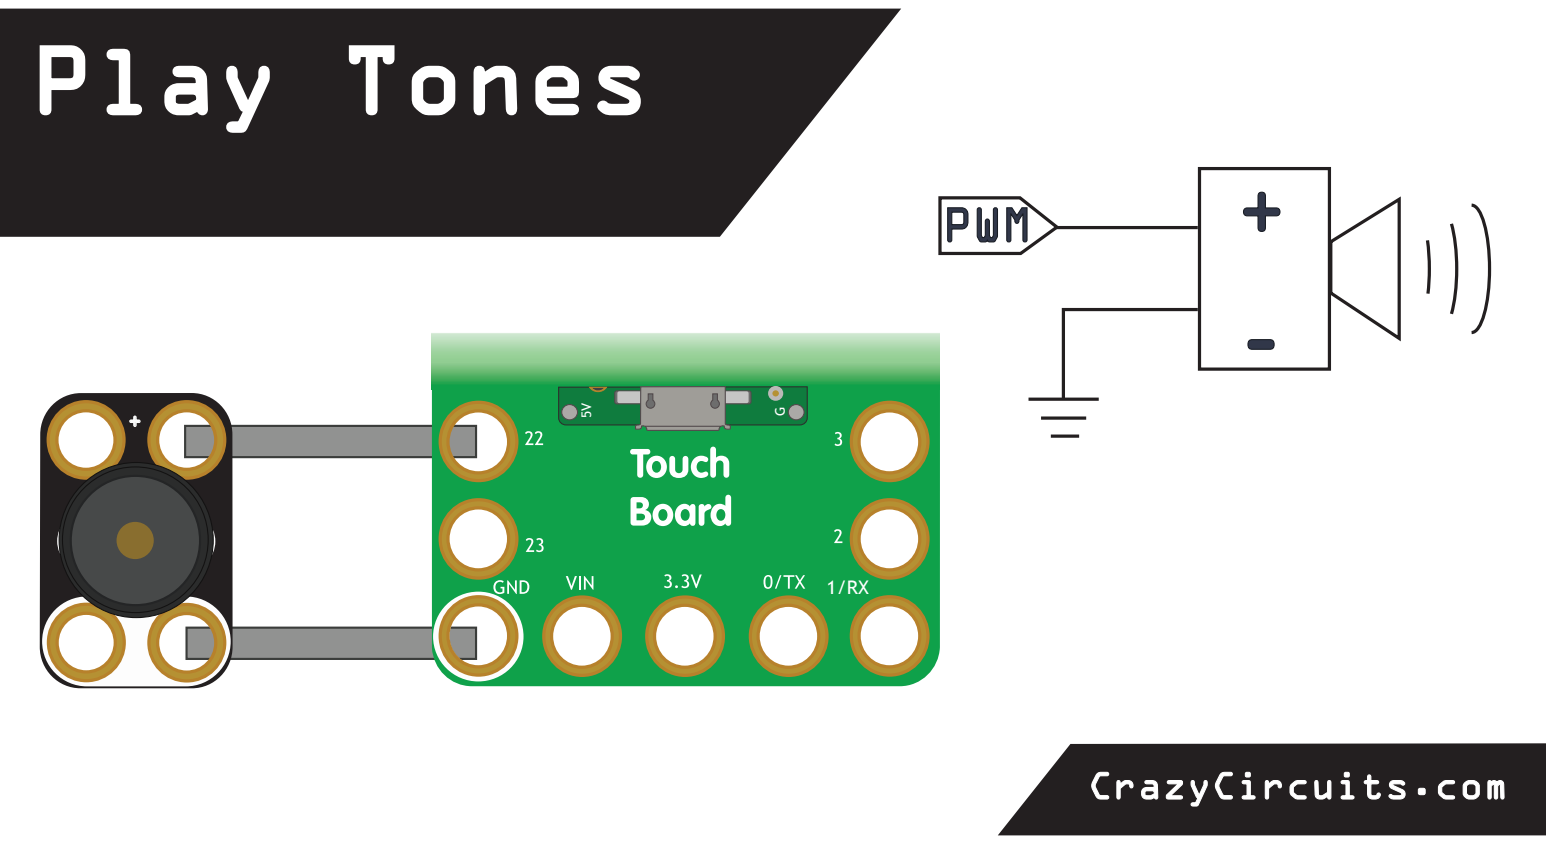
[picture p414: page 2]
