BrownDogGadgets/CrazyCircuits/User Guides/Part Mini Guides/Pushbutton.pdf

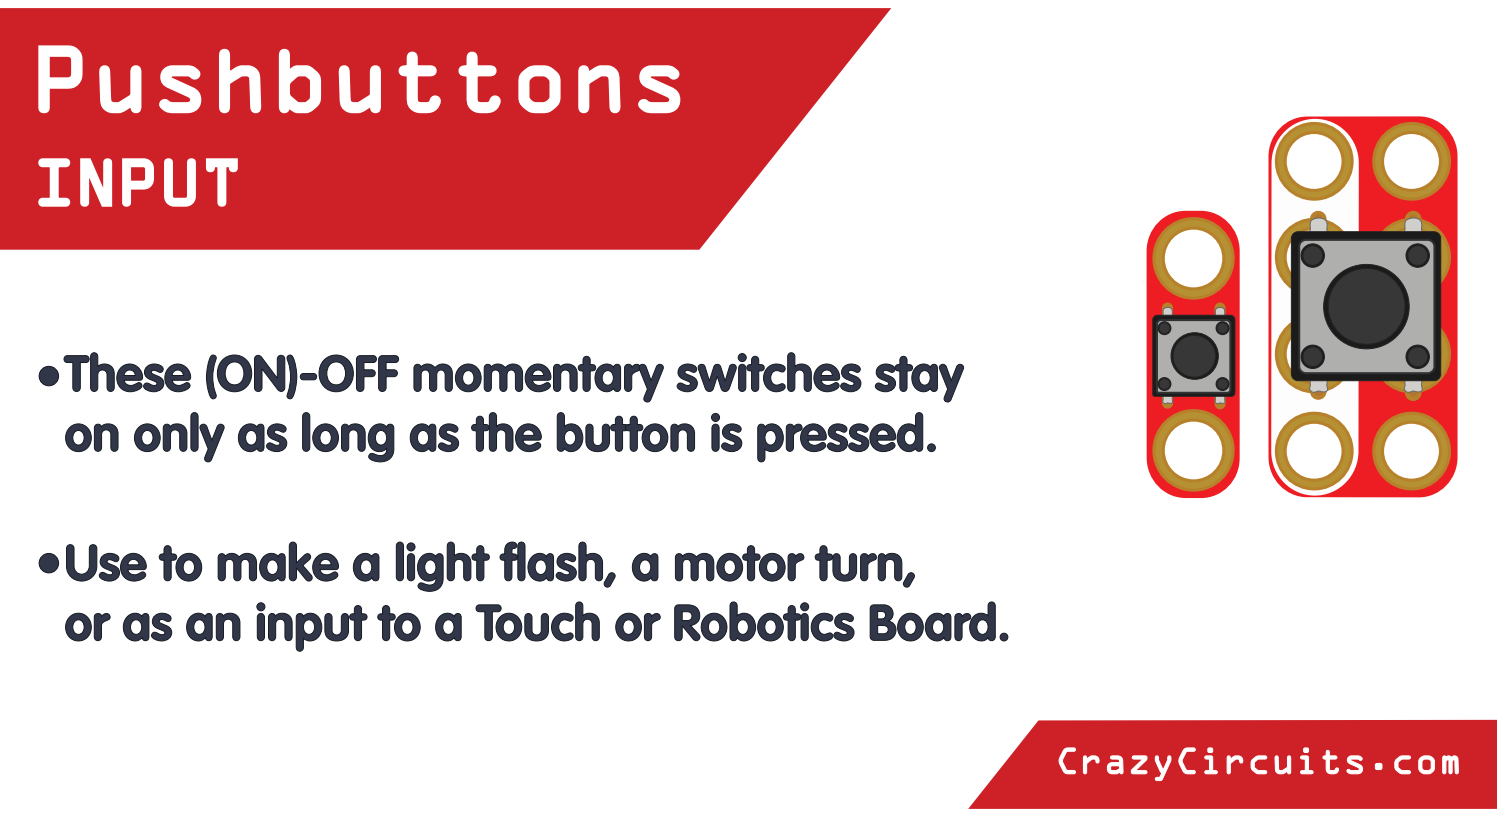
[picture p415: page 1]

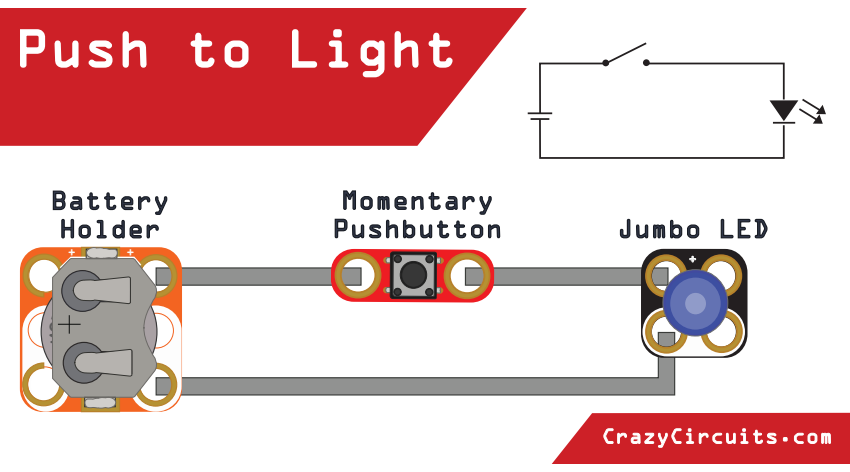
[picture p416: page 2]
+ Battery; UB TTO; N CELL
