BrownDogGadgets/CrazyCircuits/User Guides/Part Mini Guides/Slide Switch.pdf

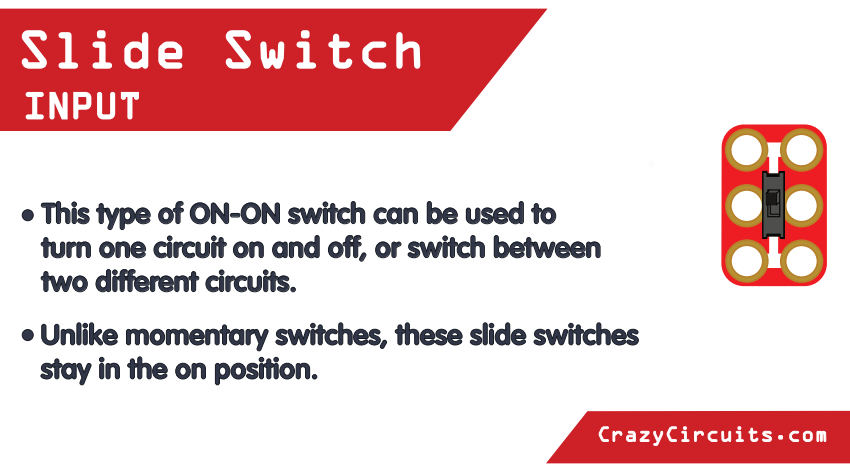
[picture p417: page 1]

This type of ON-ON switch can be used to
turn one circuit on and off, or switch between
two different circuits.

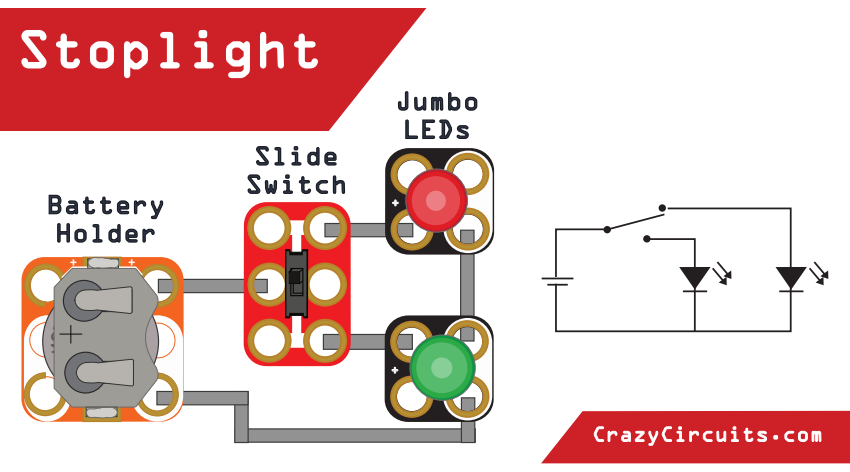
[picture p418: page 2]
+ Battery; UB TTO; N CELL
