BrownDogGadgets/CrazyCircuits/Development/test-boards/Sample-Set/gerbers/Sample-Set-AssyOutlinesTop.pdf

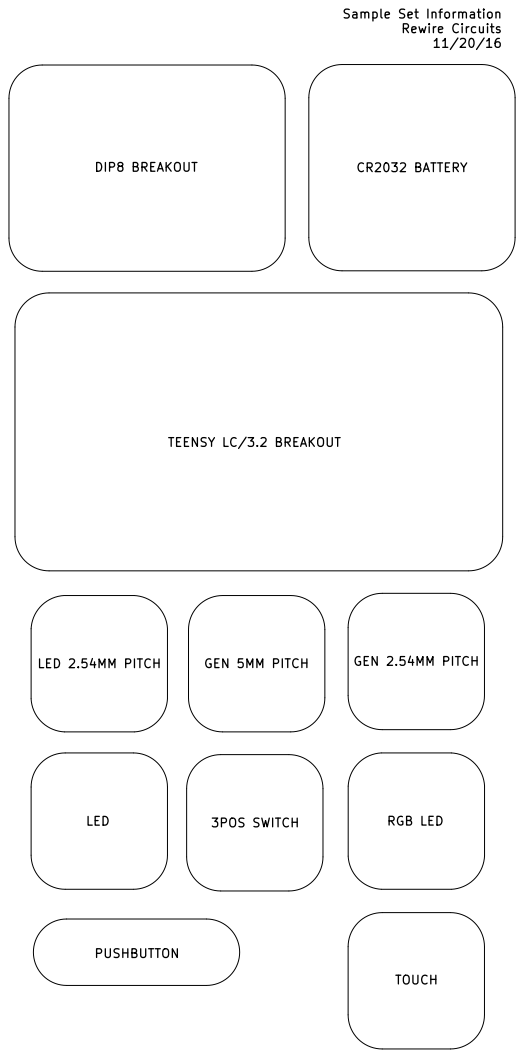
[picture p419: page 1]

Sample Set Information Rewire Circuits
TEENSY LC/3.2 BREAKOUT DIP8 BREAKOUT GEN 5MM PITCH
