BrownDogGadgets/CrazyCircuits/Projects/DHT11-TM1637-Temperature/DH22 Temperature.pdf

# DH22 Temperature to MT1637 Display

## For Arduino code, libraries, and

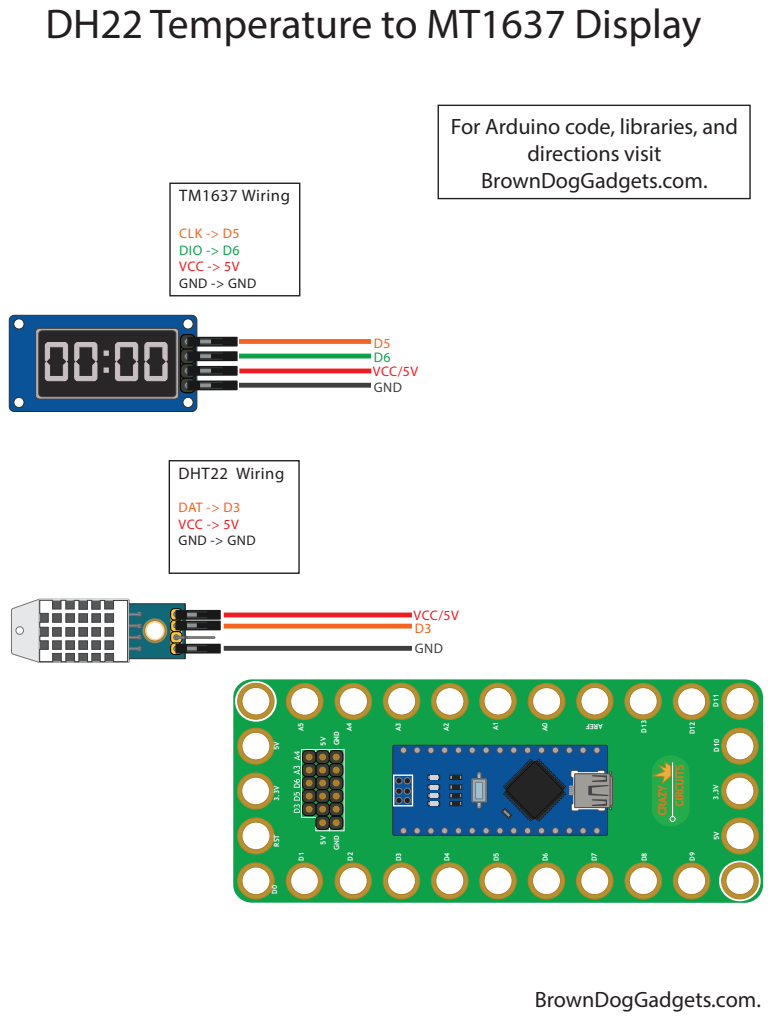
[picture p420: page 1]
