BrownDogGadgets/CrazyCircuits/Projects/SquishySound/doughSYNTH diagram.pdf

# Dough Synth

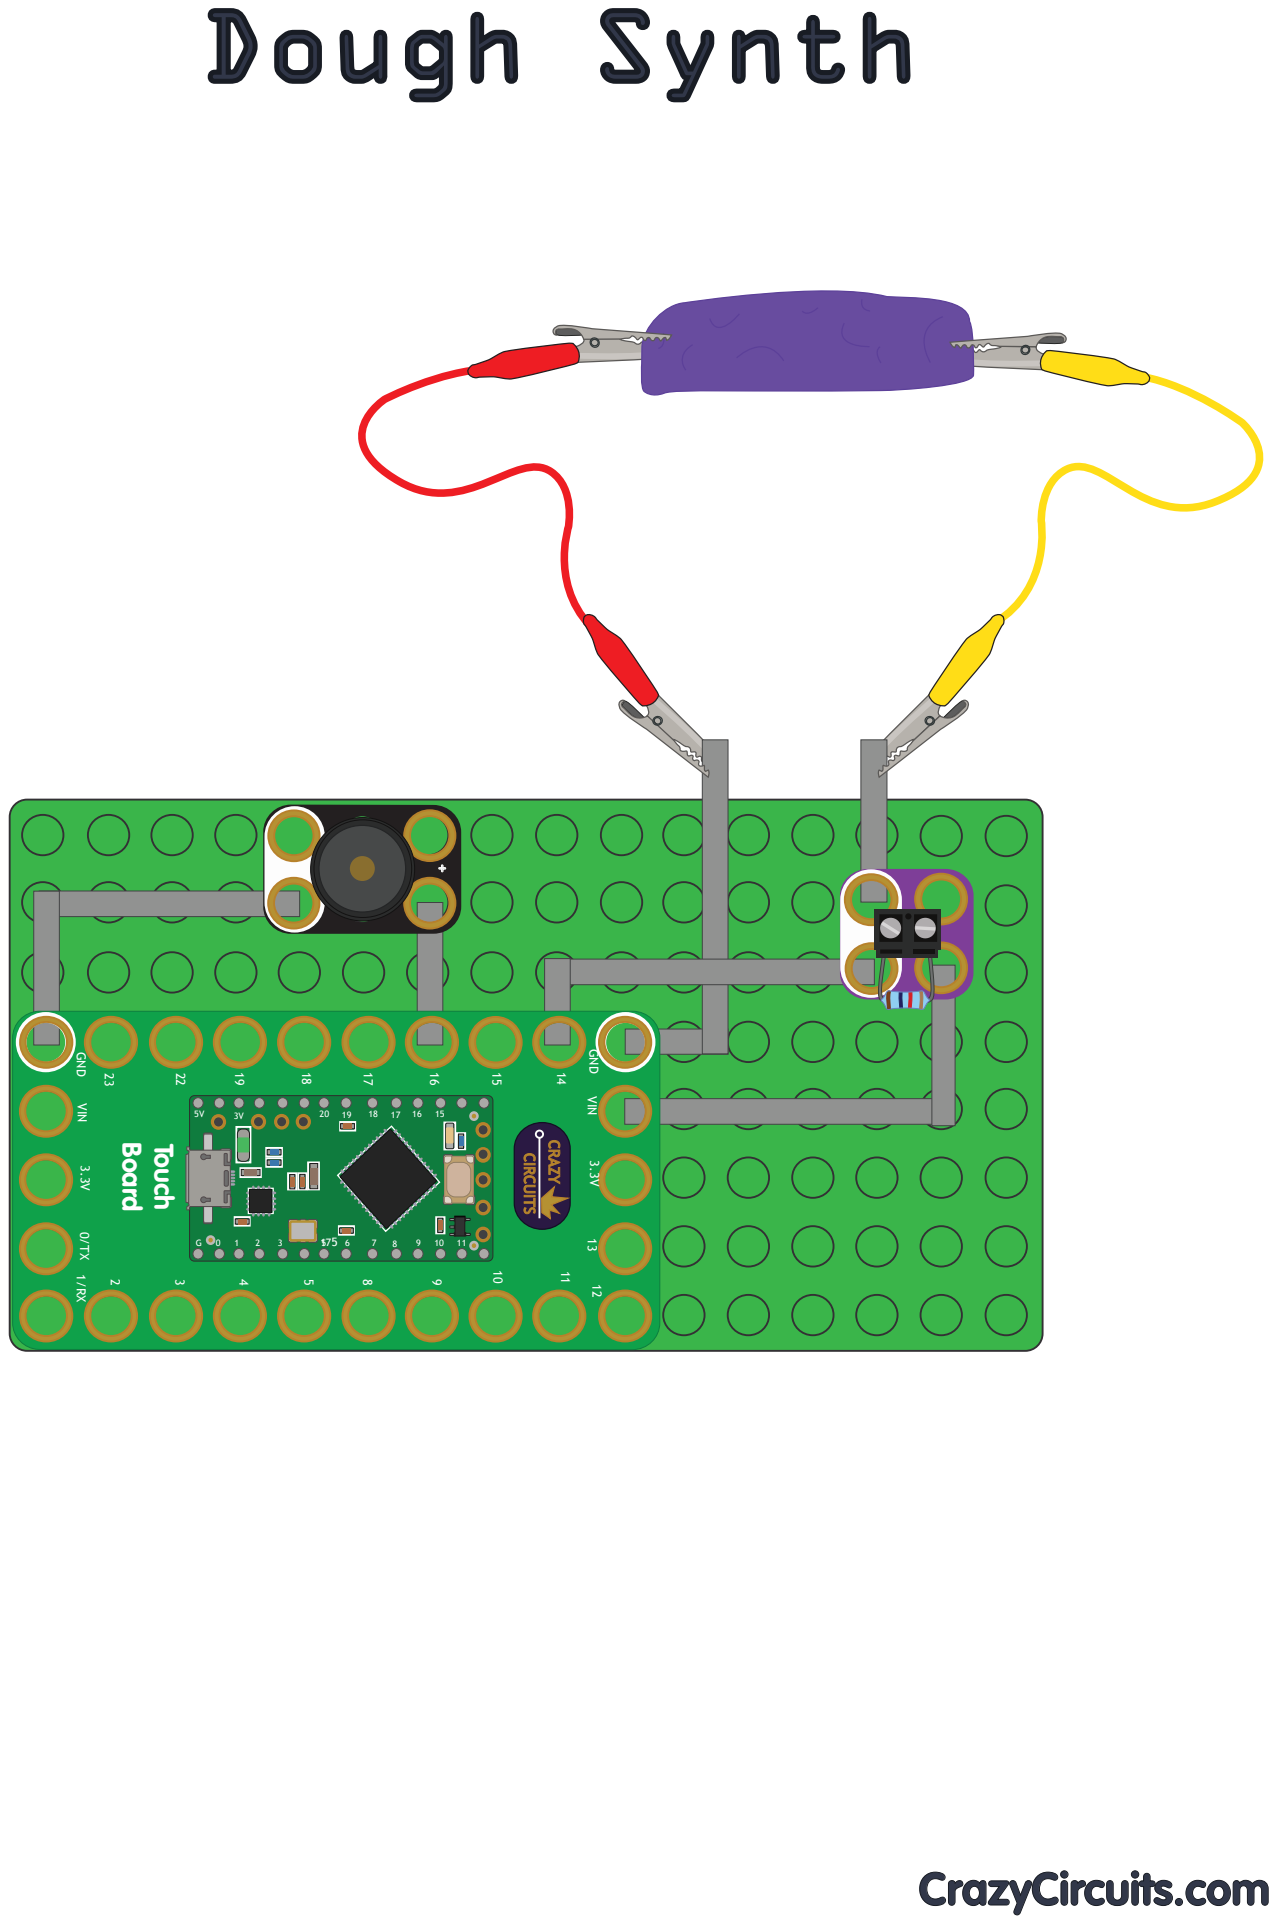
[picture p421: page 1]
CrazyCircuits.com; VIN; GND; CRAZY; CIRCUITS; Board Touch
