BrownDogGadgets/CrazyCircuits/Projects/Cylon Pumpkin/Cylon Pumpkin Robotics Board.pdf

# Robotics Board

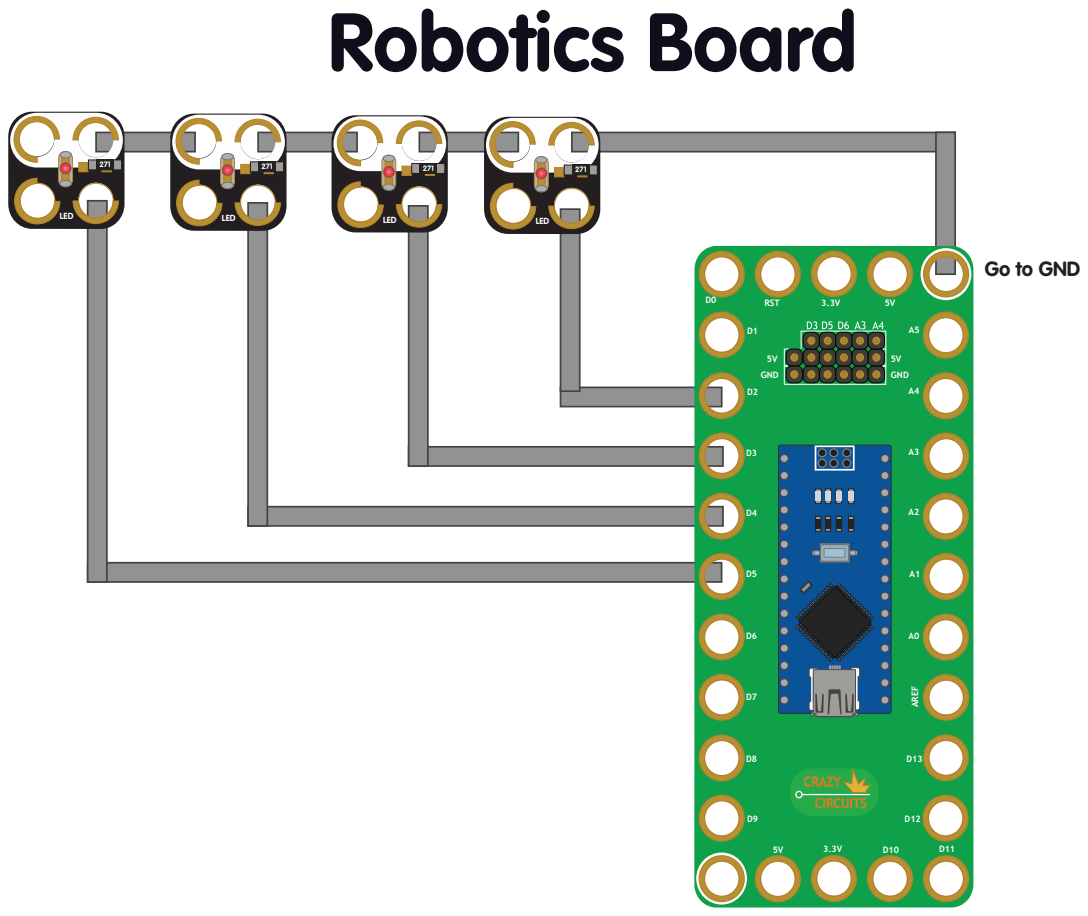
[picture p422: page 1]
