BrownDogGadgets/CrazyCircuits/Projects/Cylon Pumpkin/Cylon Pumpkin Touch Board.pdf

# Touch Board

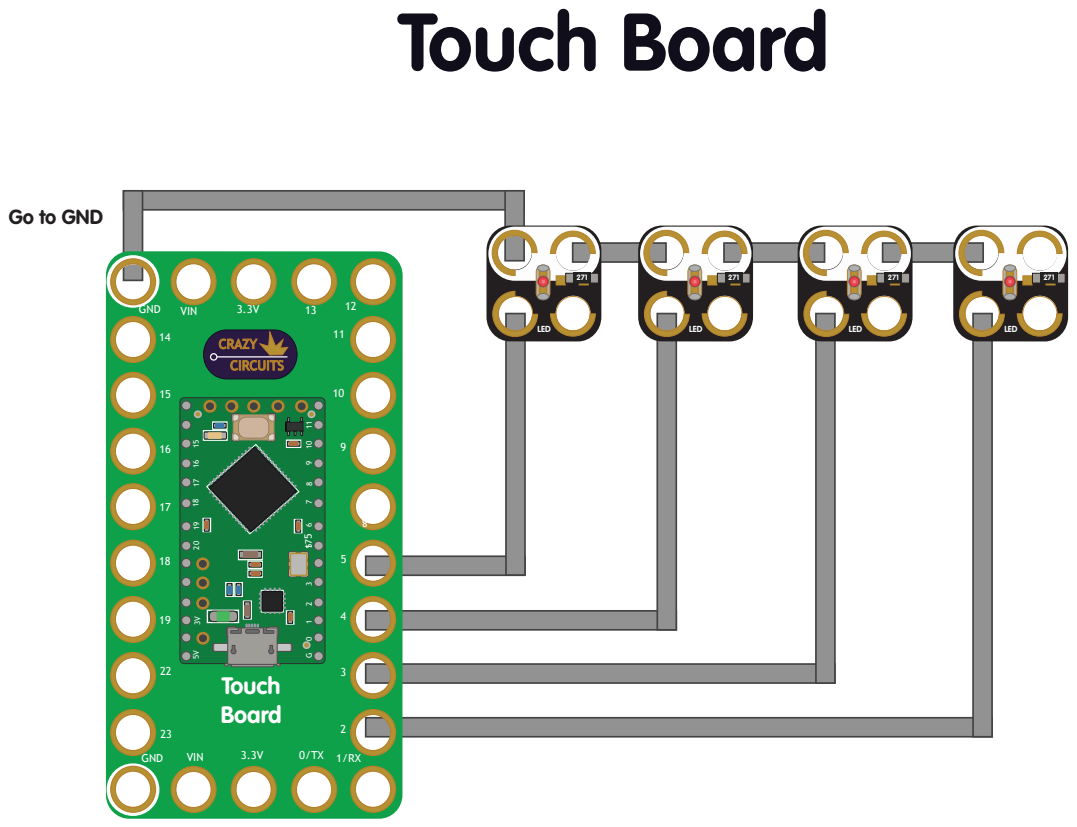
[picture p423: page 1]
LED; VIN; GND; CRAZY CIRCUITS; Touch Board

Go to GND
