BrownDogGadgets/CrazyCircuits/Projects/Touch Piano/Piano Diagram.pdf

# Conductive Paint Piano

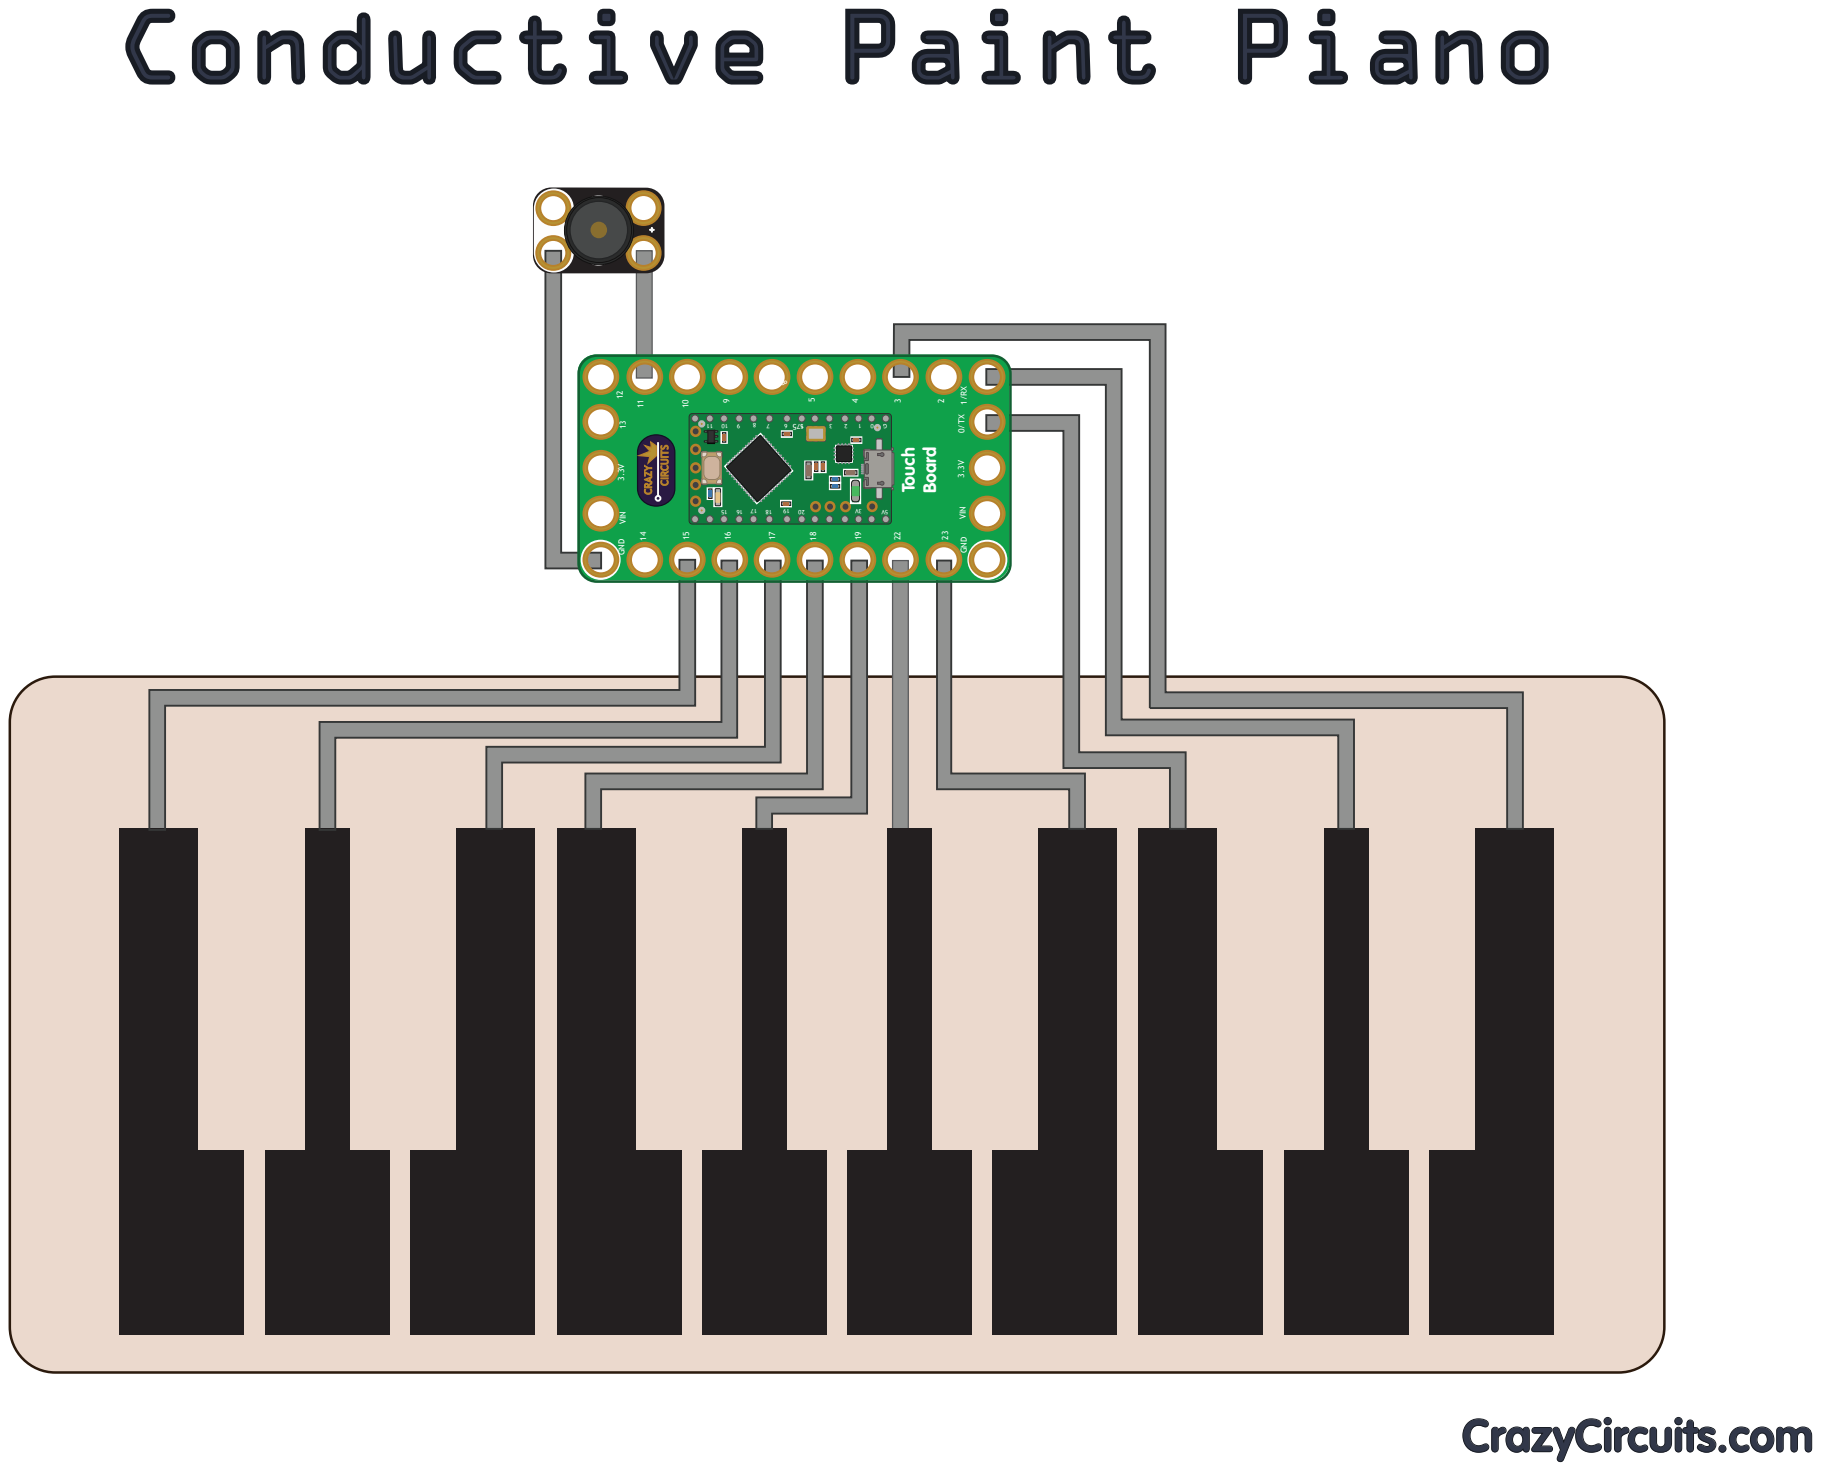
[picture p424: page 1]
CrazyCircuits.com; VIN; 3.3V GND; CRAZY; CIRCUITS; Touch; Board

GND 0/TX 1/RX
