BrownDogGadgets/CrazyCircuits/Projects/Touch LED/Touch LED Diagram.pdf

# LED Lighteup

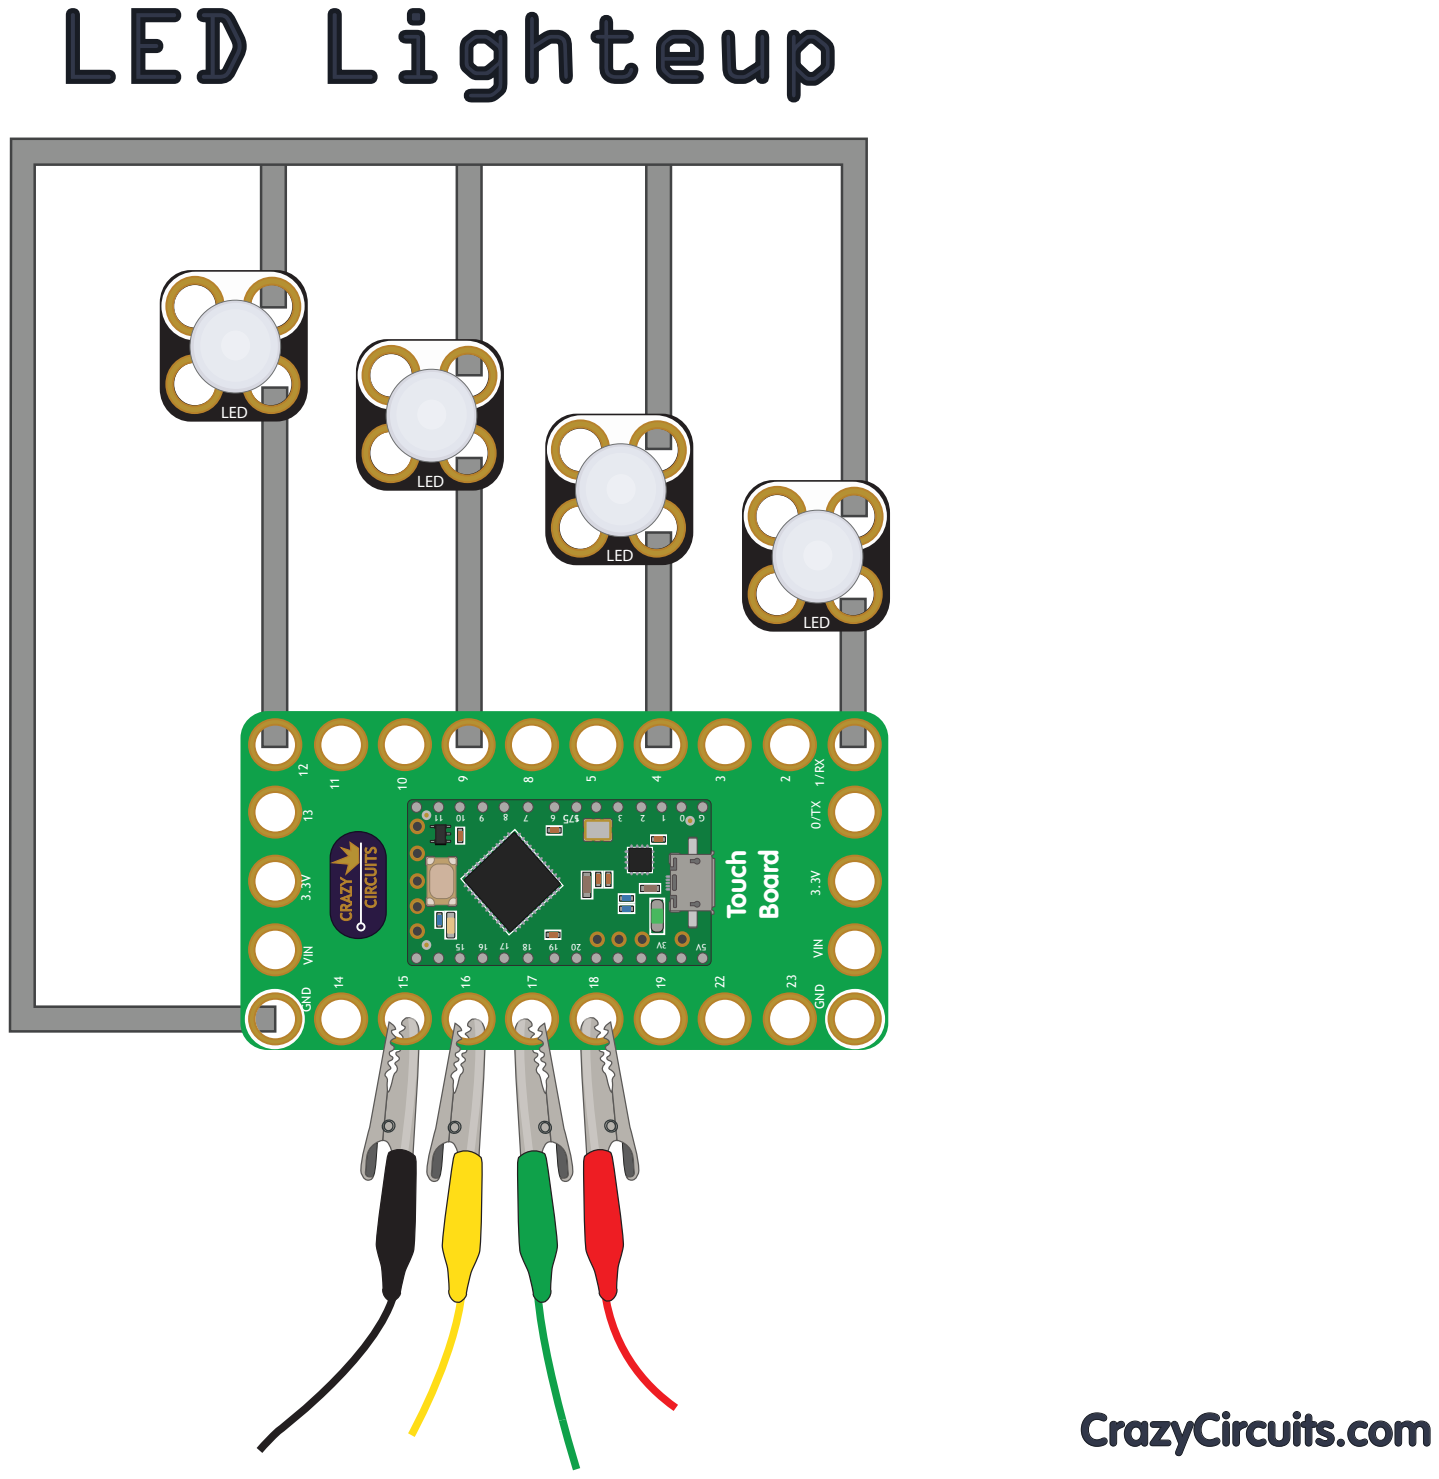
[picture p425: page 1]
VIN; 3.3V GND; CRAZY; CIRCUITS; Touch; Board LED; LED; CrazyCircuits.com

GND 0/TX 1/RX
