BrownDogGadgets/CrazyCircuits/Projects/Status Light/Status Light Diagram.pdf

## Inuse

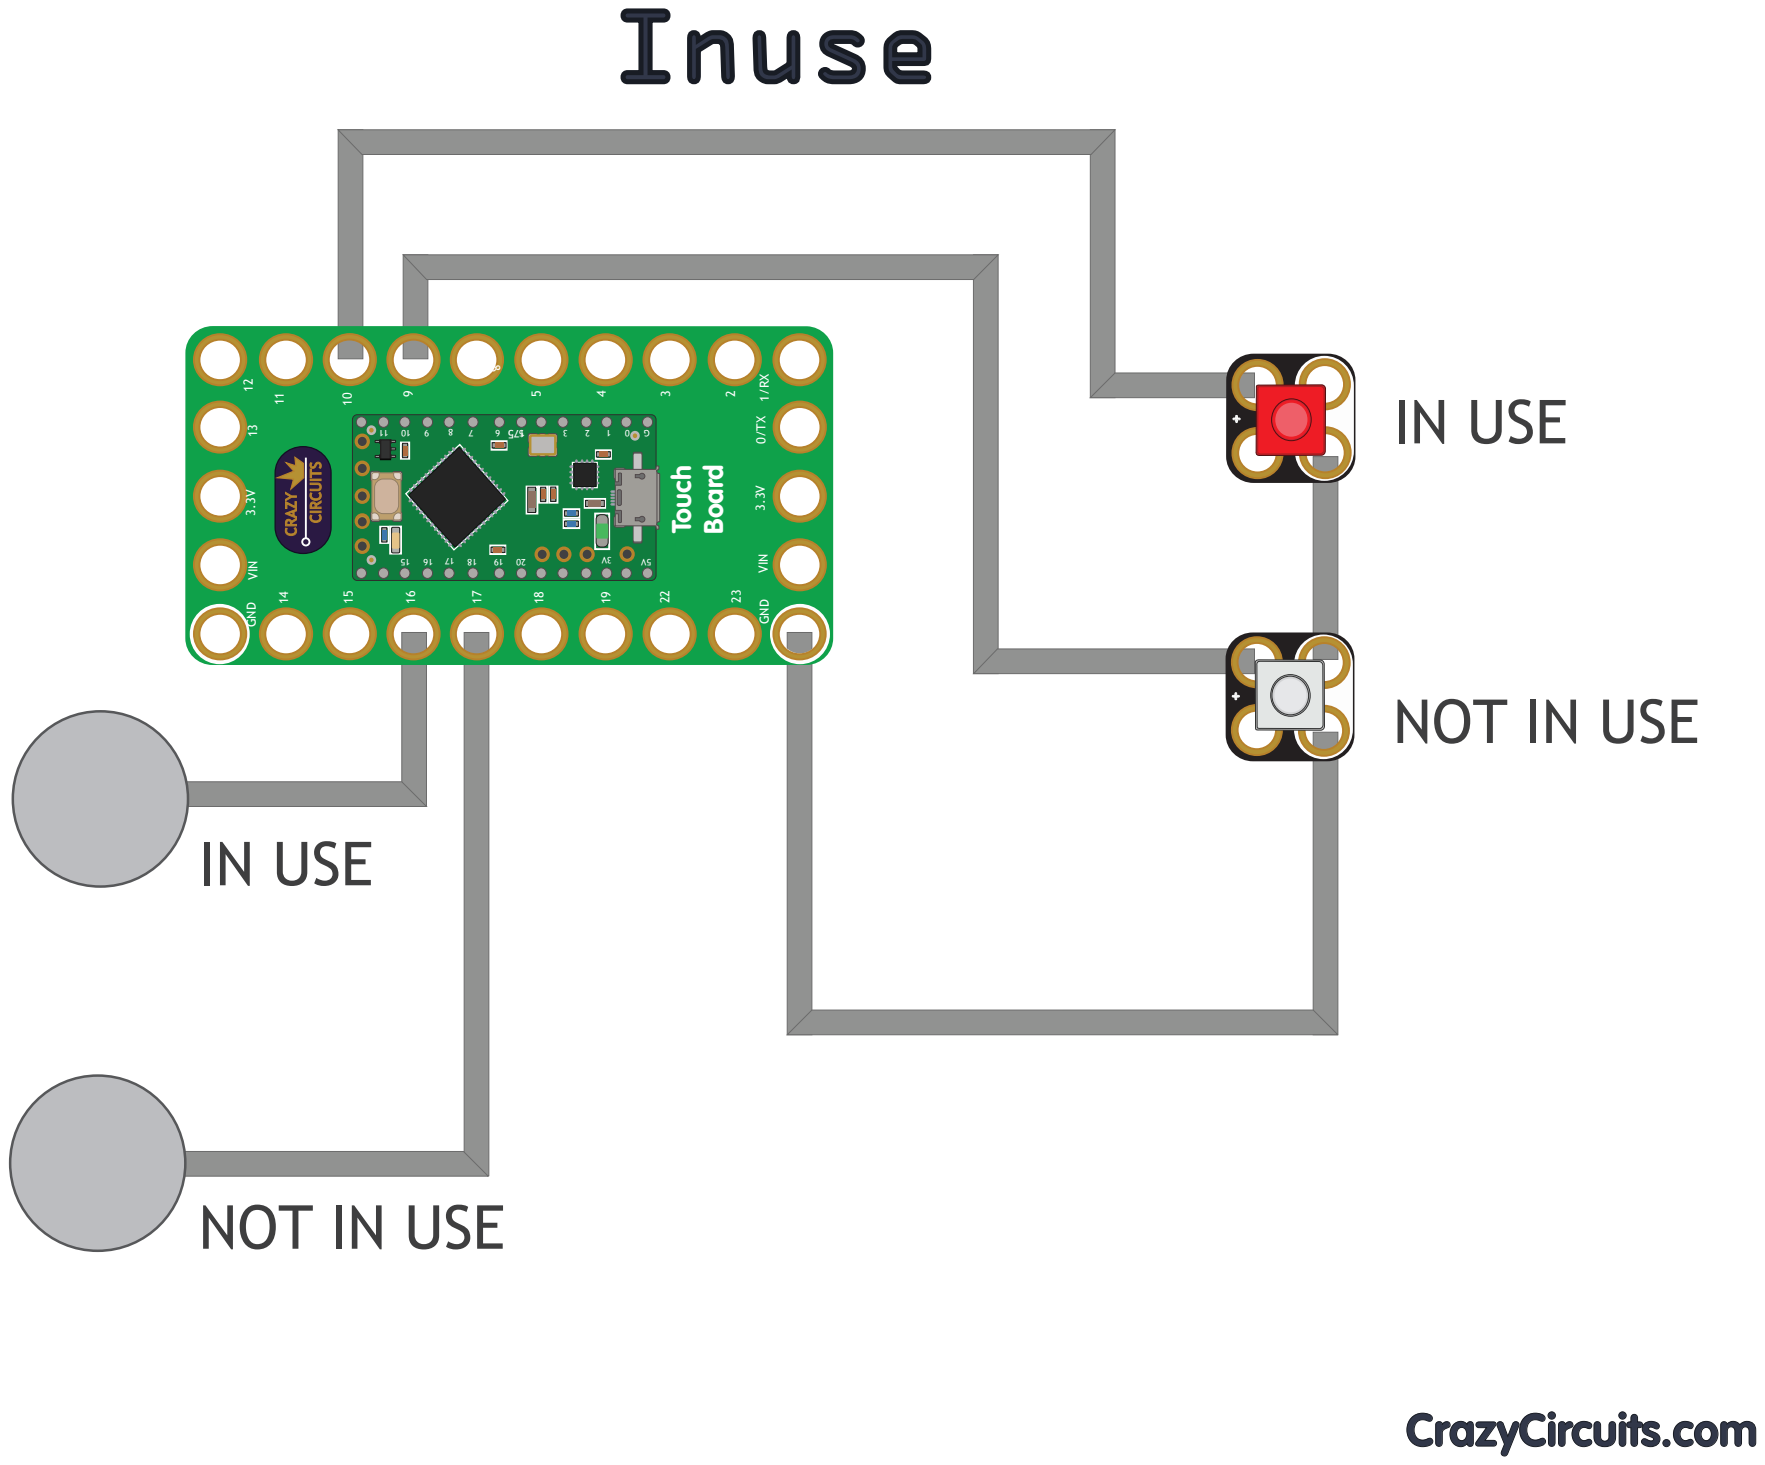
[picture p426: page 1]
IN USE; VIN; 3.3V GND; CRAZY; CIRCUITS; Touch; Board; CrazyCircuits.com

GND 0/TX 1/RX

NOT IN USE ⁺

NOT IN USE
