BrownDogGadgets/CrazyCircuits/Projects/Larson Scanner/Larson Blink Fade Diagram.pdf

# 85 Larson Scanner

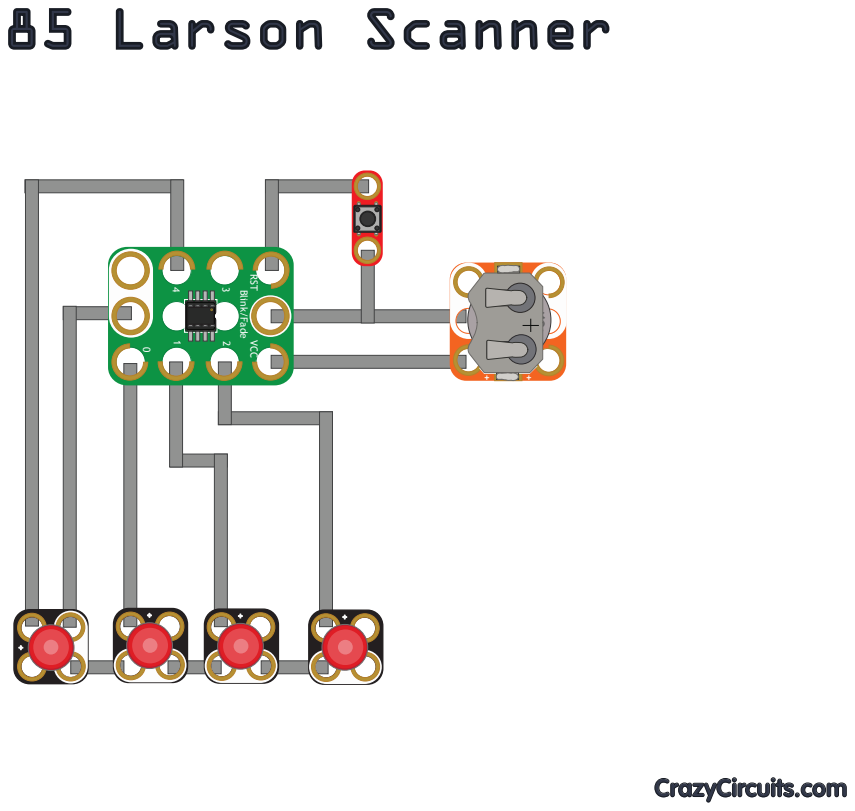
[picture p427: page 1]
+ Battery; BUTTO; CELL CR20232; RST VCC Blink/Fade; CrazyCircuits.com
