BrownDogGadgets/CrazyCircuits/Projects/Blink Fade/LandSpeeder Diagram.pdf

# Land Speed

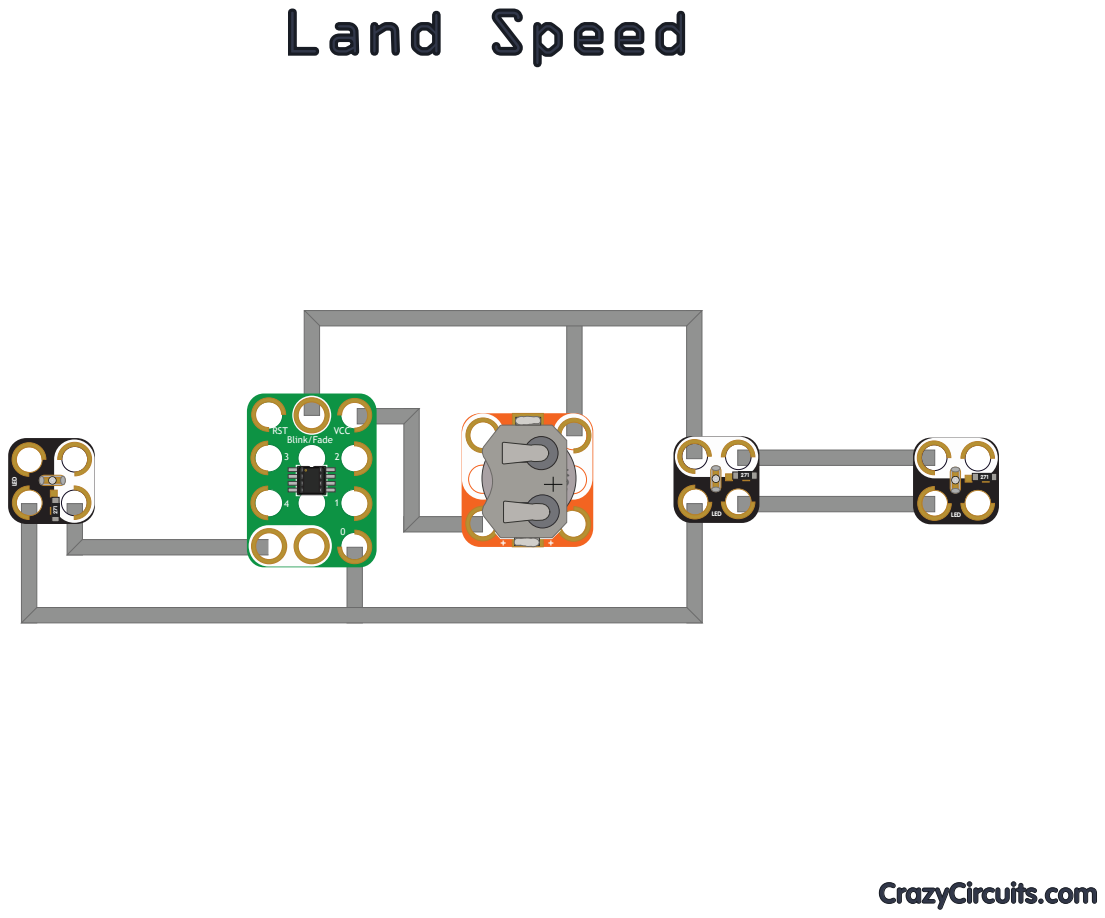
[picture p428: page 1]
+ Battery; BUTTO; CELL CR20232; RST; VCC; Blink/Fade; LED; CrazyCircuits.com
