BrownDogGadgets/CrazyCircuits/Projects/Blink Fade/Parallel Fade Diagram.pdf

# Double LED

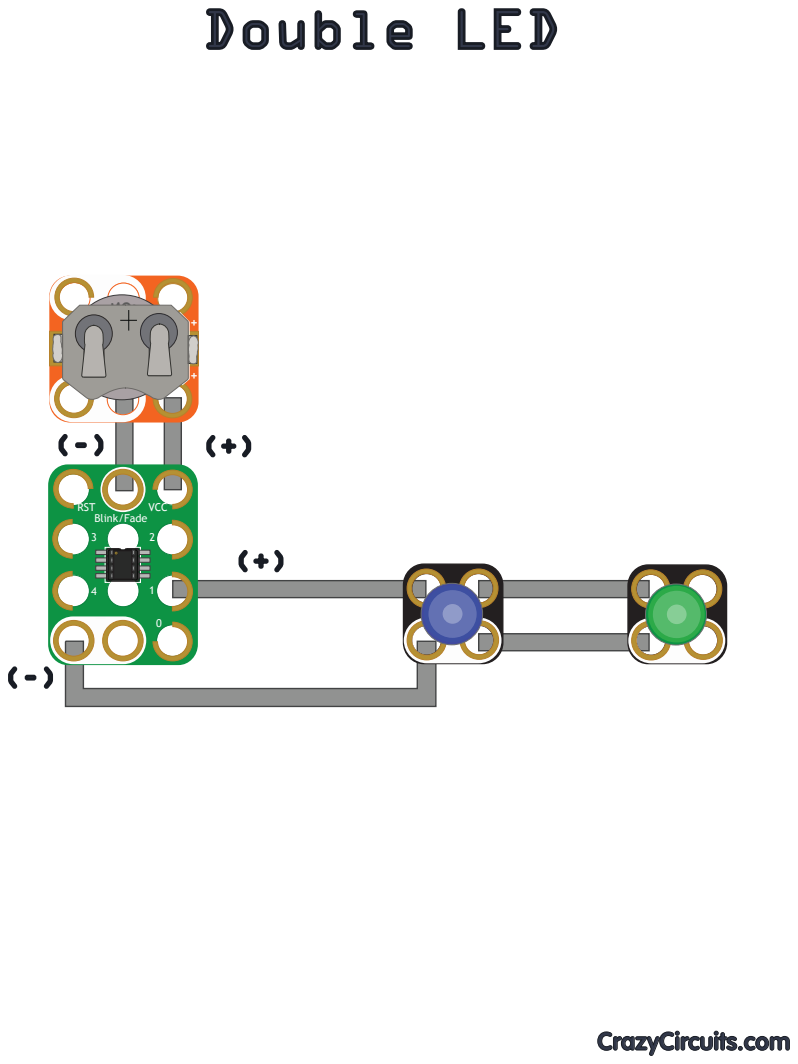
[picture p429: page 1]
RST; VCC; Blink/Fade; Battery; CrazyCircuits.com
