BrownDogGadgets/CrazyCircuits/Projects/Adjustable Lamp/Triangle Shade Template.pdf

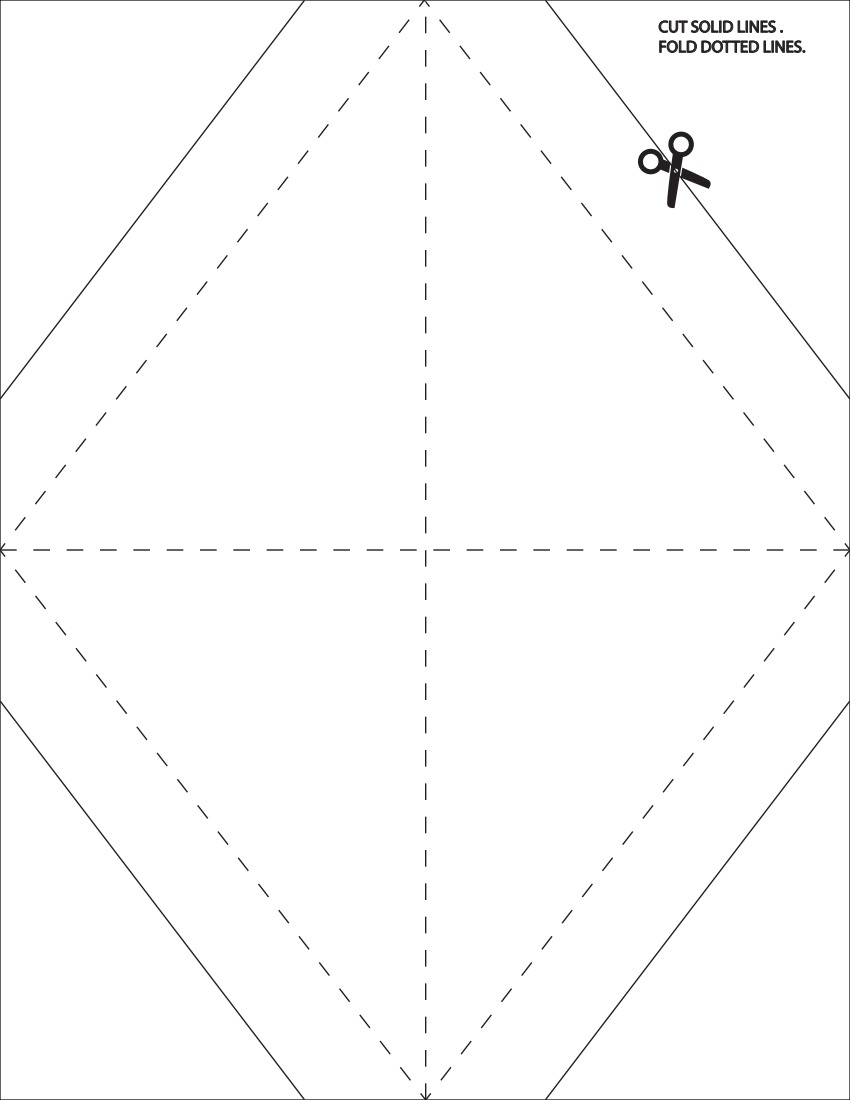
[picture p430: page 1]

CUT SOLID LINES .
FOLD DOTTED LINES.
