BrownDogGadgets/CrazyCircuits/Projects/Game of Simon/Simon Touch Board Diagram.pdf

# Simon Touch

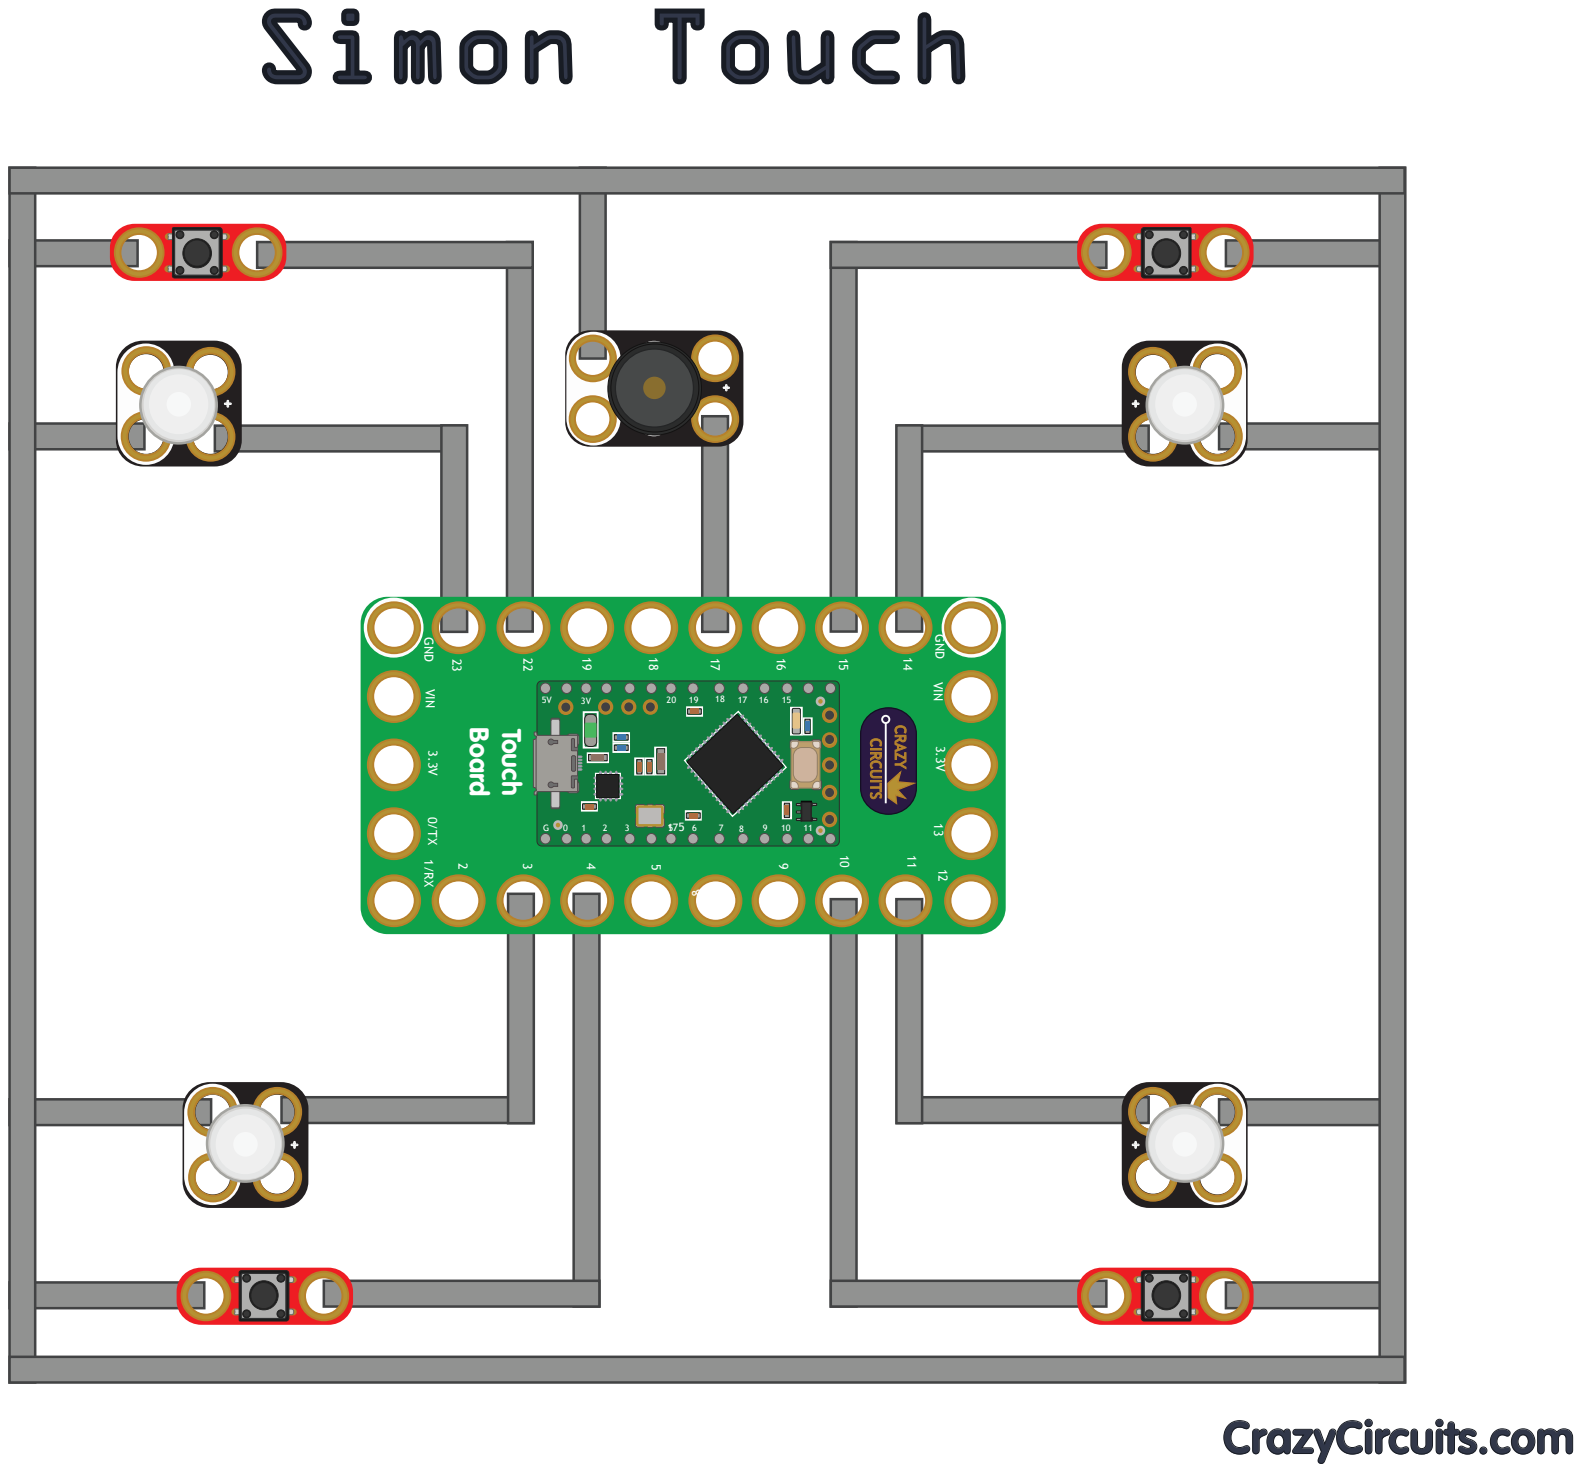
[picture p431: page 1]
VIN; GND; CRAZY; CIRCUITS; Board Touch; CrazyCircuits.com
