BrownDogGadgets/CrazyCircuits/Projects/Adjustable Lamp/Adjustable Lamp Diagram.pdf

# Brick Sample

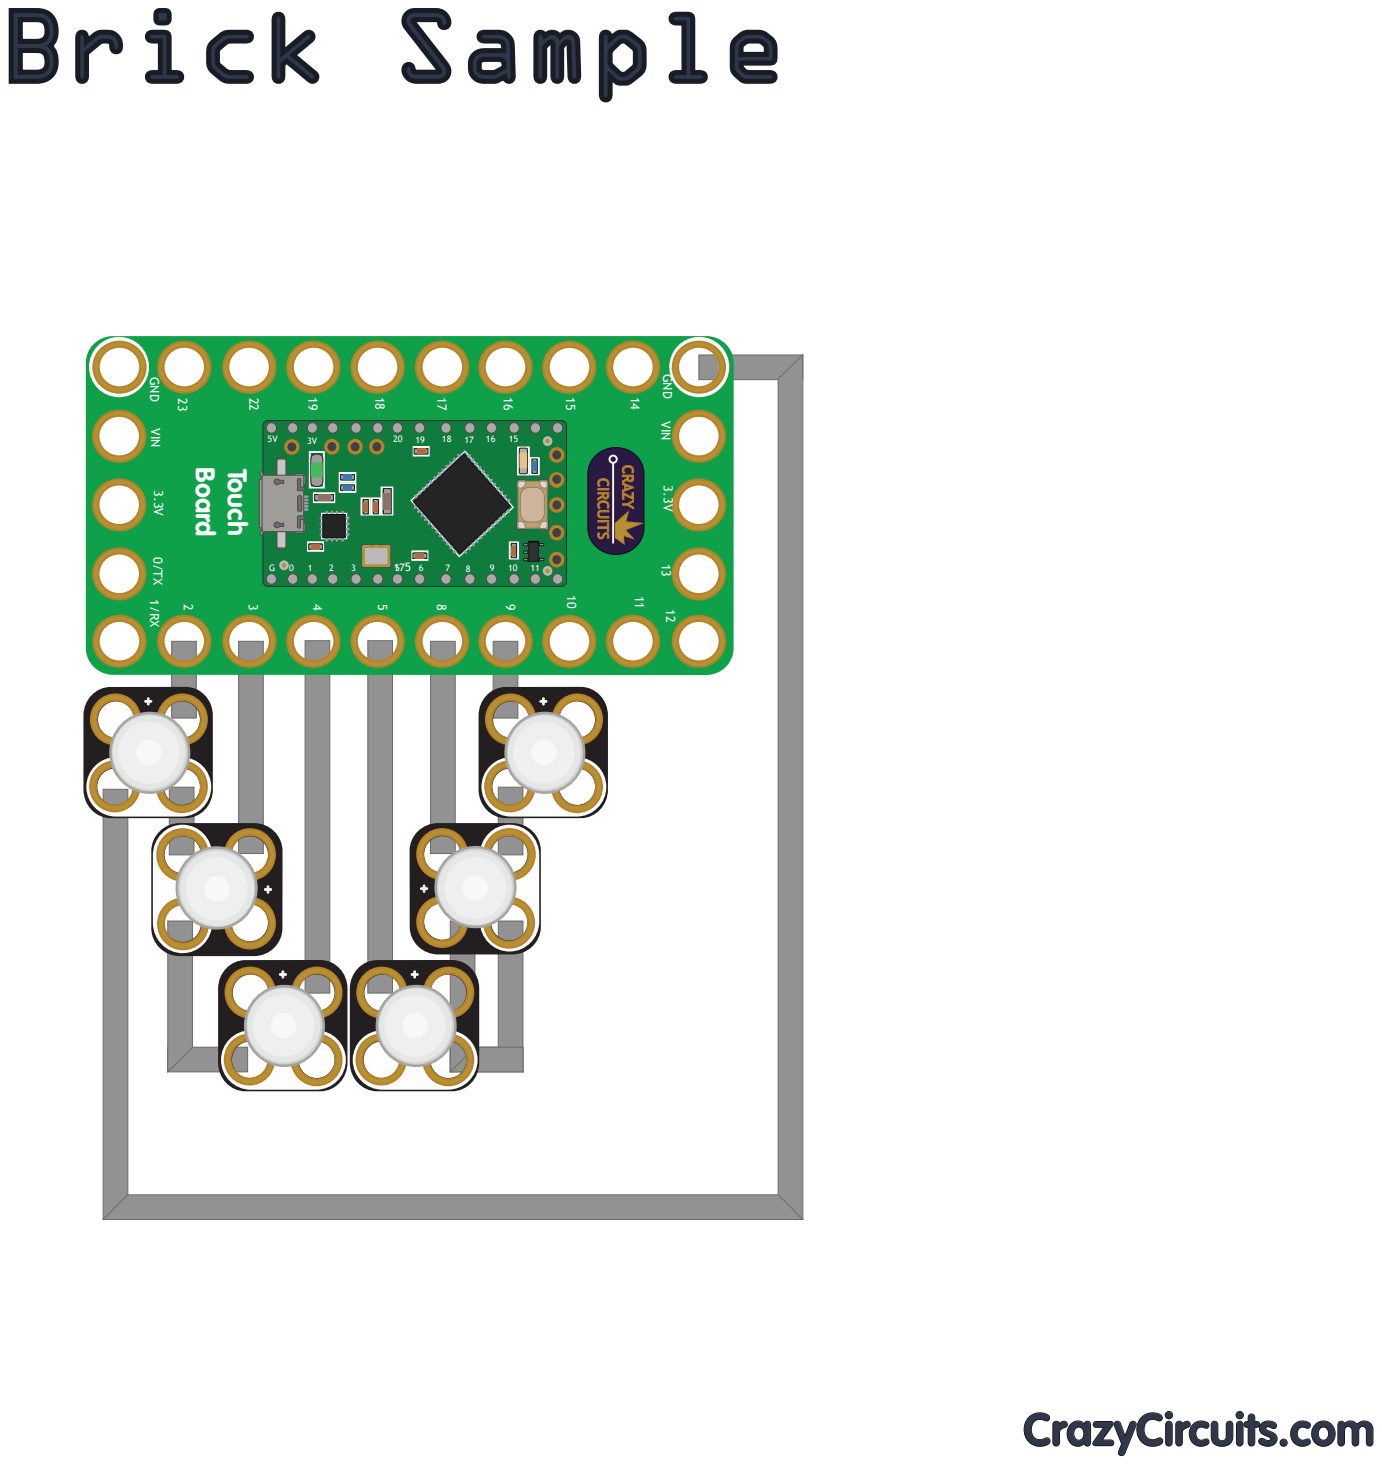
[picture p432: page 1]
VIN; GND; CRAZY; CIRCUITS; Board Touch; CrazyCircuits.com
