BrownDogGadgets/CrazyCircuits/Projects/Adjustable Lamp/Adjustable Lamp Dial 1.pdf

# Pint dial 1

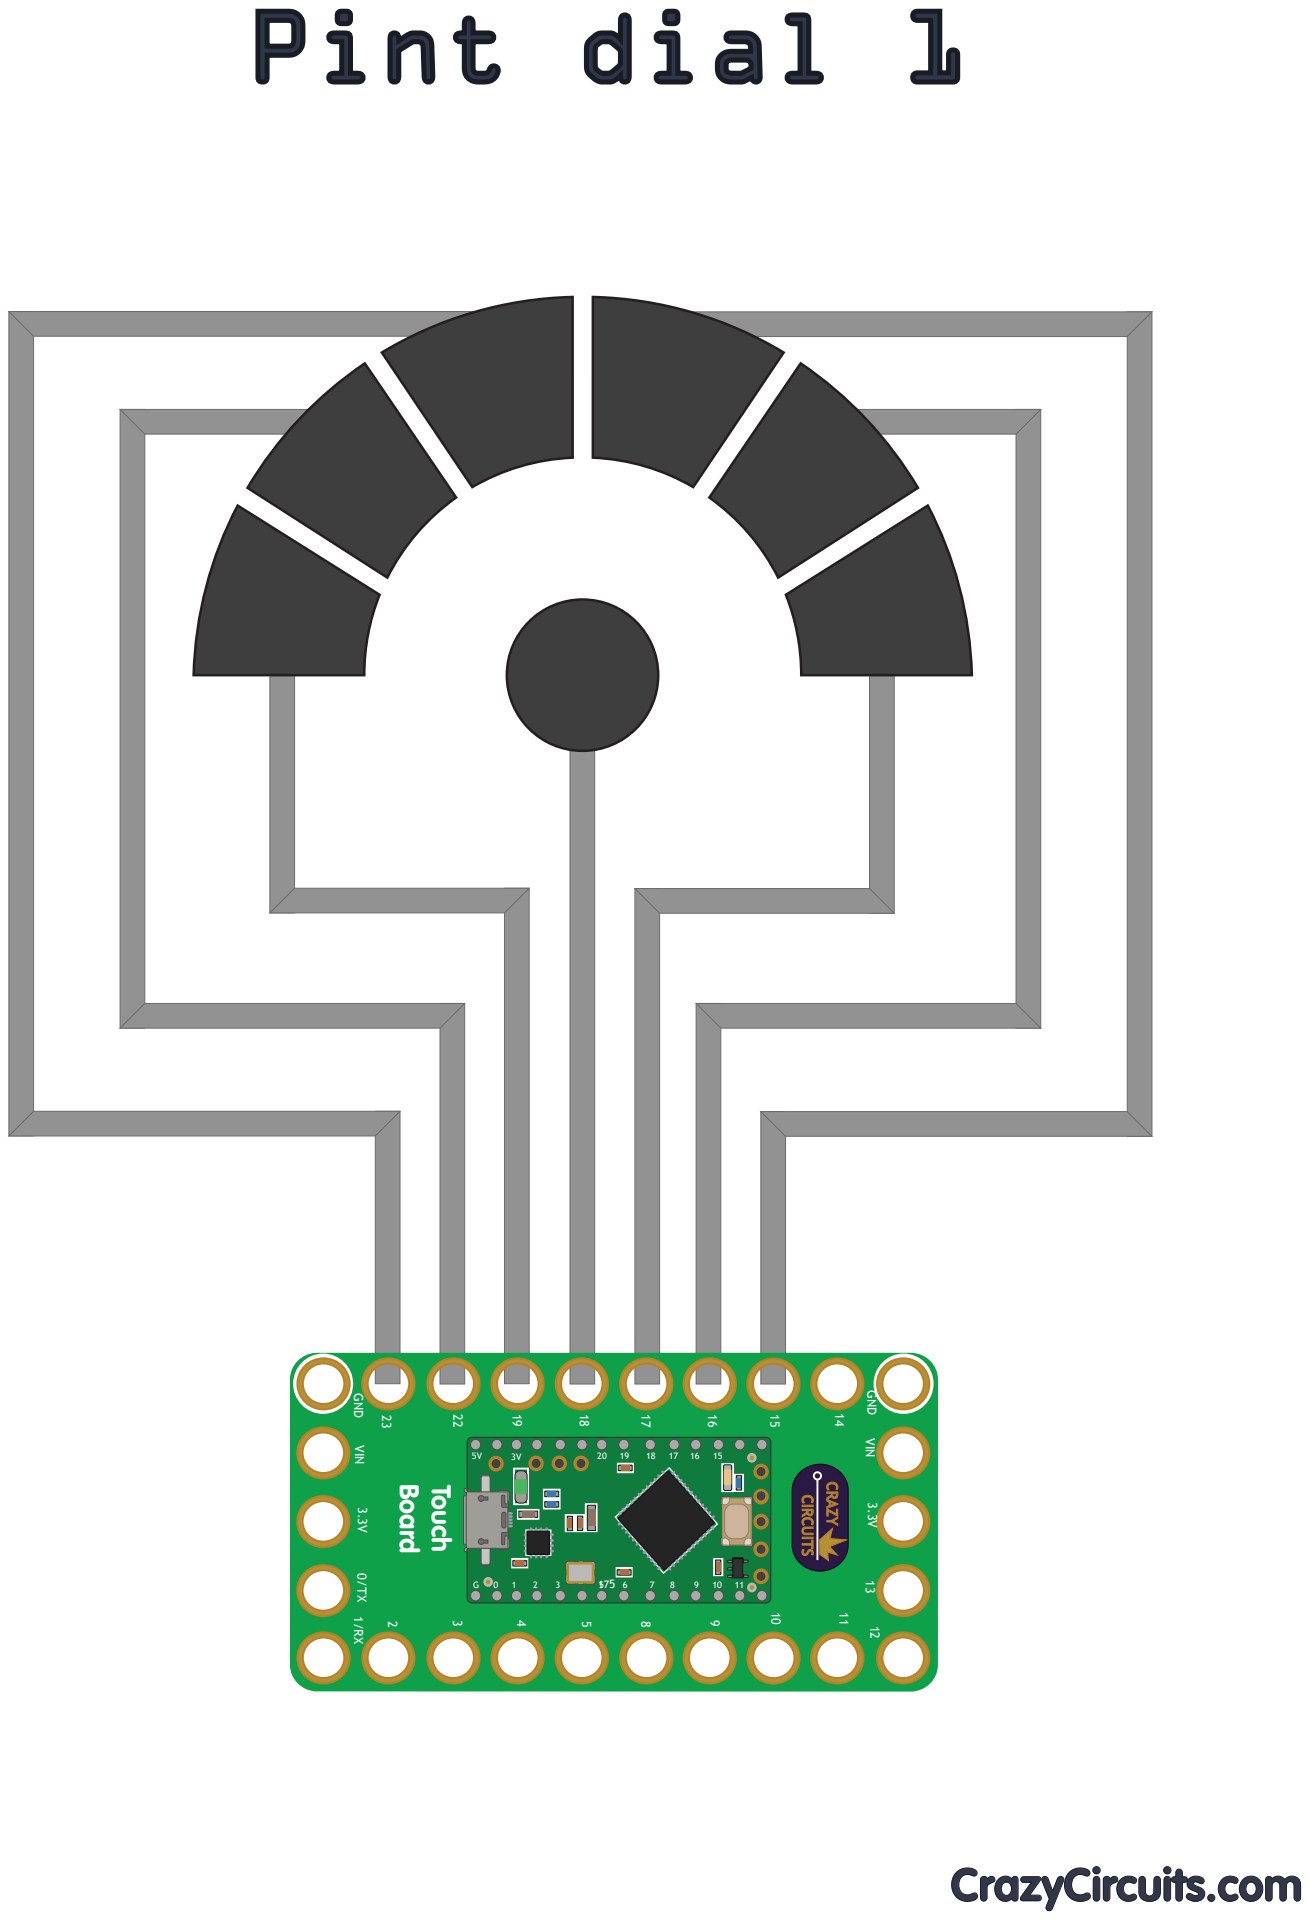
[picture p433: page 1]
VIN; GND; CRAZY; CIRCUITS; Board Touch; CrazyCircuits.com
