BrownDogGadgets/CrazyCircuits/Projects/Adjustable Lamp/Adjustable Lamp Dial 2.pdf

# Paint Dial 2

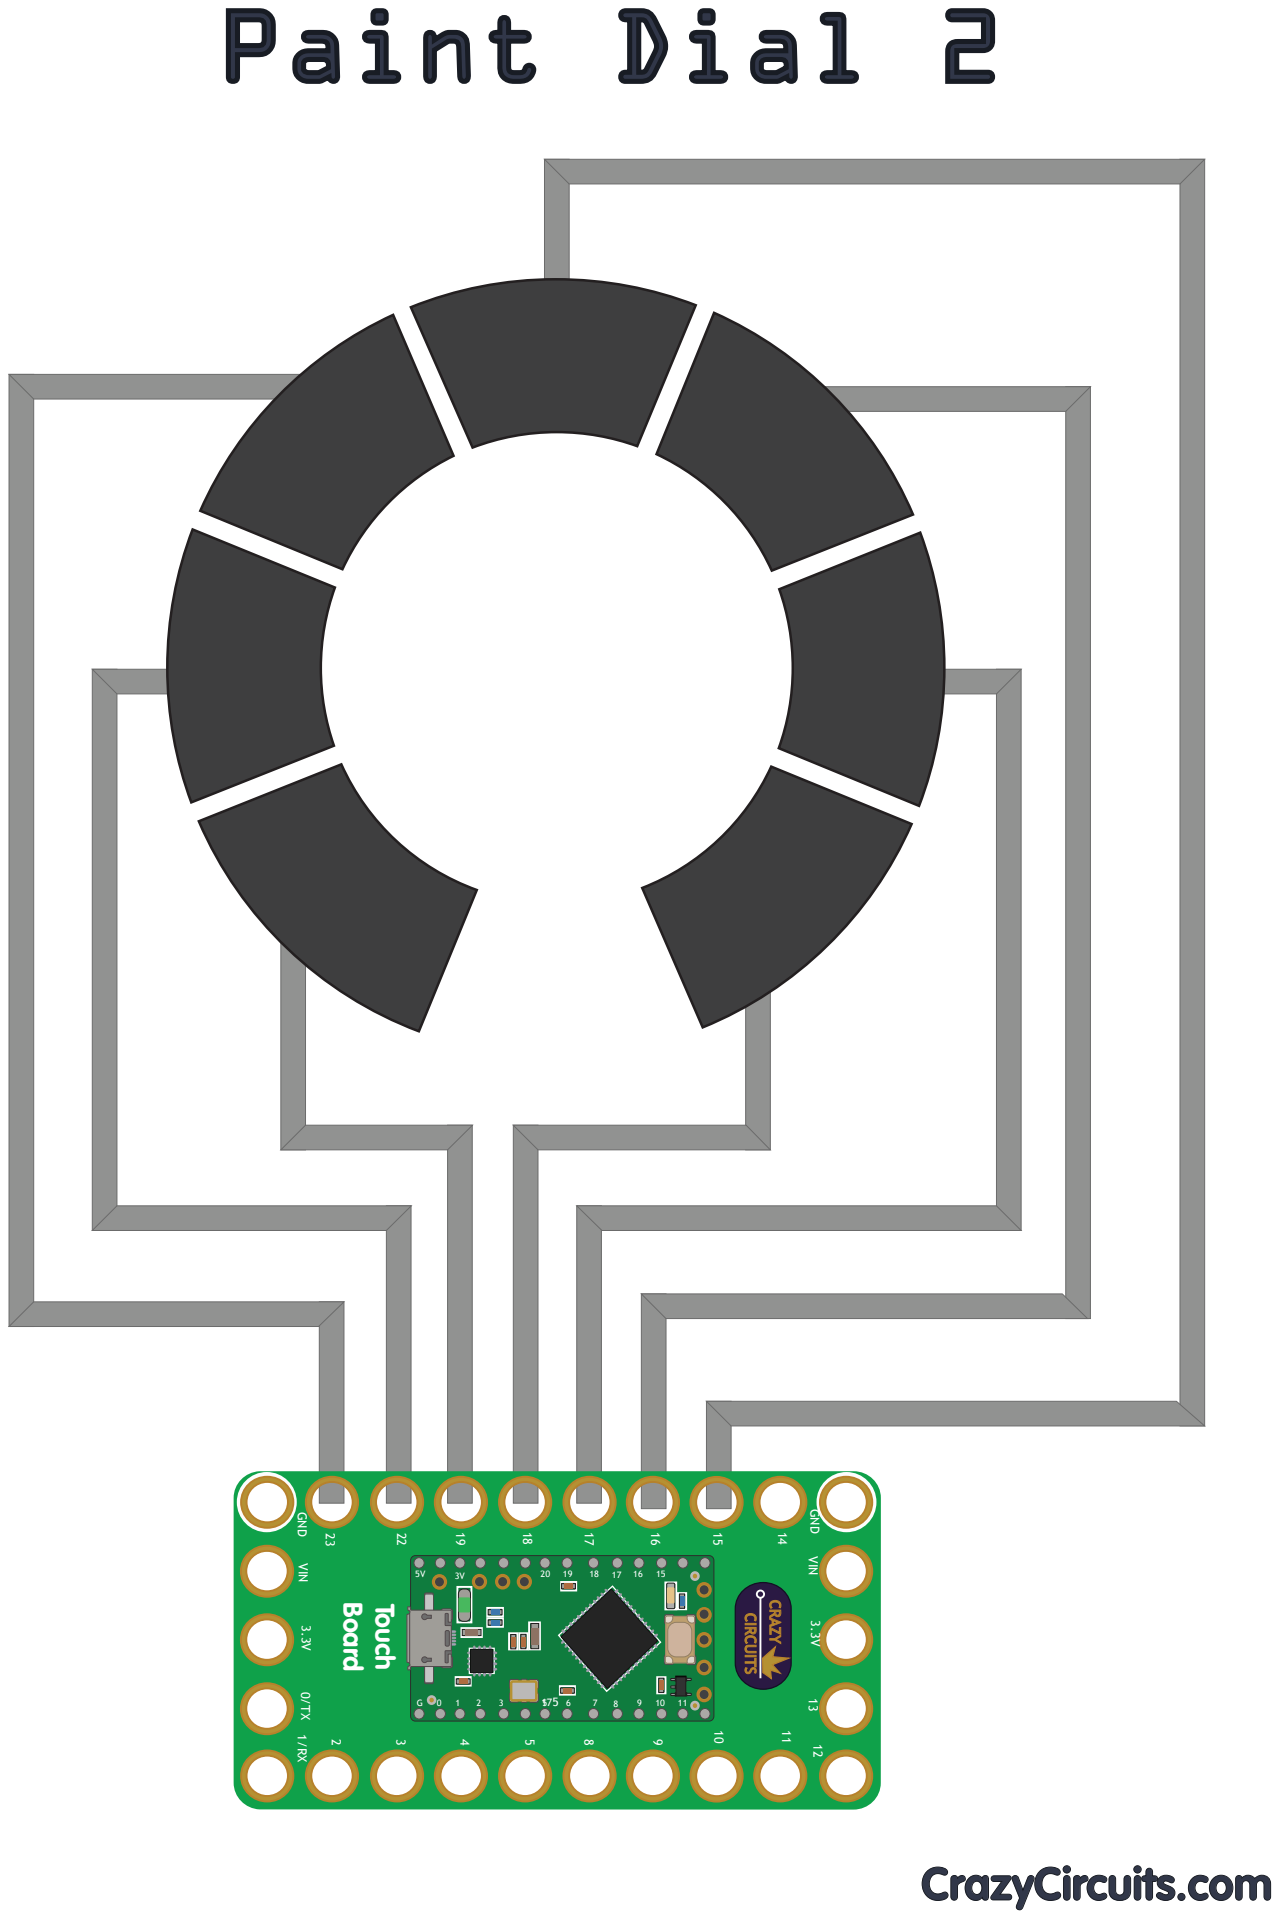
[picture p434: page 1]
VIN; GND; CRAZY; CIRCUITS; Board Touch; CrazyCircuits.com
