BrownDogGadgets/CrazyCircuits/Projects/Adjustable Lamp/Adjustable Lamp Dial 3.pdf

# Conuctive Dial 3

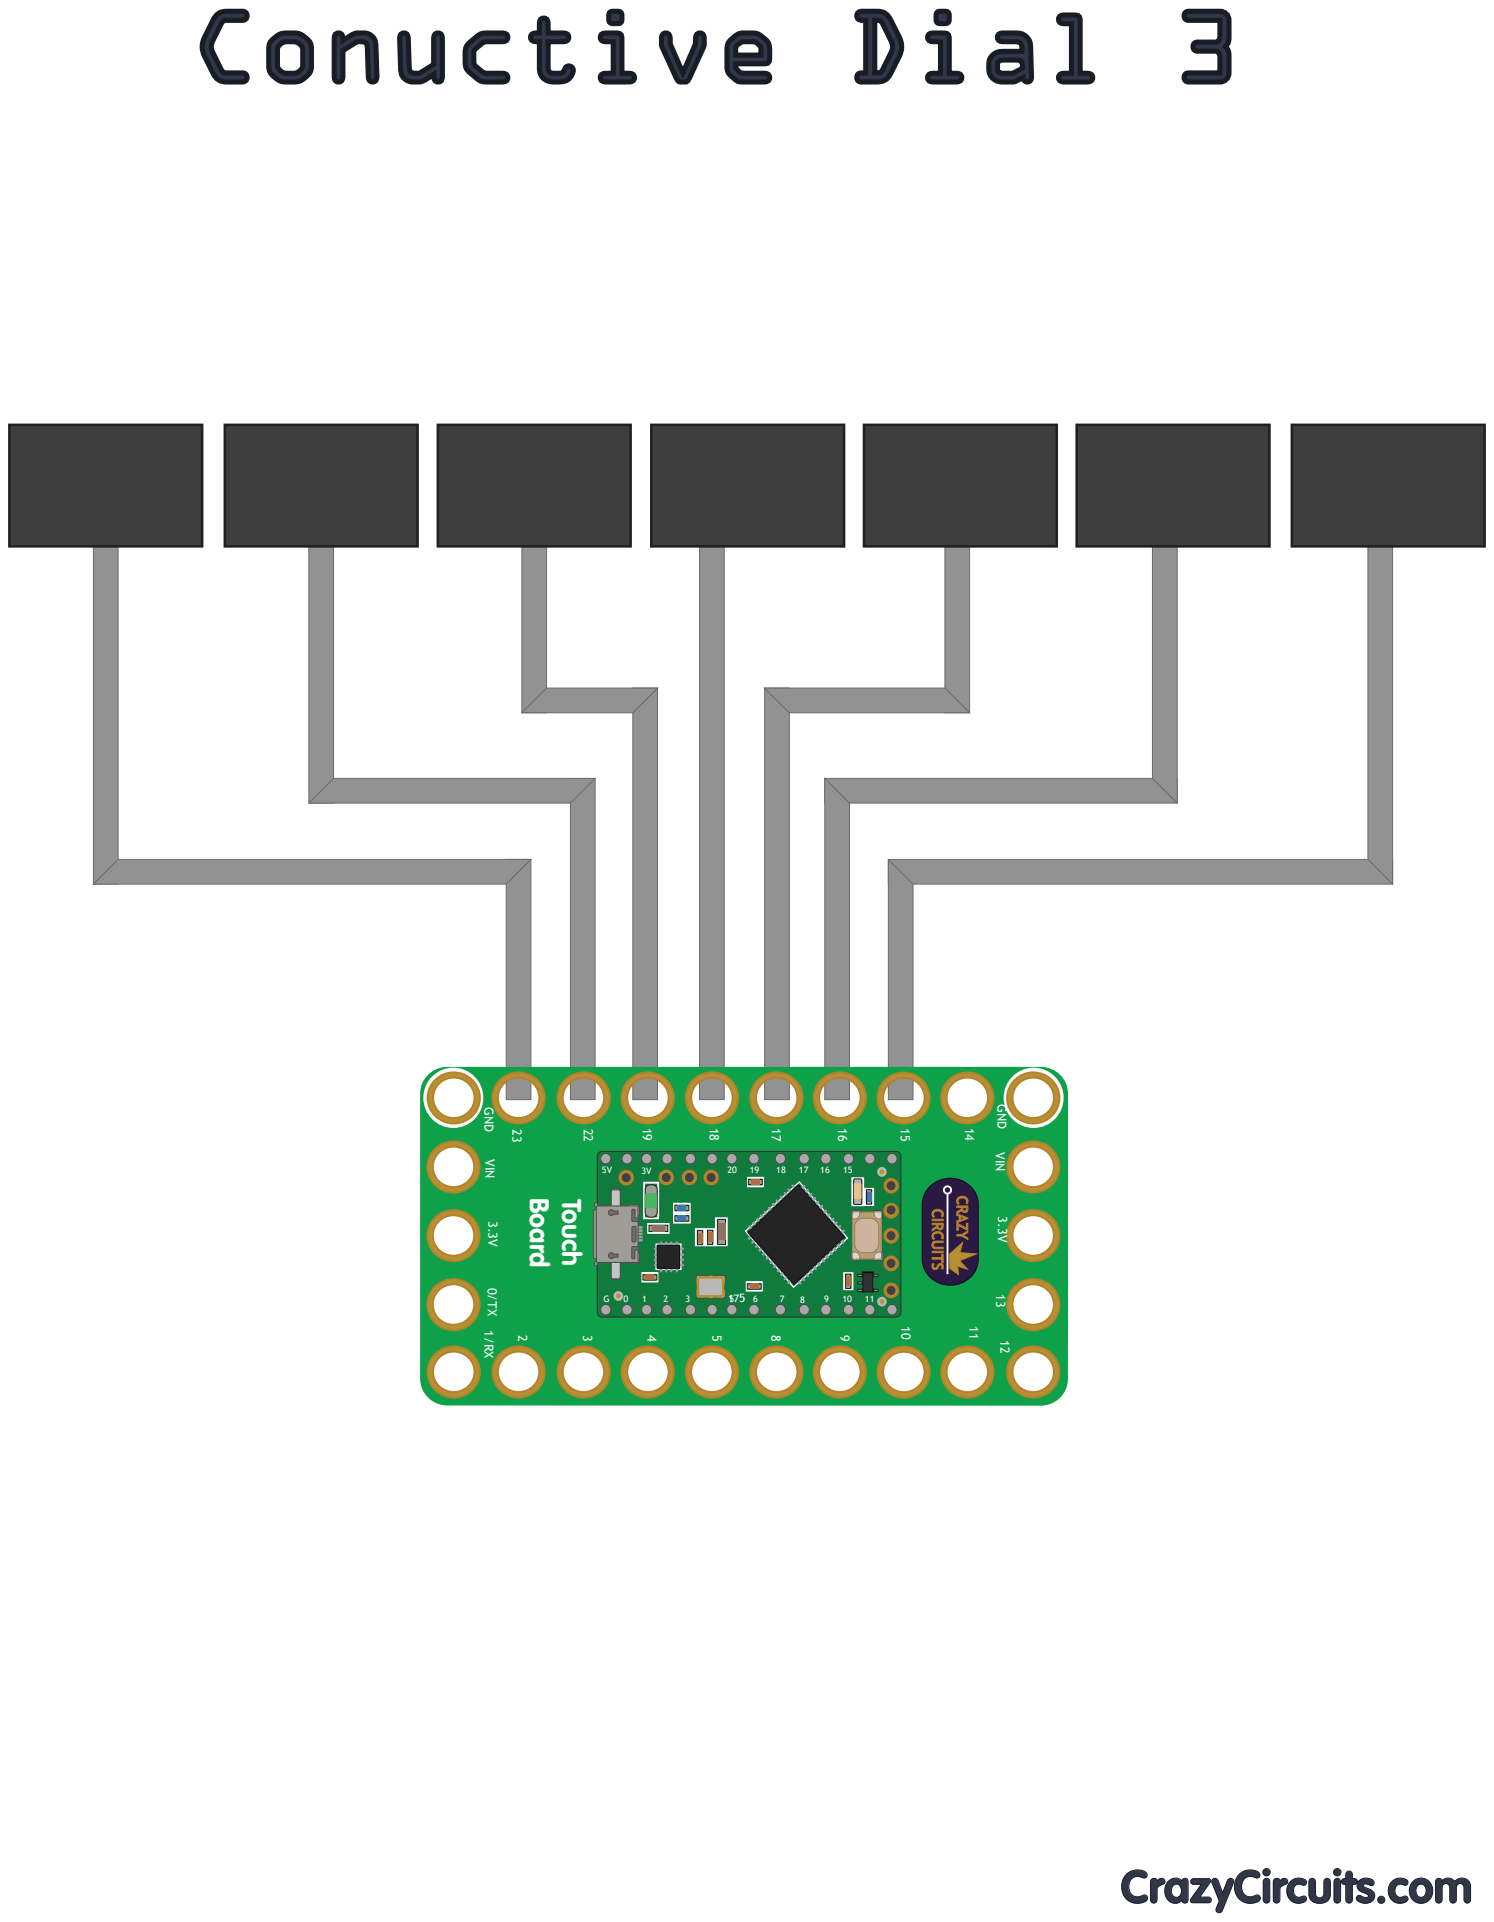
[picture p435: page 1]
VIN; GND; CRAZY; CIRCUITS; Board Touch; CrazyCircuits.com
