BrownDogGadgets/CrazyCircuits/Projects/Adjustable Lamp/Adjustable Lamp Dial Stencil.pdf

# DIAL 1

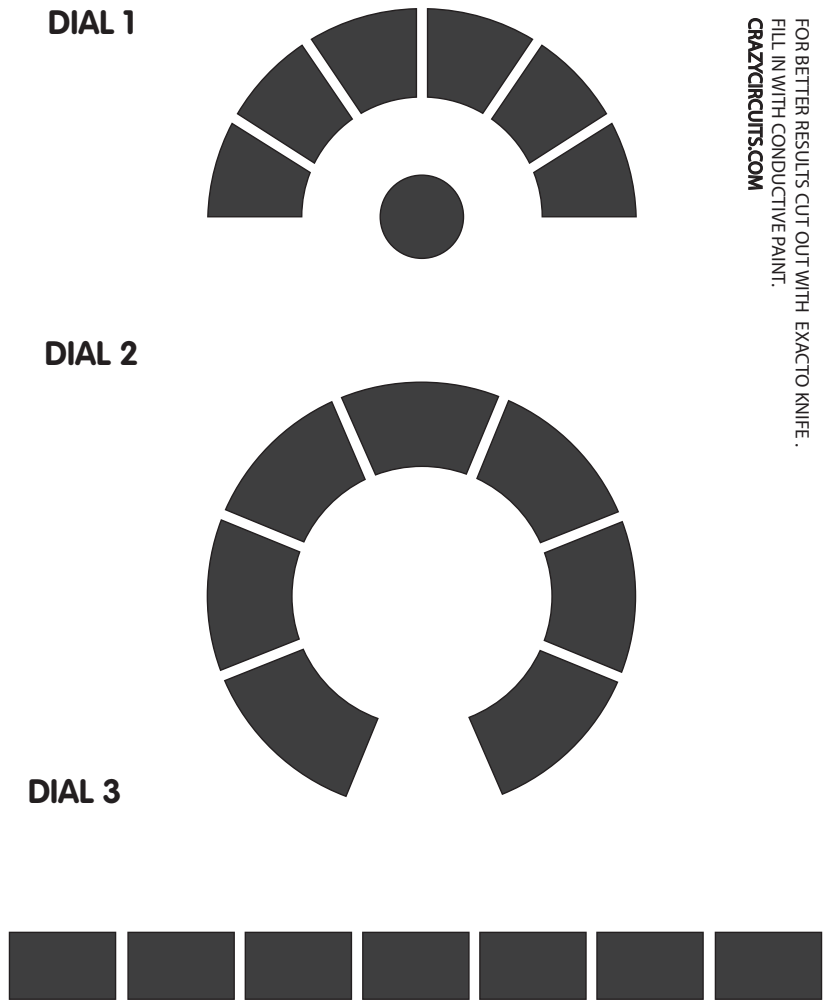
[picture p436: page 1]
DIAL 3; DIAL 2; CRAZYCIRCUITS.COM

FILL IN WITH CONDUCTIVE PAINT.

FOR BETTER RESULTS CUT OUT WITH EXACTO KNIFE .
