BrownDogGadgets/CrazyCircuits/User Guides/Part Mini Guides/Female Header.pdf

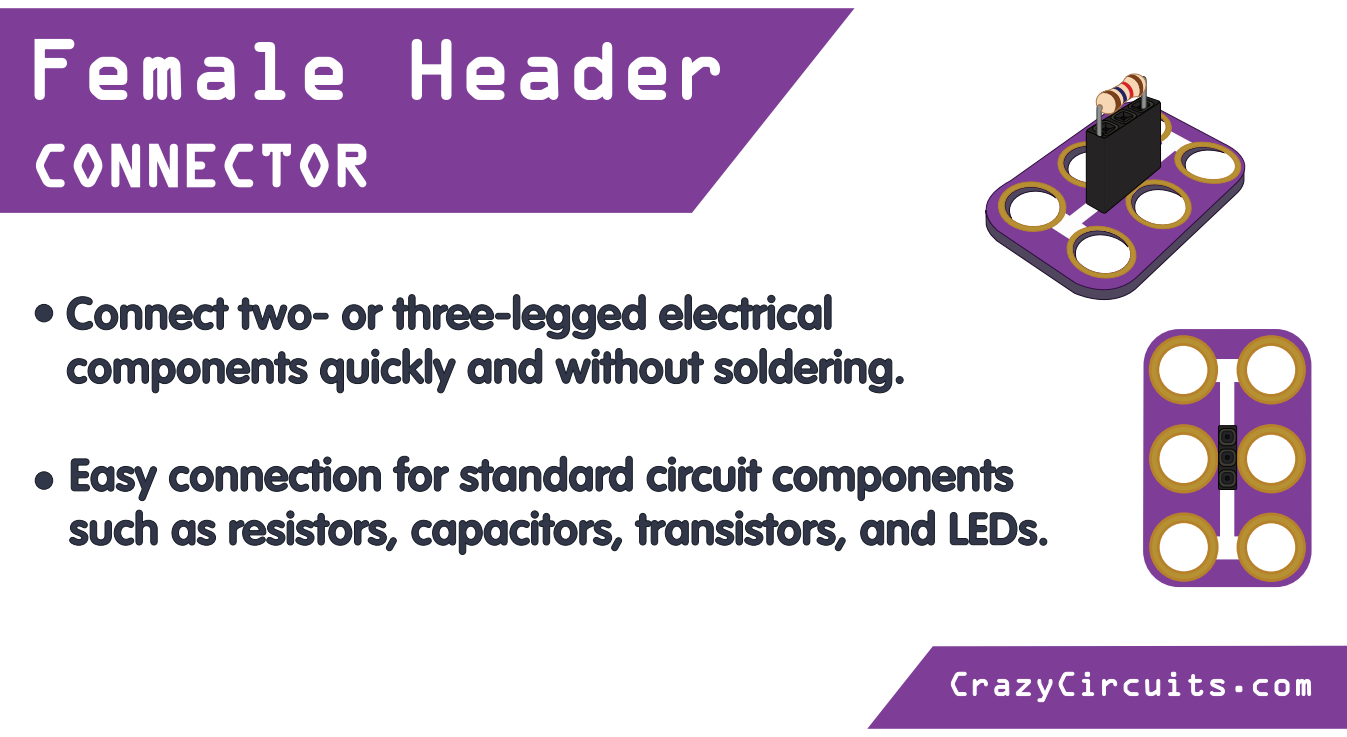
[picture p447: page 1]

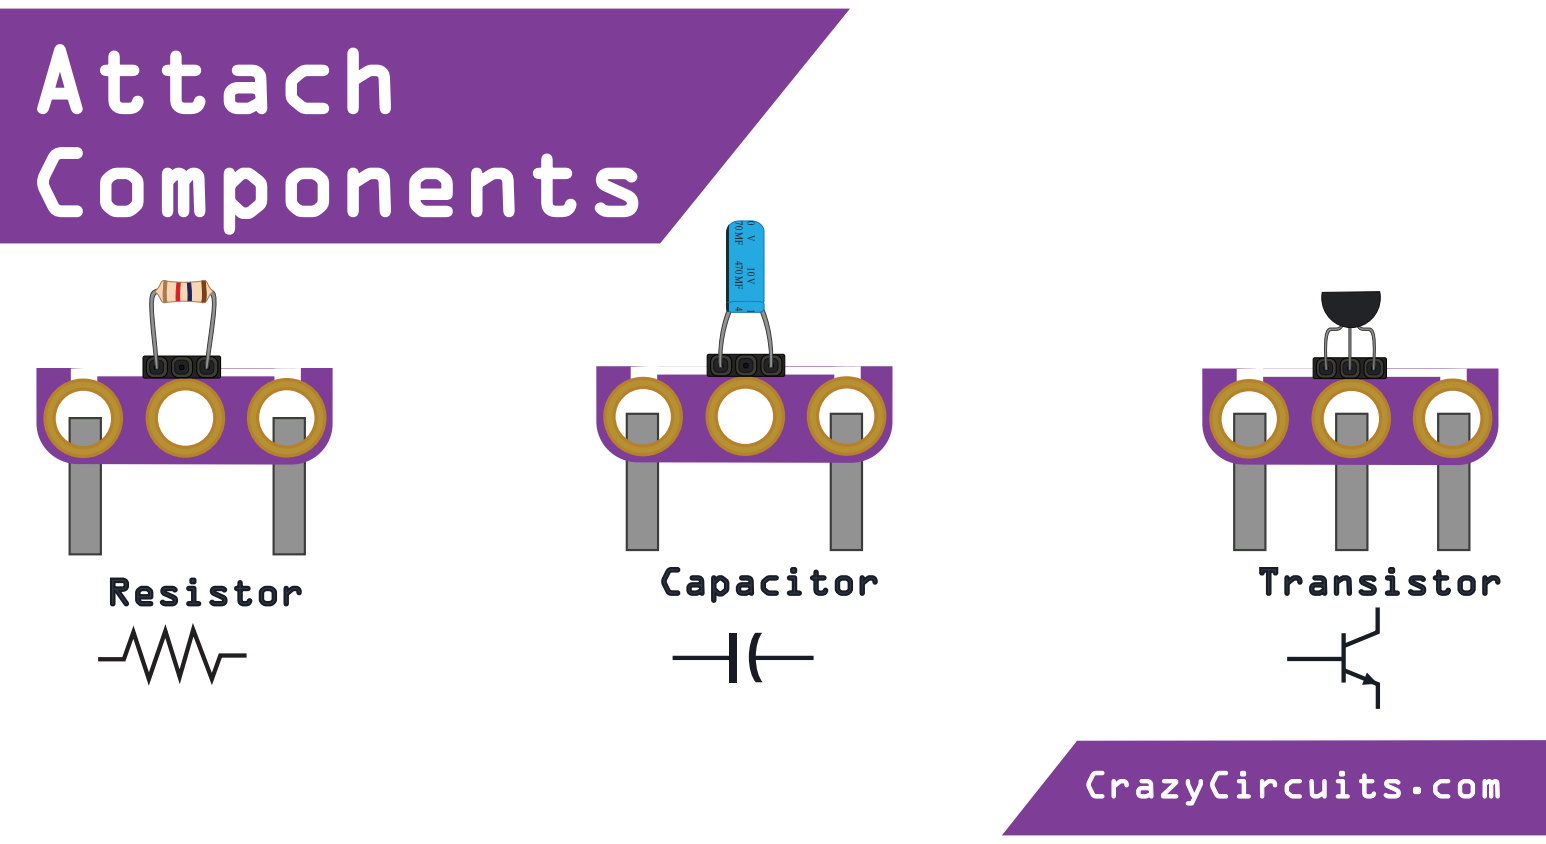
[picture p448: page 2]
CrazyCircuits.com
