BrownDogGadgets/CrazyCircuits/User Guides/Part Mini Guides/RGB LED.pdf

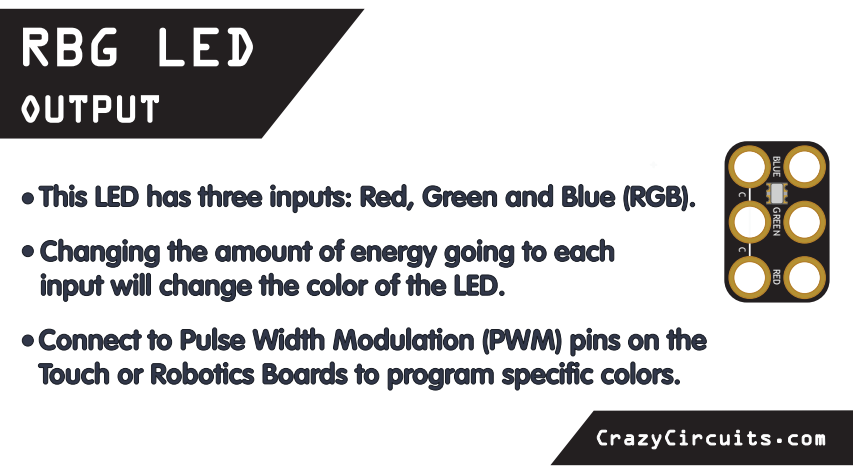
[picture p449: page 1]

BLUE GREEN RED

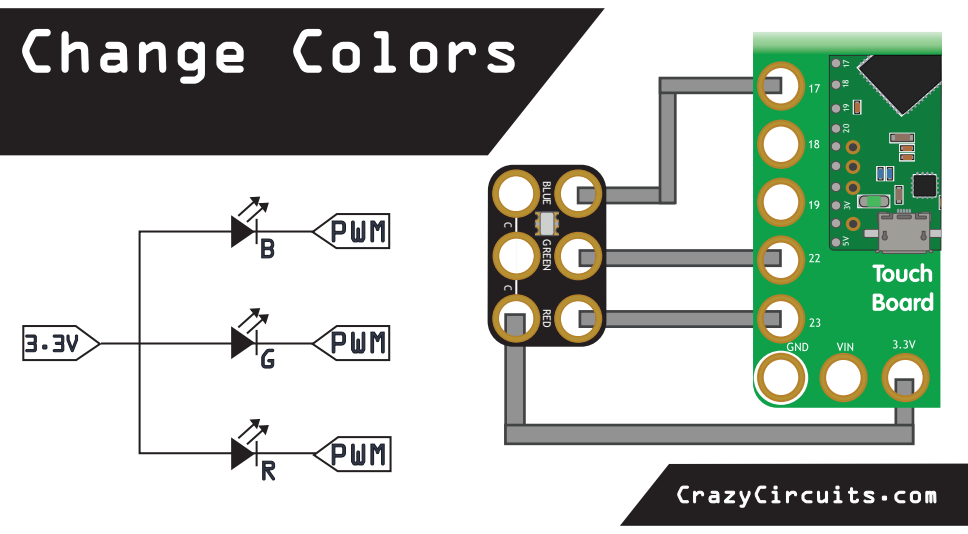
[picture p450: page 2]

BLUE GREEN RED
