BrownDogGadgets/CrazyCircuits/User Guides/Part Mini Guides/Touch and Robotics Boards.pdf

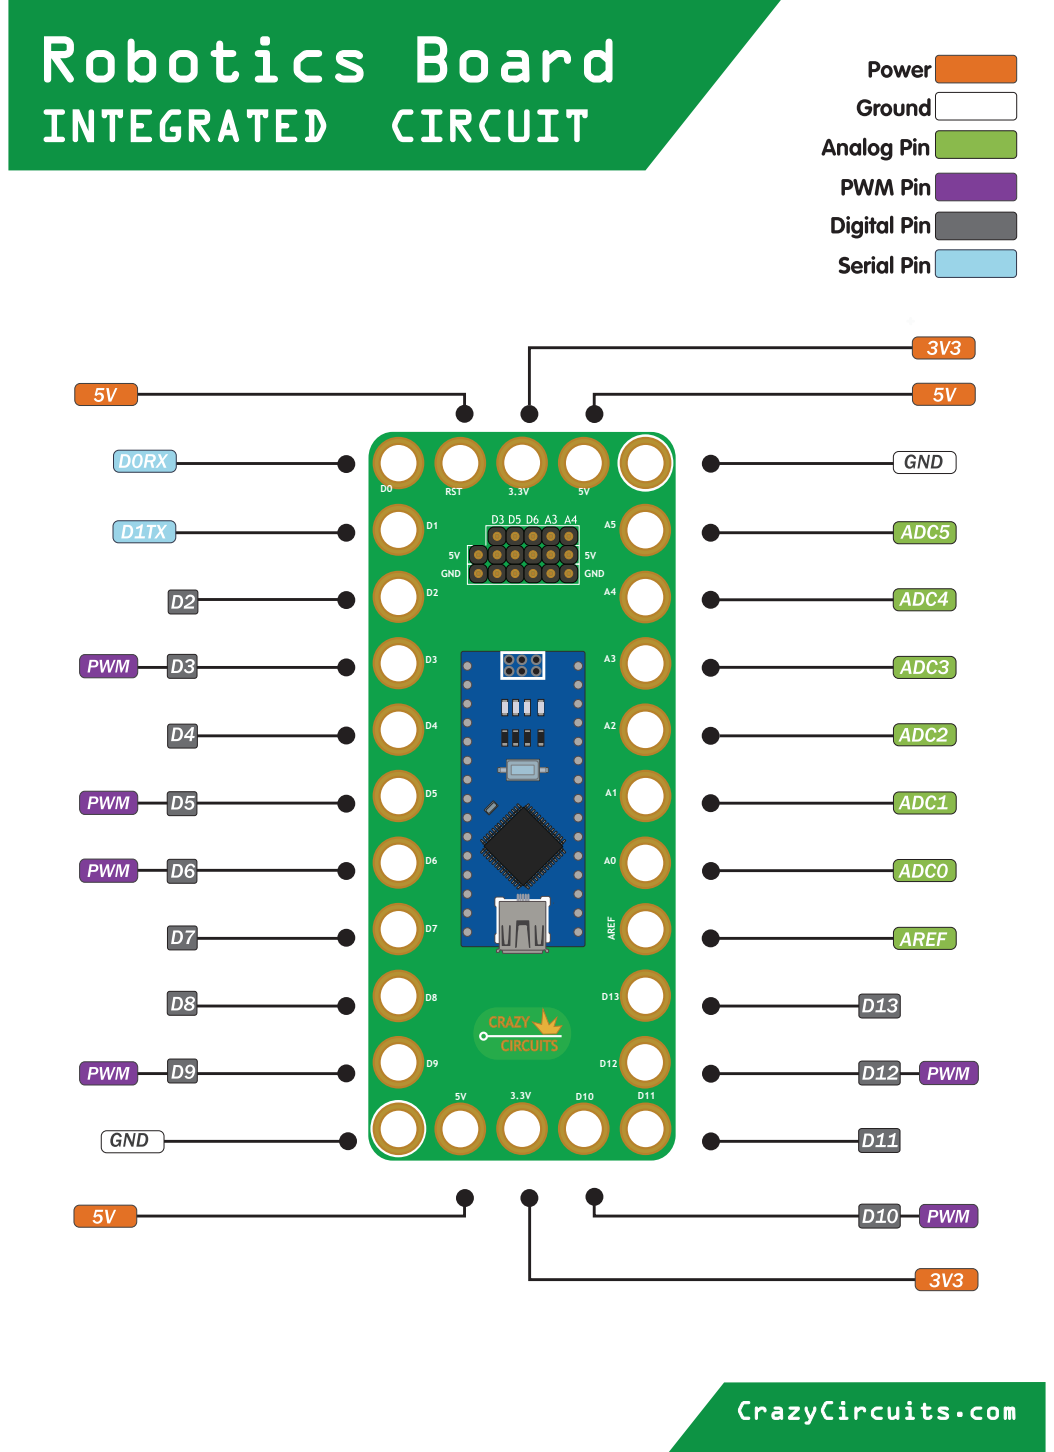
[picture p451: page 1]

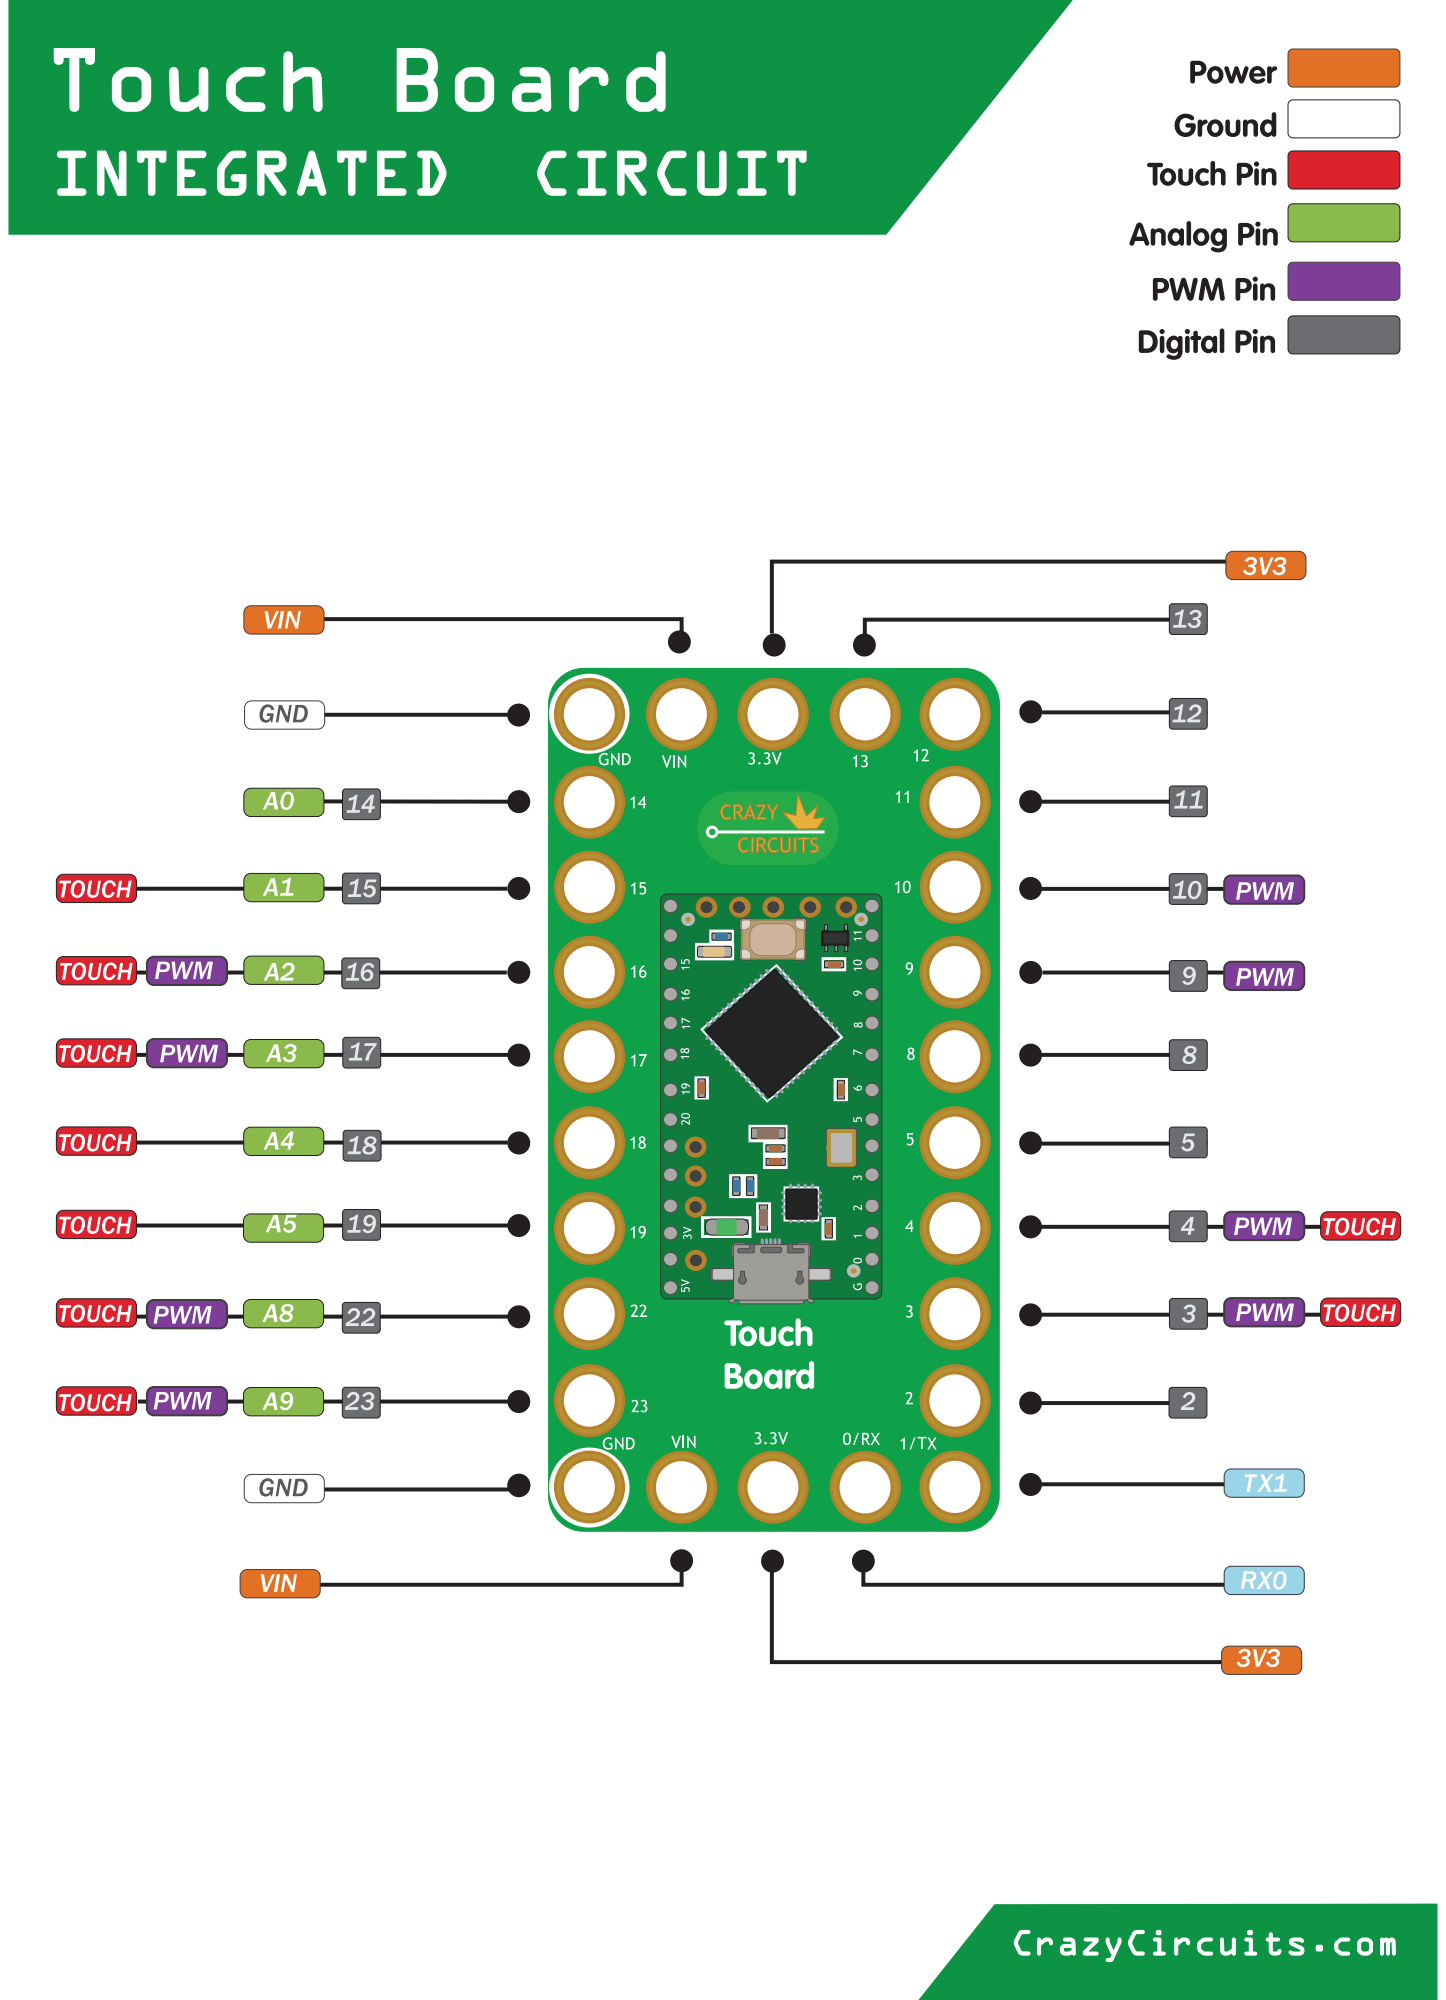
[picture p452: page 2]
