BrownDogGadgets/CrazyCircuits/Projects/LEGO Hole Punch/Paper Printer/BDG LEGO Hole Punch Printout.pdf

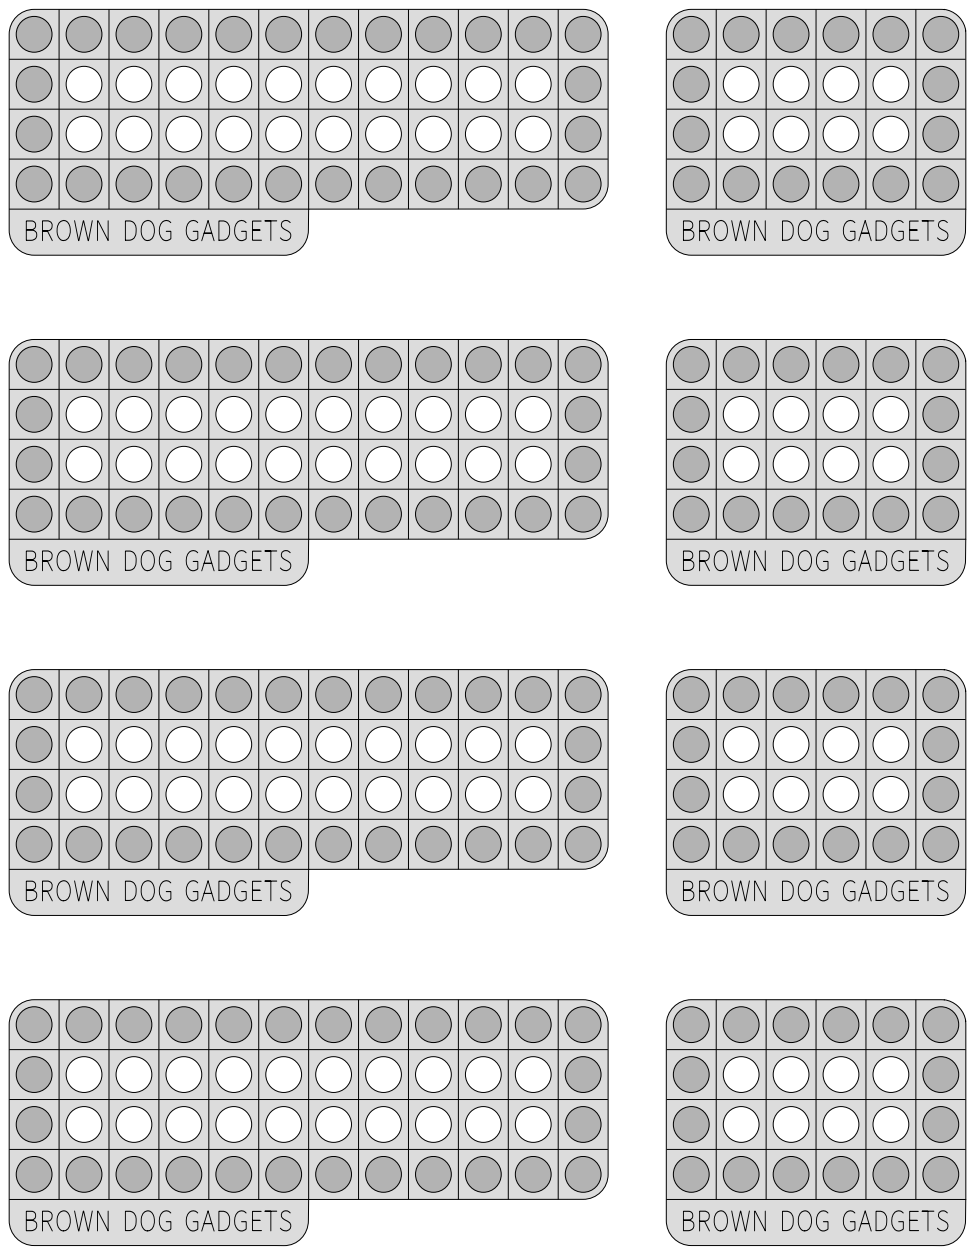
[picture p453: page 1]
