BrownDogGadgets/CrazyCircuits/Projects/Step Sequencer/Diagrams/Step Sequencer.pdf

# Step Sequencer

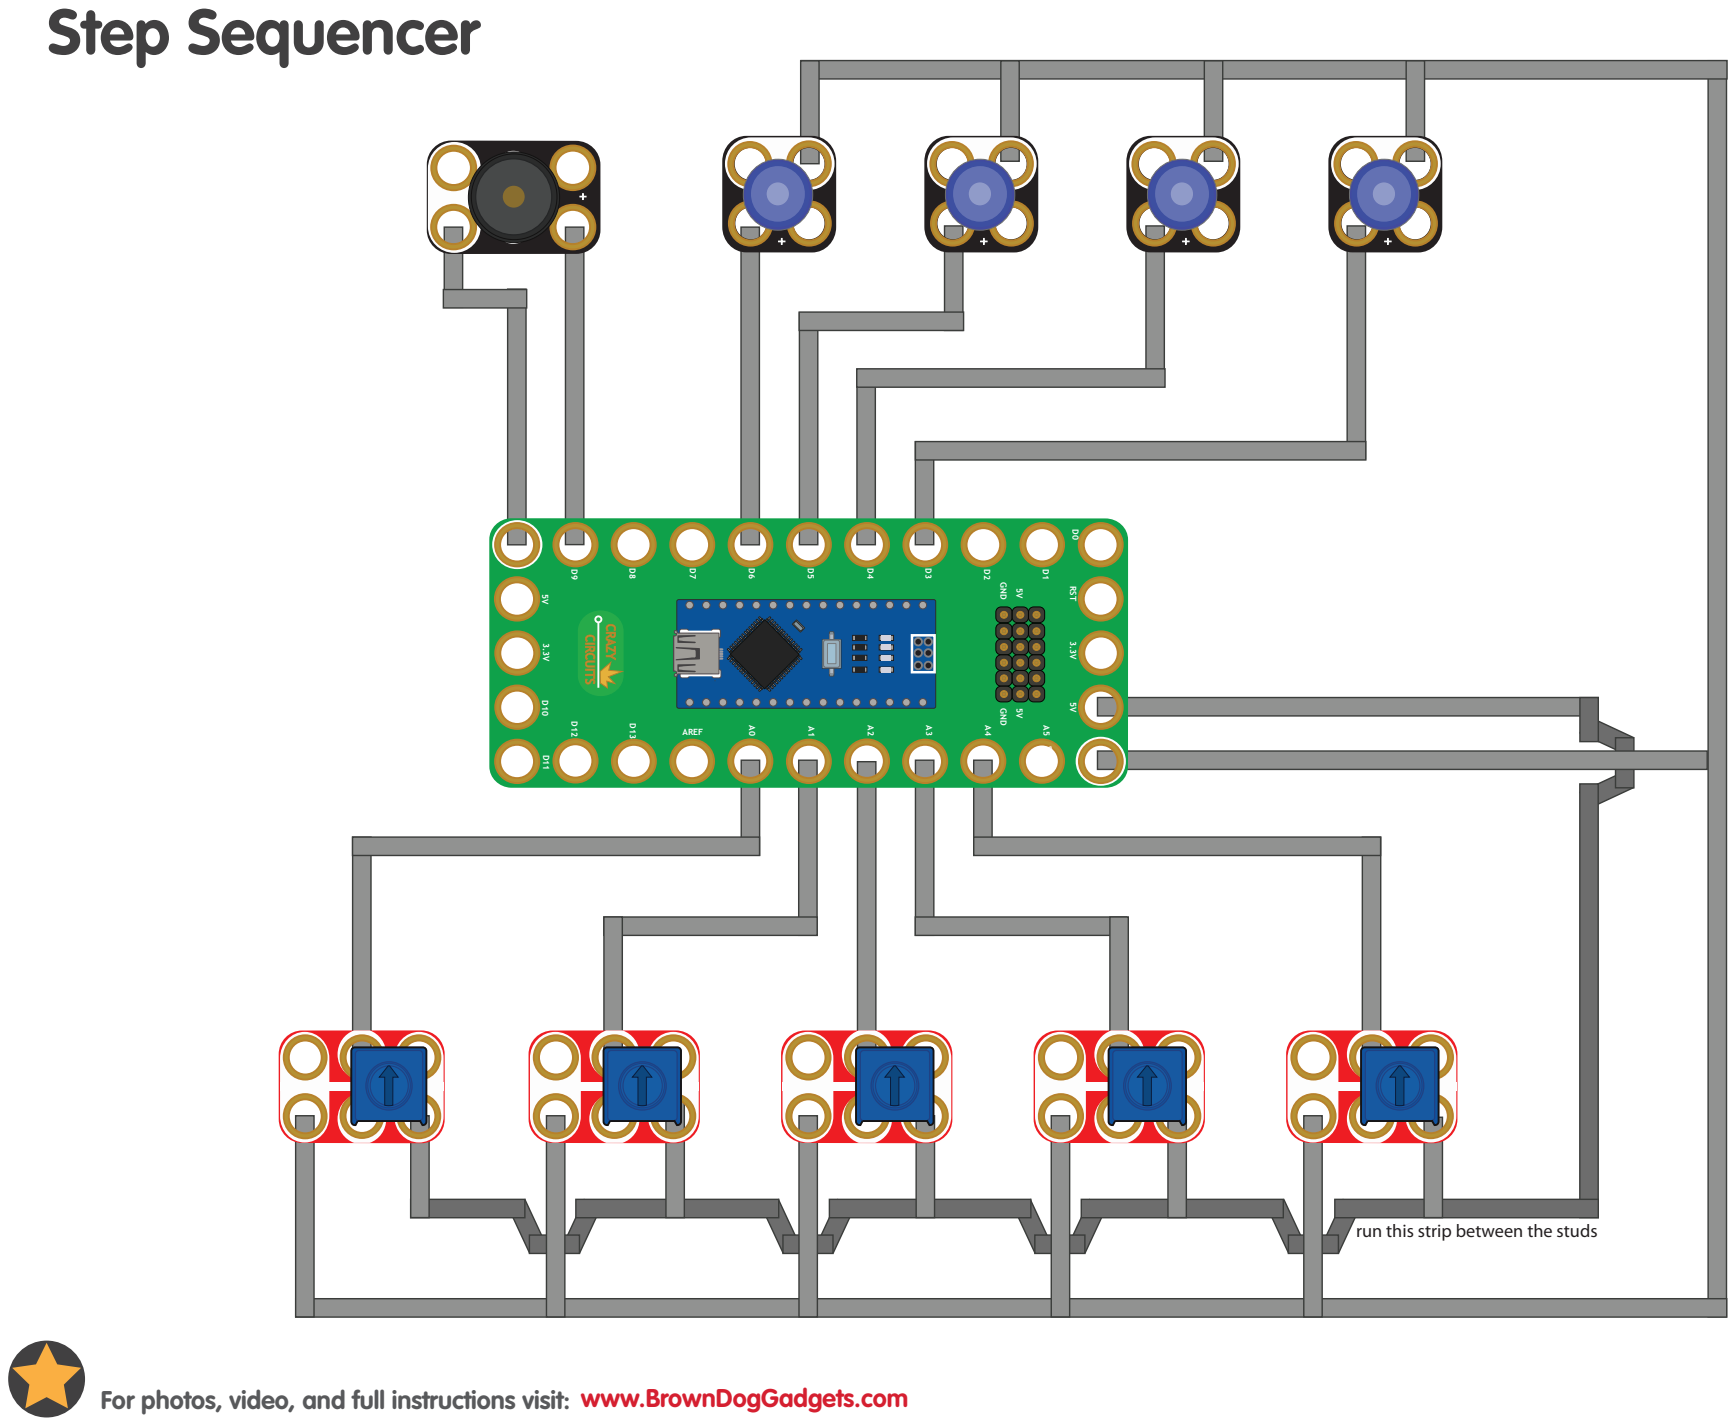
[picture p454: page 1]

run this strip between the studs

For photos, video, and full instructions visit: www.BrownDogGadgets.com
