BrownDogGadgets/CrazyCircuits/Projects/Pillow Dice/Pillow diagram.pdf

# Die Pillow

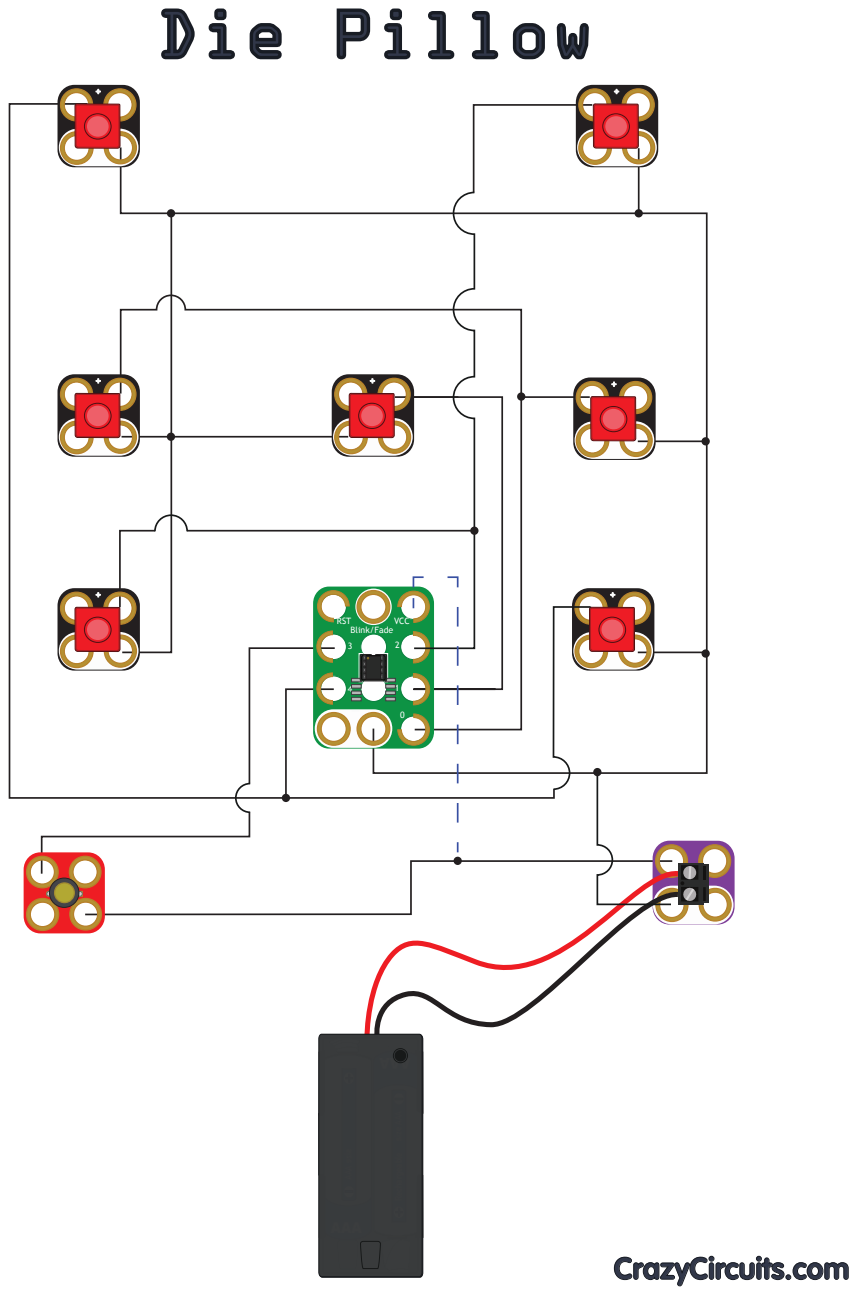
[picture p455: page 1]
RST; VCC; Blink/Fade; size AAA; Rechargeable +; CrazyCircuits.com
