BrownDogGadgets/CrazyCircuits/Projects/Larson Scanner/Larson Robotics Diagram.pdf

# Robatics Larson Scanner

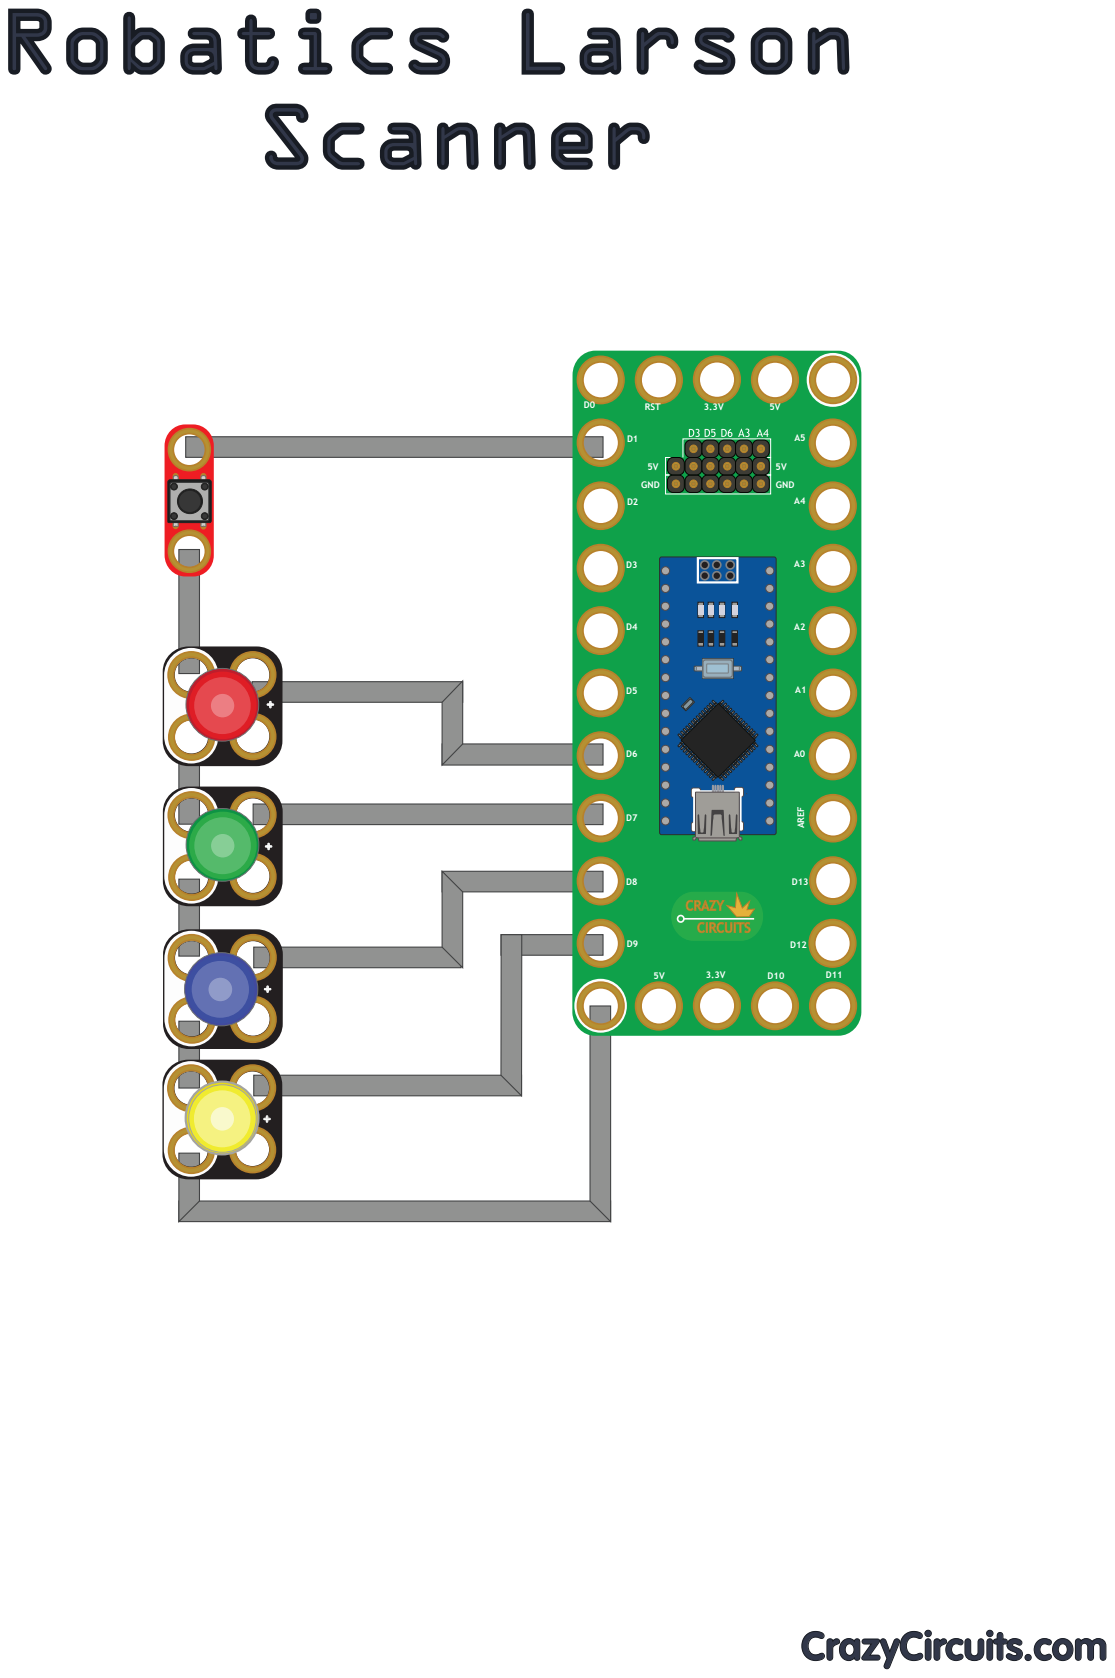
[picture p456: page 1]
