BrownDogGadgets/CrazyCircuits/Projects/Larson Scanner/Larson Touch Diagram.pdf

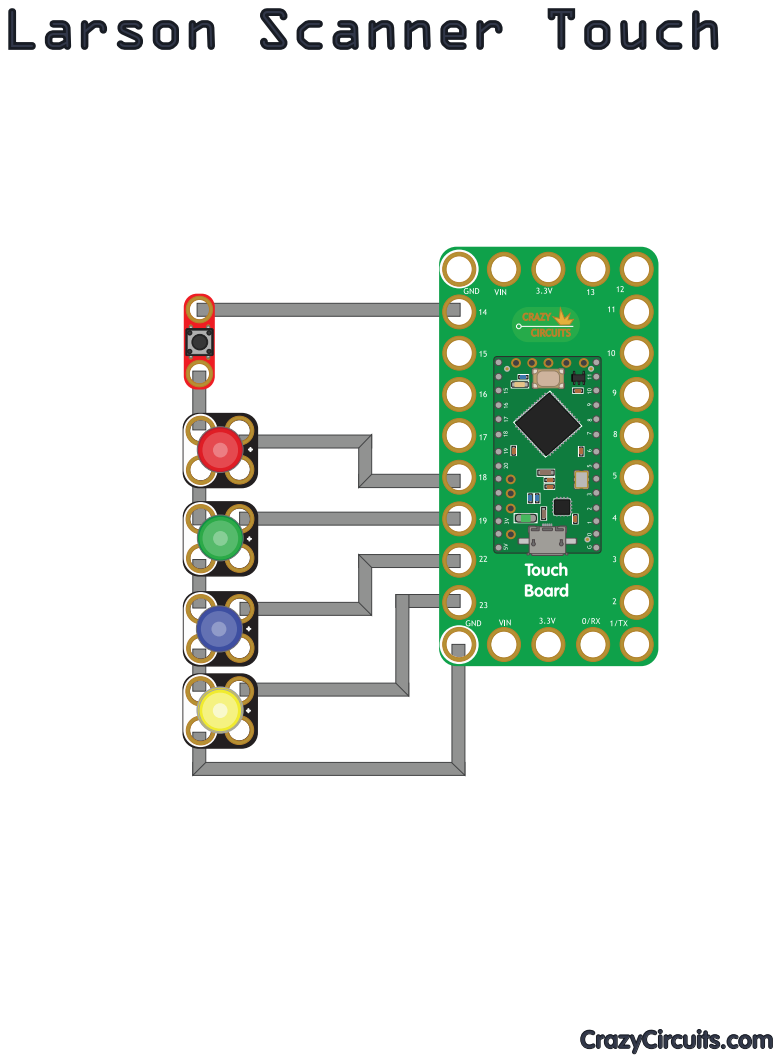
[picture p457: page 1]
CrazyCircuits.com

Larson Scanner Touch
