BrownDogGadgets/CrazyCircuits/Projects/Blink Fade/Ambulance Diagram.pdf

## Ambulance

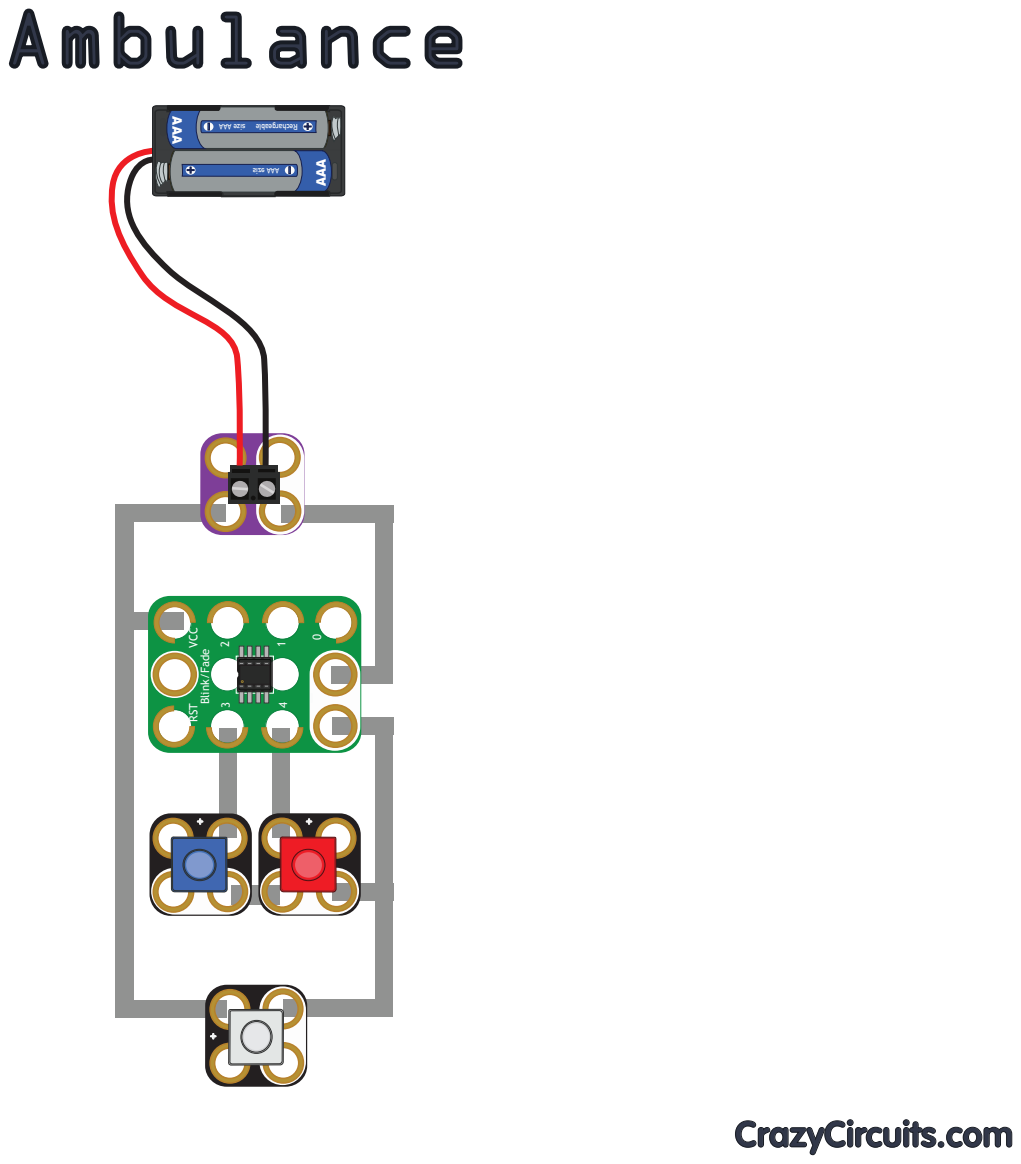
[picture p458: page 1]
RST VCC; Blink/Fade; AAA+ size AAA; AAA; CrazyCircuits.com
