BrownDogGadgets/CrazyCircuits/Projects/Game of Simon/Simon Robotics Board Diagram.pdf

# Simon Robatics

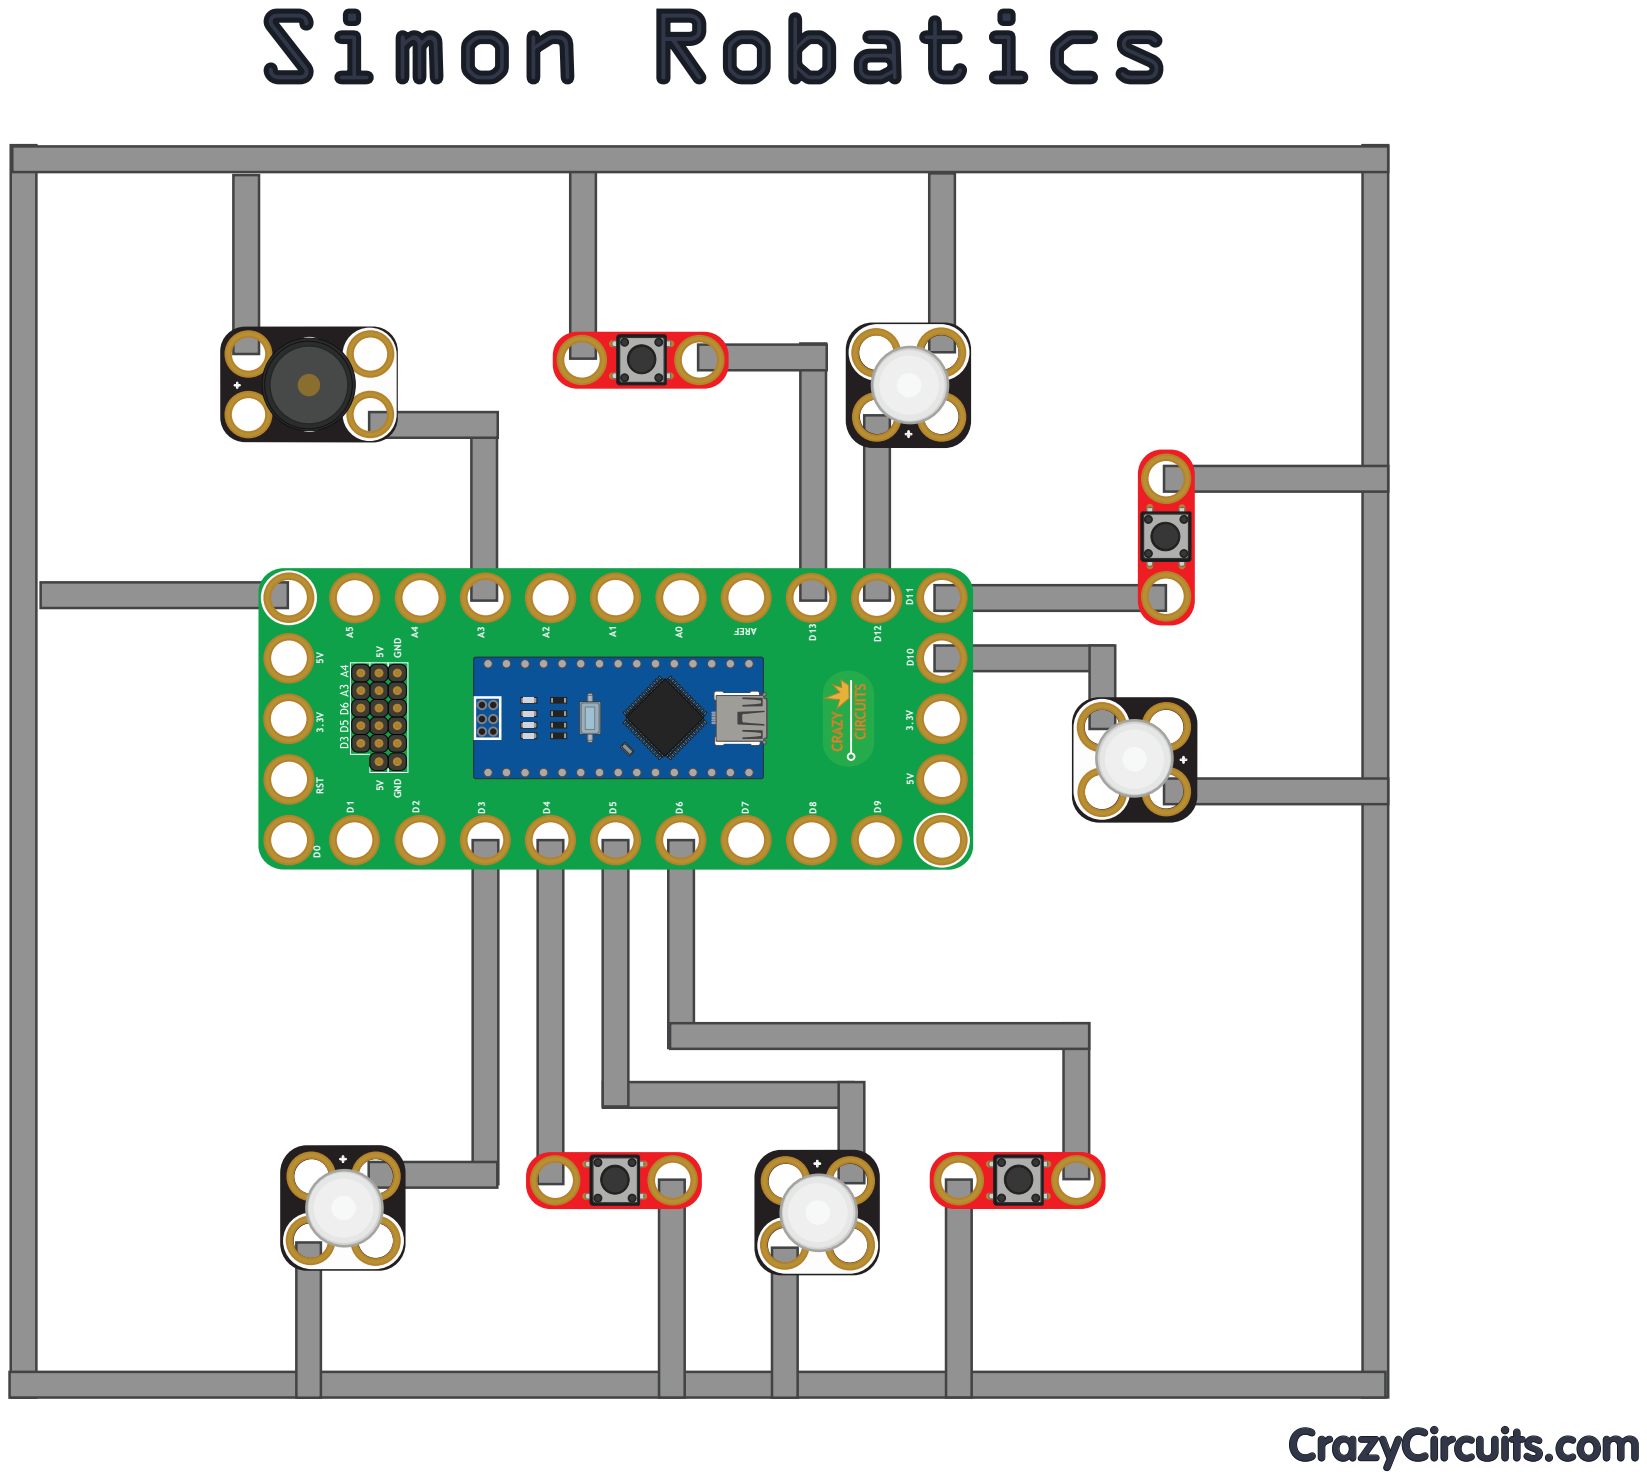
[picture p459: page 1]
