BrownDogGadgets/CrazyCircuits/Projects/NES Controller/LEGO Controller Wood v13 LC.pdf

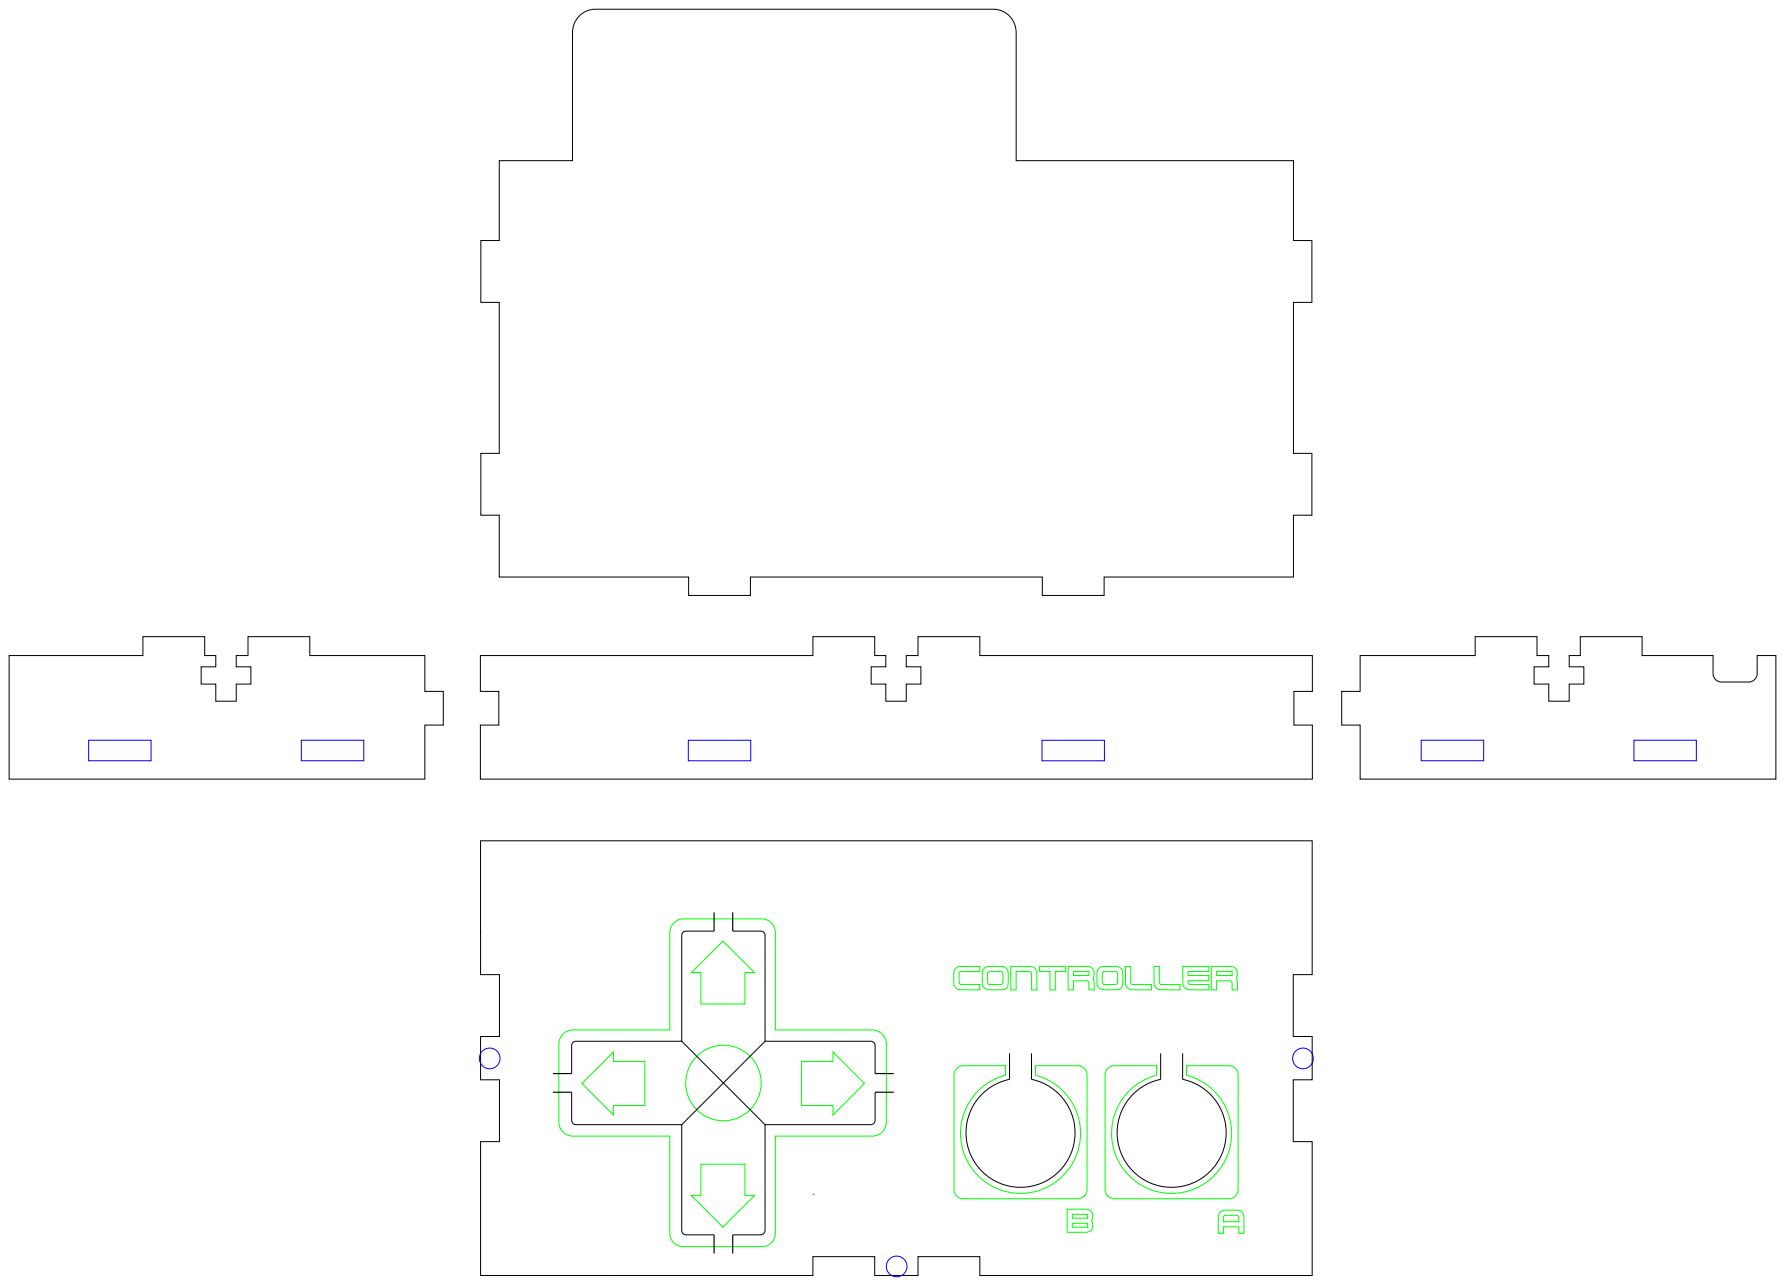
[picture p460: page 1]
