BrownDogGadgets/CrazyCircuits/Laser Cut Files/NES Controller/LEGO Controller Wood v11 LC.pdf

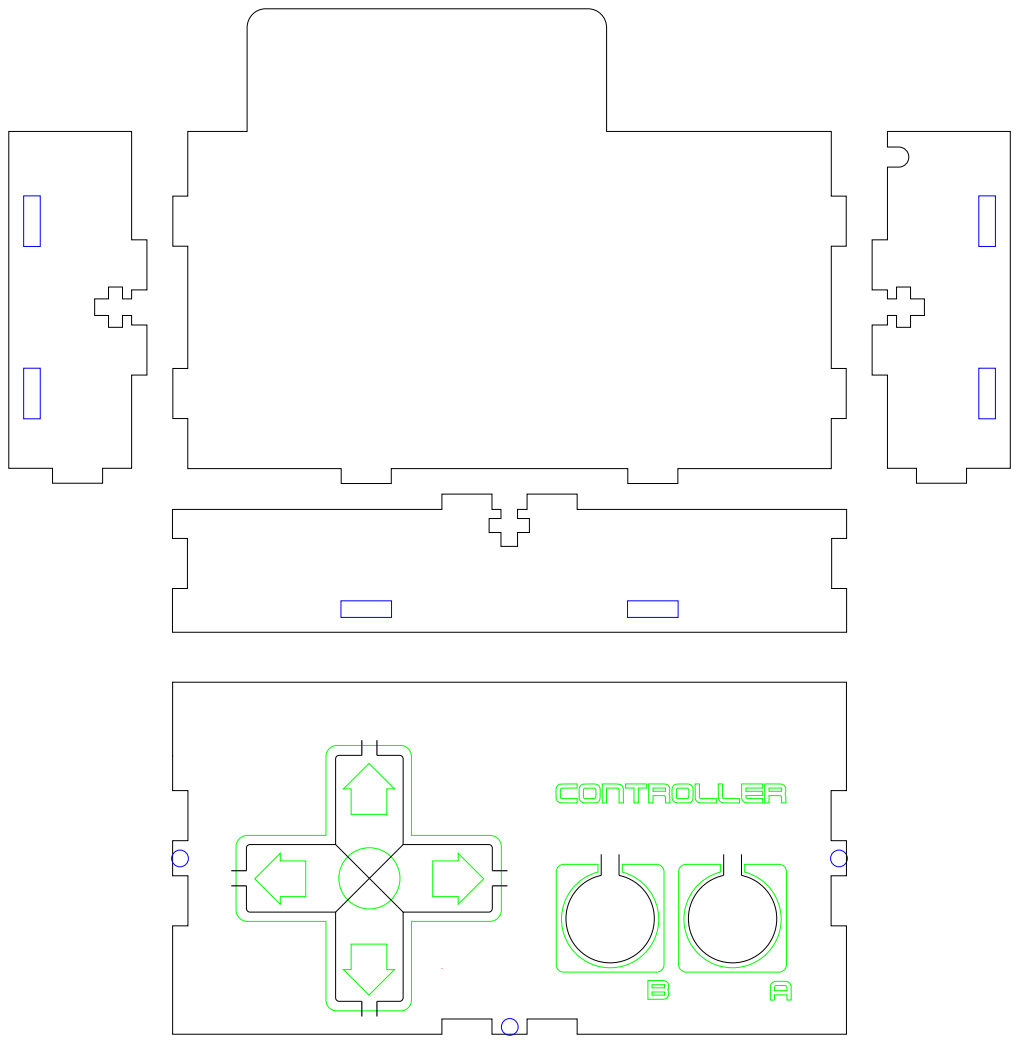
[picture p461: page 1]
