BrownDogGadgets/CrazyCircuits/Laser Cut Files/Servo to Brick Adaptors/LEGO Servo Gear Plus v01.pdf

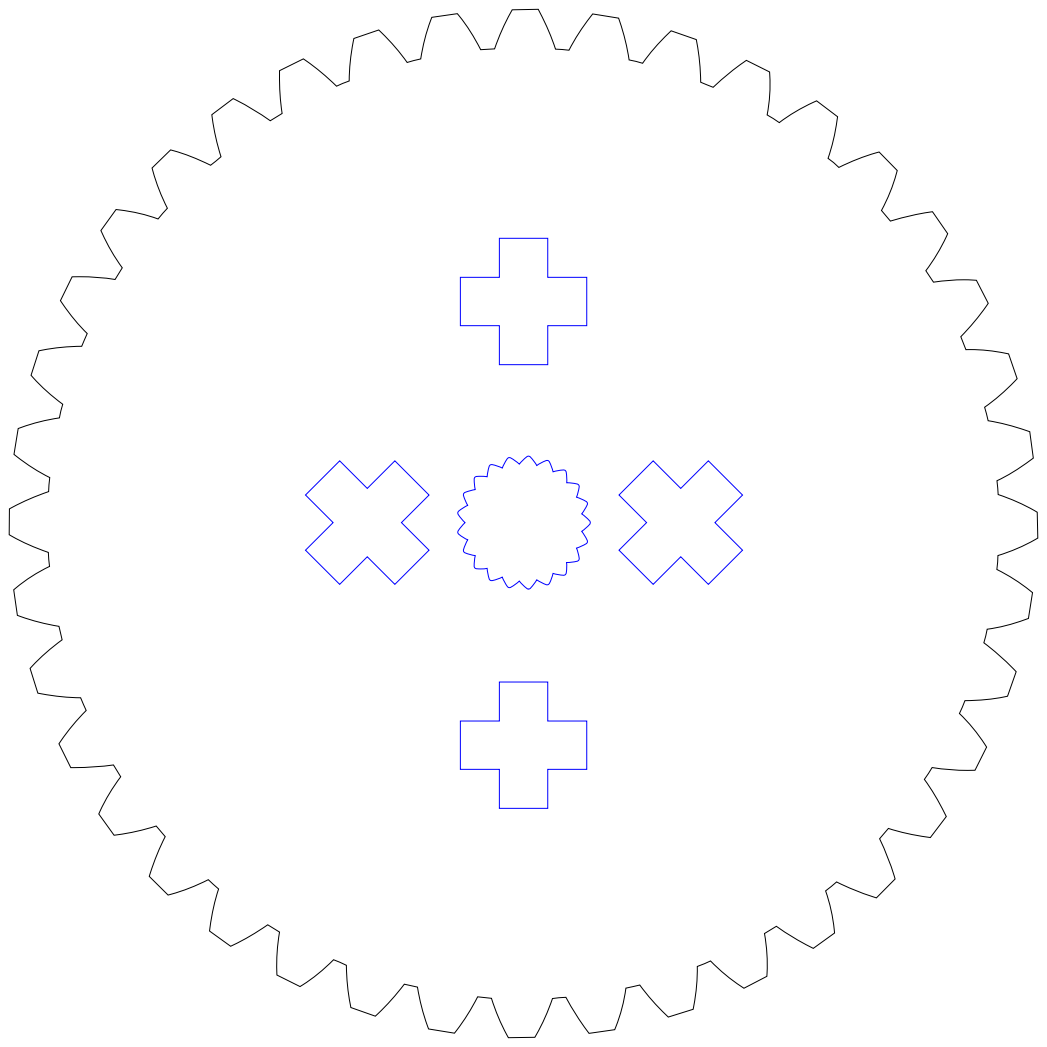
[picture p462: page 1]
