BrownDogGadgets/CrazyCircuits/Laser Cut Files/Servo to Brick Adaptors/LEGO Servo Gear v03.pdf

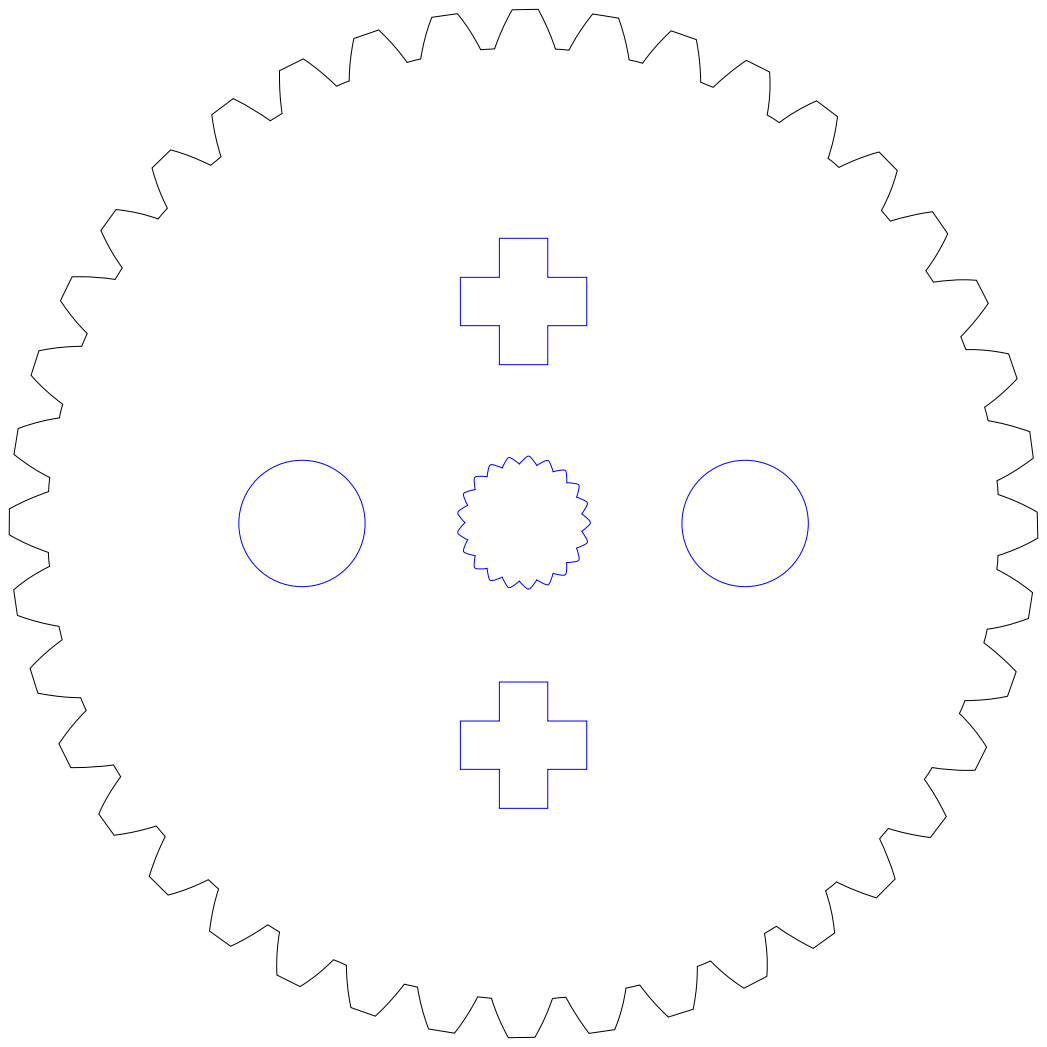
[picture p463: page 1]
