BrownDogGadgets/CrazyCircuits/Circuit-Kits/Circuit-Kits/10mmLED-Button-Battery/10mmLED-Button-Battery.sch

## KiCad design Circuit-Kits/Circuit-Kits/10mmLED-Button-Battery/10mmLED-Button-Battery.sch (2017-02-14)

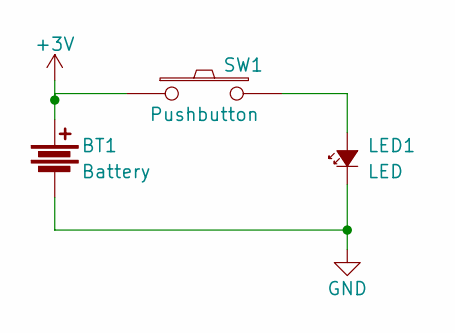
[picture p464: schematic 10mmLED-Button-Battery.sch]

Parts:
BT1: Battery; CR2032-3x3-NO-ROTATE
LED1: LED; LED-5MMD-2.5MMP-2x2
SW1: Pushbutton; BUTTON-1x3-TH-OMRON-B3F-1XXX

Connections:
+3V: BT1.+, SW1.1
GND: BT1.GND, LED1.-
unnamed: LED1.+, SW1.2
