BrownDogGadgets/CrazyCircuits/Circuit-Kits/Circuit-Kits/SMTLimitLED-SMTButton-Battery/SMTLimitLED-SMTButton-Battery.sch

## KiCad design Circuit-Kits/Circuit-Kits/SMTLimitLED-SMTButton-Battery/SMTLimitLED-SMTButton-Battery.sch (2017-07-07)

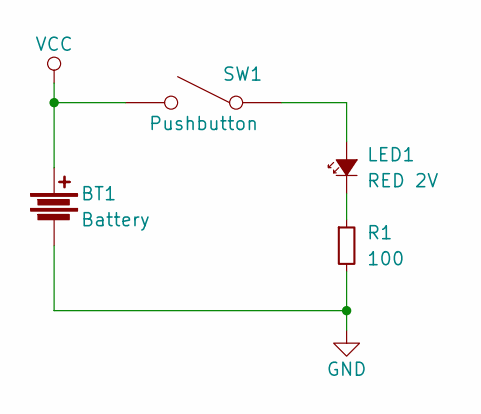
[picture p465: schematic SMTLimitLED-SMTButton-Battery.sch]

Parts:
BT1: Battery; CR2032-3x3
LED1: RED 2V; LED-SMT-1206-2x2-LIMITED
R1: 100
SW1: Pushbutton; SWITCH-6mm-SQUARE-PTS645-SMT-2x3

Connections:
GND: BT1.GND, R1.2
unnamed: LED1.+, SW1.2
unnamed: LED1.-, R1.1
VCC: BT1.+, SW1.1
