BrownDogGadgets/CrazyCircuits/Circuit-Kits/Circuit-Kits/USB-Breakout-with-Reset/USB-Breakout-with-Reset.sch

## KiCad design Circuit-Kits/Circuit-Kits/USB-Breakout-with-Reset/USB-Breakout-with-Reset.sch (2016-11-21)

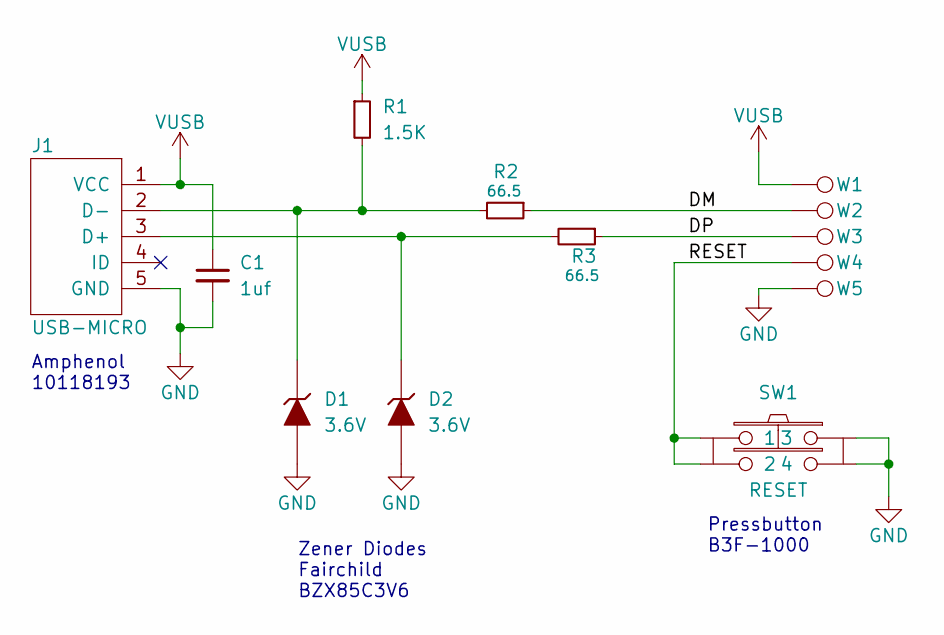
[picture p466: schematic USB-Breakout-with-Reset.sch]

Parts:
C1: 1uf; CAP-DISC-D7.5MM-P5MM
D1, D2: 3.6V; DIODE-DO-41
J1: USB-MICRO; CONN-USB-MICRO-B-AMPHENOL-10118193-0001LF
R1: 1.5K; RES-CARBONFILM-7MM
R2, R3: 66.5; RES-CARBONFILM-7MM
SW1: RESET; SWITCH-OMRON-MOMENTARY-TH-B3F-10XX
W1, W2, W3, W4, W5: TEST_1P; STANDALONE-LEGO-HOLE-PLATED

Connections:
DM: R2.1, W2.1
DP: R3.1, W3.1
GND: C1.2, D1.2 (A), D2.2 (A), J1.5 (GND), SW1.3, SW1.4, W5.1
unnamed: D1.1 (K), J1.2 (D-), R1.2, R2.2
unnamed: D2.1 (K), J1.3 (D+), R3.2
RESET: SW1.1, SW1.2, W4.1
VUSB: C1.1, J1.1 (VCC), R1.1, W1.1

Notes on the sheet:
Zener Diodes Fairchild BZX85C3V6
Amphenol 10118193
Pressbutton B3F-1000
