BrownDogGadgets/CrazyCircuits/Circuit-Kits/Circuit-Kits/VibeMotor-Button-Battery/VibeMotor-Button-Battery.sch

## KiCad design Circuit-Kits/Circuit-Kits/VibeMotor-Button-Battery/VibeMotor-Button-Battery.sch (2017-02-14)

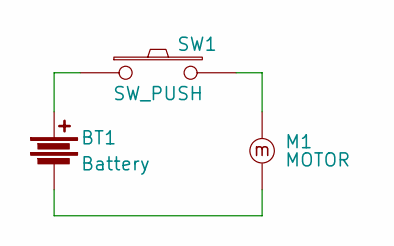
[picture p467: schematic VibeMotor-Button-Battery.sch]

Parts:
BT1: Battery
M1: MOTOR
SW1: SW_PUSH

Connections:
unnamed: BT1.+, SW1.1
unnamed: BT1.GND, M1.2
unnamed: M1.1, SW1.2
