BrownDogGadgets/CrazyCircuits/Projects/BDG_Large_MicroBit/Arduino/BDG_Large_MicroBit/patterns.h

/*
 * patterns.h
 * 
 * https://wiki.seeedstudio.com/XIAO-RP2040/
 *
 *
 */

// design all of our patterns
/* ----------------------------------------------- */

int blank[25]={
  0,0,0,0,0,
  0,0,0,0,0,
  0,0,0,0,0,
  0,0,0,0,0,
  0,0,0,0,0
};

/* ----------------------------------------------- */

int smile[25]={
  0,0,0,0,0,
  0,1,0,1,0,
  0,0,0,0,0,
  1,0,0,0,1,
  0,1,1,1,0
};

int sad[25]={
  0,0,0,0,0,
  0,1,0,1,0,
  0,0,0,0,0,
  0,1,1,1,0,
  1,0,0,0,1
};

int ghost[25]={
  0,1,1,1,0,
  1,0,1,0,1,
  1,1,1,1,1,
  1,1,1,1,1,
  1,0,1,0,1
};

int duck[25]={
  0,1,1,0,0,
  1,1,1,0,0,
  0,1,1,1,1,
  0,1,1,1,0,
  0,0,0,0,0
};

int heart[25]={
  0,1,0,1,0,
  1,1,1,1,1,
  1,1,1,1,1,
  0,1,1,1,0,
  0,0,1,0,0
};

int umbrella[25]={
  0,1,1,1,0,
  1,1,1,1,1,
  0,0,1,0,0,
  1,0,1,0,0,
  1,1,1,0,0
};

int checkmark[25]={
  0,0,0,0,0,
  0,0,0,0,1,
  0,0,0,1,0,
  1,0,1,0,0,
  0,1,0,0,0
};

int house[25]={
  0,0,1,0,0,
  0,1,1,1,0,
  1,1,1,1,1,
  0,1,0,1,0,
  0,1,0,1,0
};

int skull[25]={
  0,1,1,1,0,
  1,0,1,0,1,
  1,1,1,1,1,
  0,1,1,1,0,
  0,1,1,1,0
};

int scissors[25]={
  1,1,0,0,1,
  1,1,0,1,0,
  0,0,1,0,0,
  1,1,0,1,0,
  1,1,0,0,1
};

int target[25]={
  0,0,1,0,0,
  0,1,1,1,0,
  1,1,0,1,1,
  0,1,1,1,0,
  0,0,1,0,0
};

int tortoise[25]={
  0,0,0,0,0,
  0,1,1,1,0,
  1,1,1,1,1,
  0,1,0,1,0,
  0,0,0,0,0
};

int asleep[25]={
  0,0,0,0,0,
  1,1,0,1,1,
  0,0,0,0,0,
  0,1,1,1,0,
  0,0,0,0,0
};

int triangle[25]={
  0,0,0,0,0,
  0,0,1,0,0,
  0,1,0,1,0,
  1,1,1,1,1,
  0,0,0,0,0
};

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
  0,0,0,0,0,
  1,1,1,1,1,
  0,0,0,0,0,
  0,0,0,0,0
};

int larsonRows4[25]={
  0,0,0,0,0,
  0,0,0,0,0,
  0,0,0,0,0,
  1,1,1,1,1,
  0,0,0,0,0
};

int larsonRows5[25]={
  0,0,0,0,0,
  0,0,0,0,0,
  0,0,0,0,0,
  0,0,0,0,0,
  1,1,1,1,1,
};

/* ----------------------------------------------- */
